boert/JU-TE-Computer/Bilder/Speichermodul_Typ_A.jpg

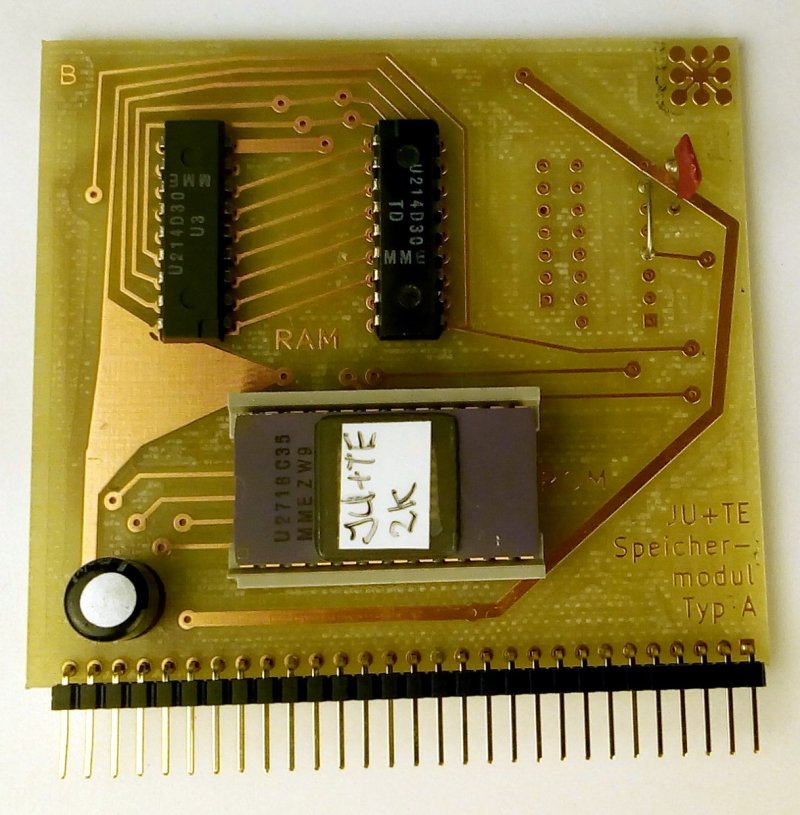
Bilder/Speichermodul_Typ_A.jpg
