boert/JU-TE-Computer/Erweiterungen/Schaltplan__V24-Interface.pdf

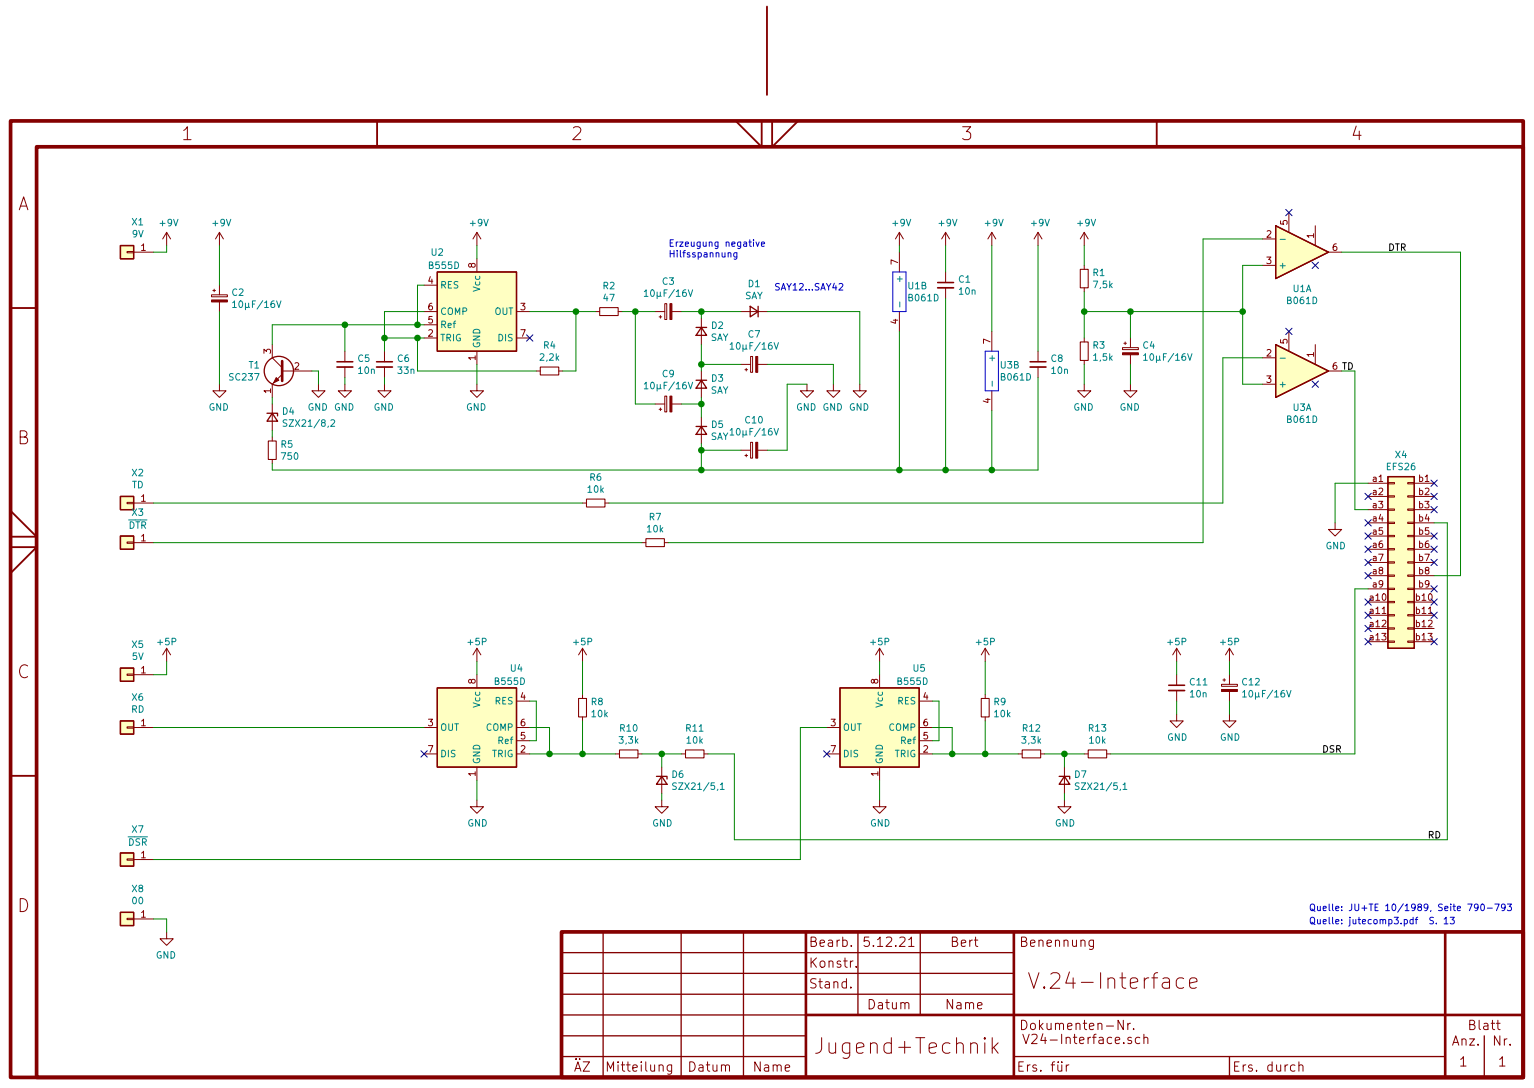
[picture p29: page 1]

1 TRIG 2 OUT 3 RES 4 Ref 5 COMP 6 DIS 7 Vcc 8 U2 B555D

1 TRIG 2 OUT 3 RES 4 Ref 5 COMP 6 DIS 7 Vcc 8 U4 B555D GND GND GND

1 TRIG 2 OUT 3 RES 4 Ref 5 COMP 6 DIS 7 Vcc 8 U5 B555D

Datum | Name

Dokumenten-Nr. | | Blatt
