boert/JU-TE-Computer/Erweiterungen/Schaltplan__Magnetbandanschluss.pdf

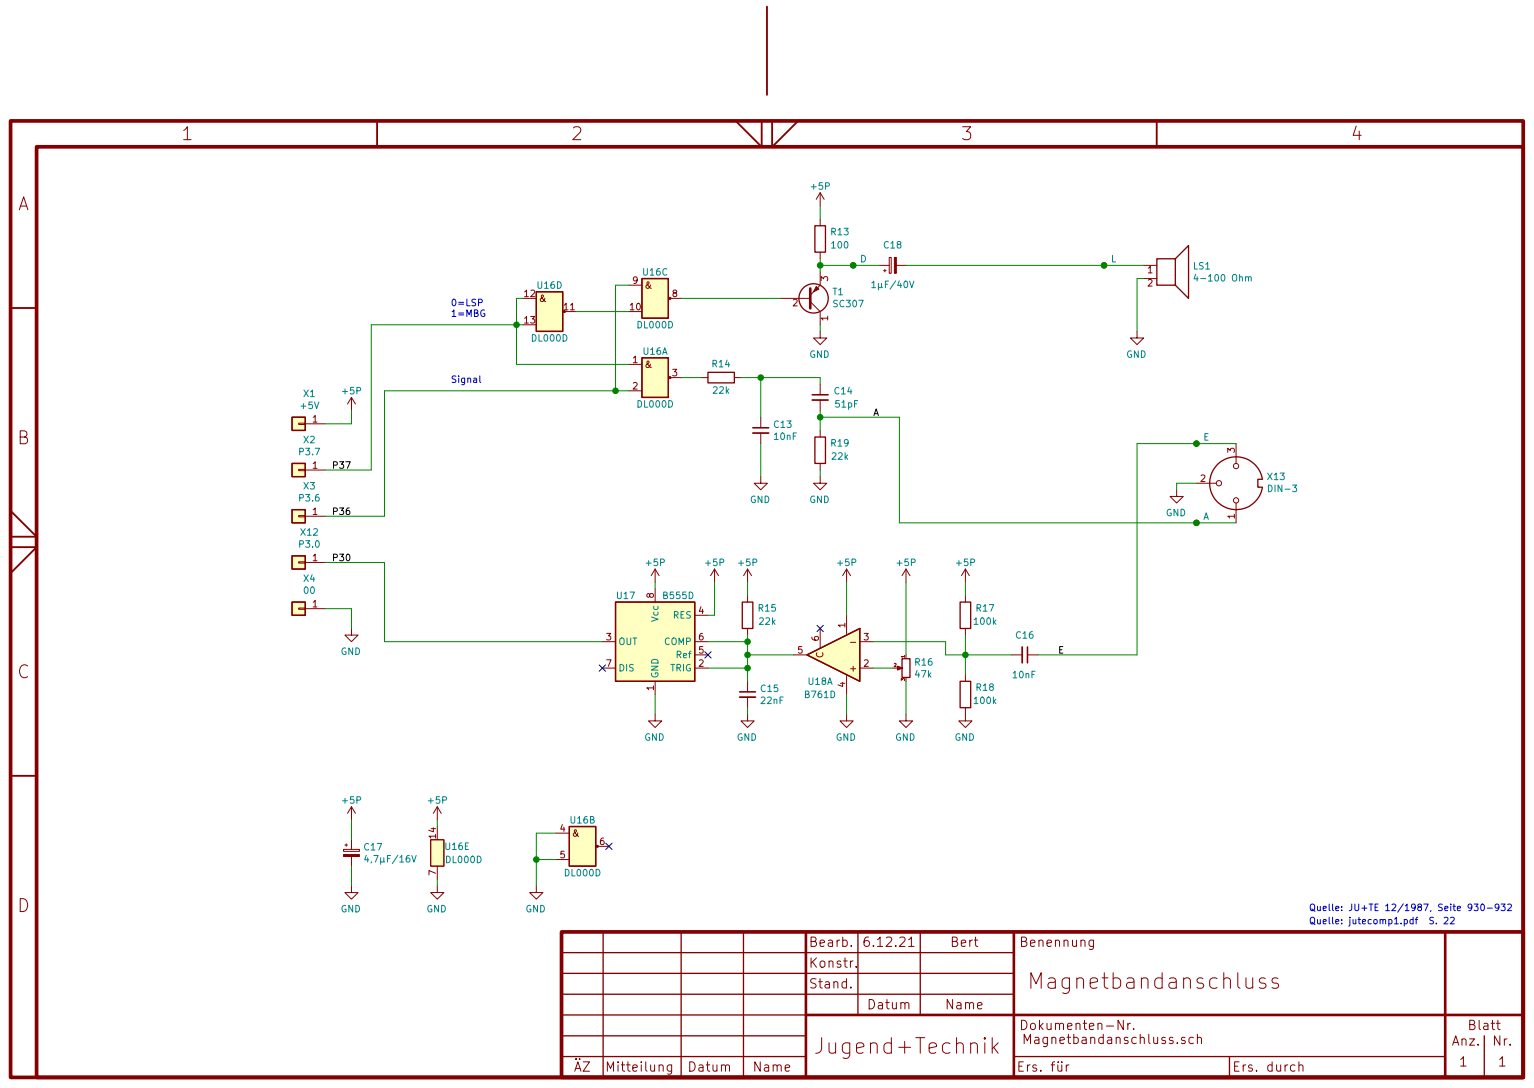
[picture p46: page 1]

1 TRIG 2 OUT 3 RES 4 Ref 5 COMP 6 DIS 7 Vcc U17 8B555D

Quelle: JU+TE 12/1987, Seite 930-932 Quelle: jutecomp1.pdf S. 22

Datum | Name

Dokumenten-Nr. | | Blatt
