boert/JU-TE-Computer/Erweiterungen/Schaltplan__AD-Wandler.pdf

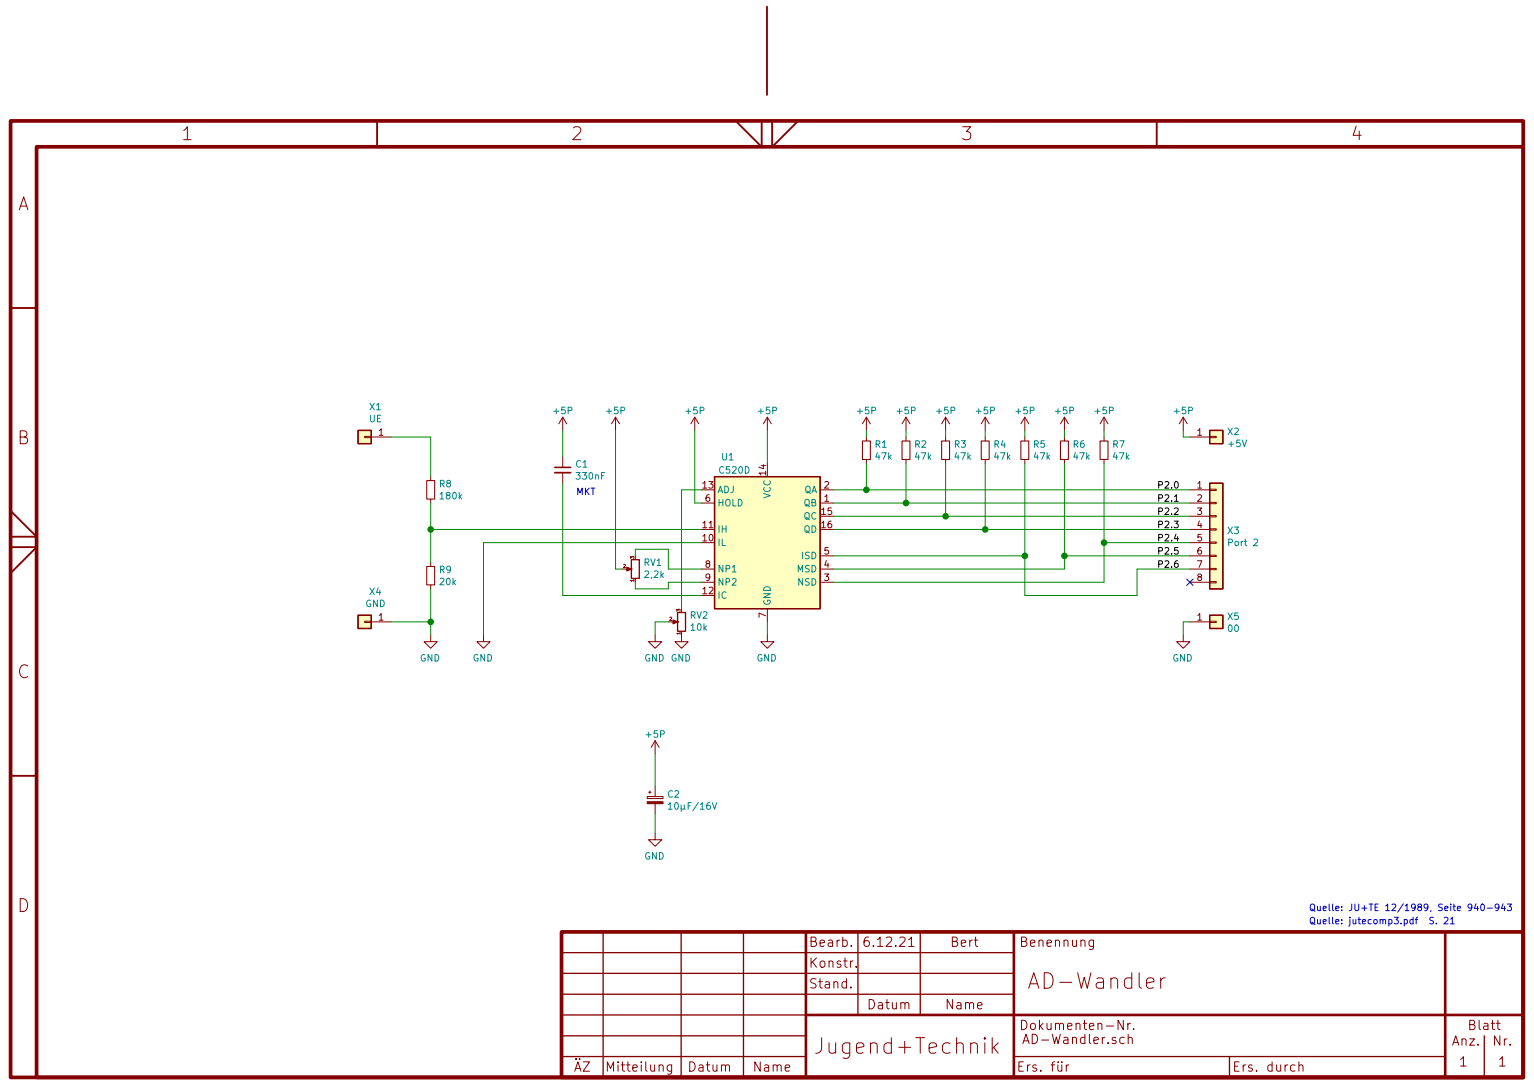
[picture p47: page 1]

Datum | Name

Dokumenten-Nr. | | Blatt
