boert/JU-TE-Computer/Erweiterungen/Schaltplan__IFSS-Interface.pdf

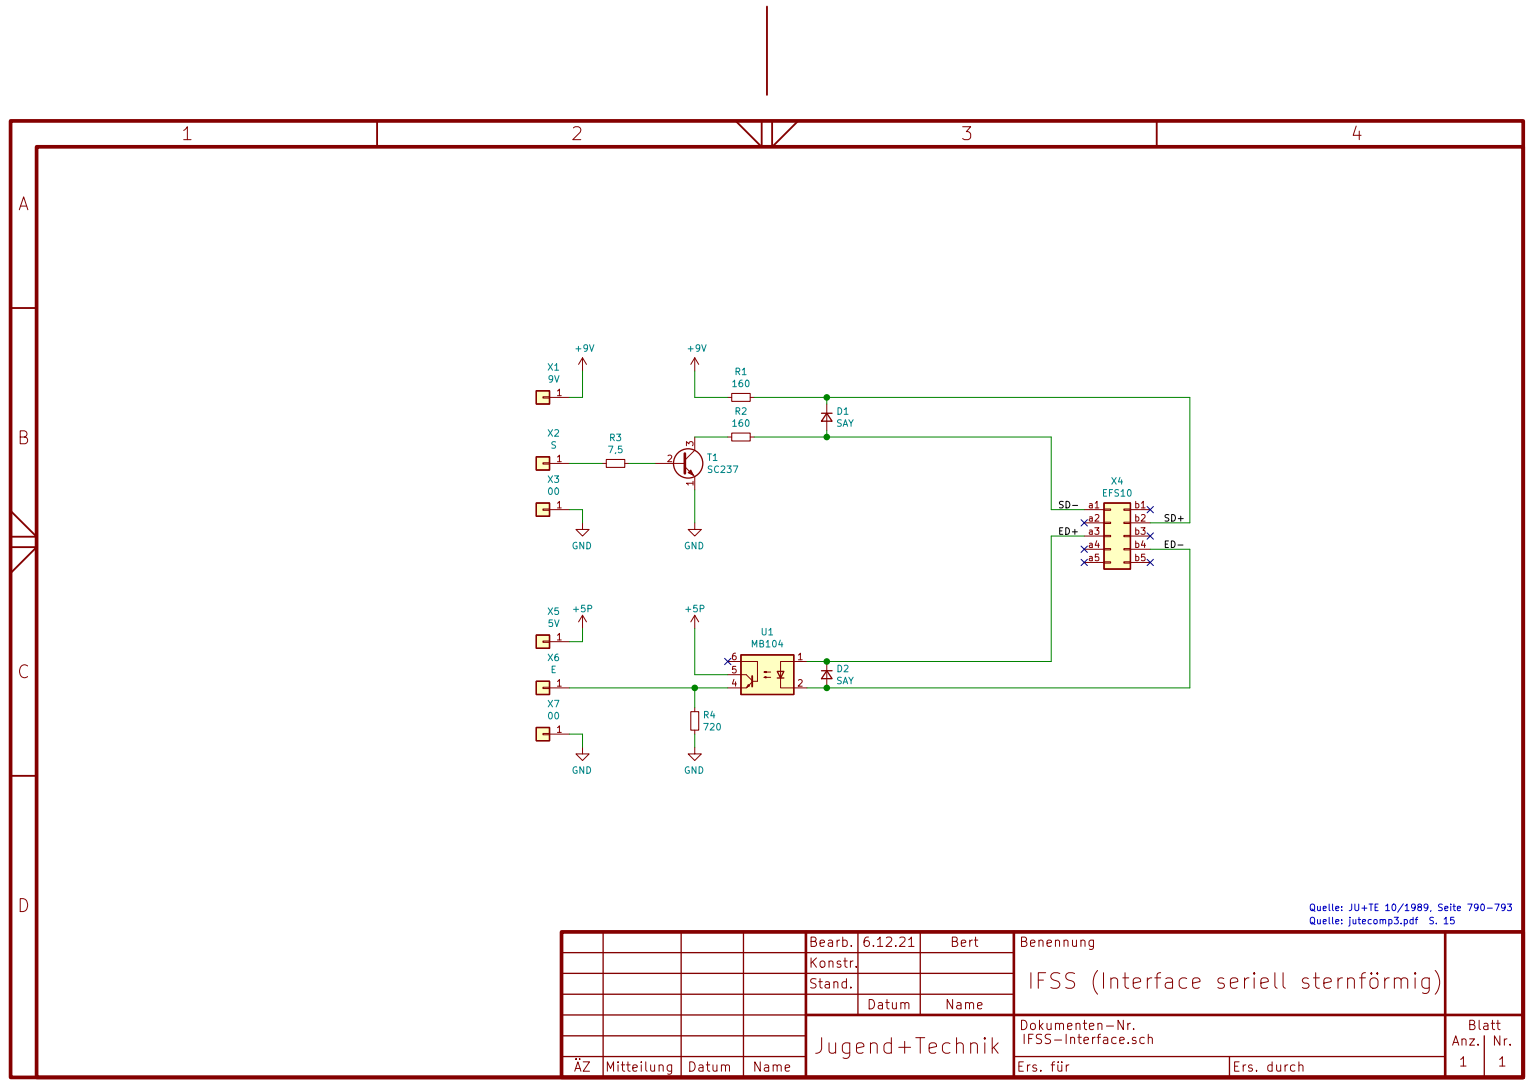
[picture p48: page 1]

Benennung
IFSS (Interface seriell sternförmig)

Datum | Name

Dokumenten-Nr. | | Blatt
