boert/JU-TE-Computer/Erweiterungen/Platine__Speichermodul_Typ_A.pdf

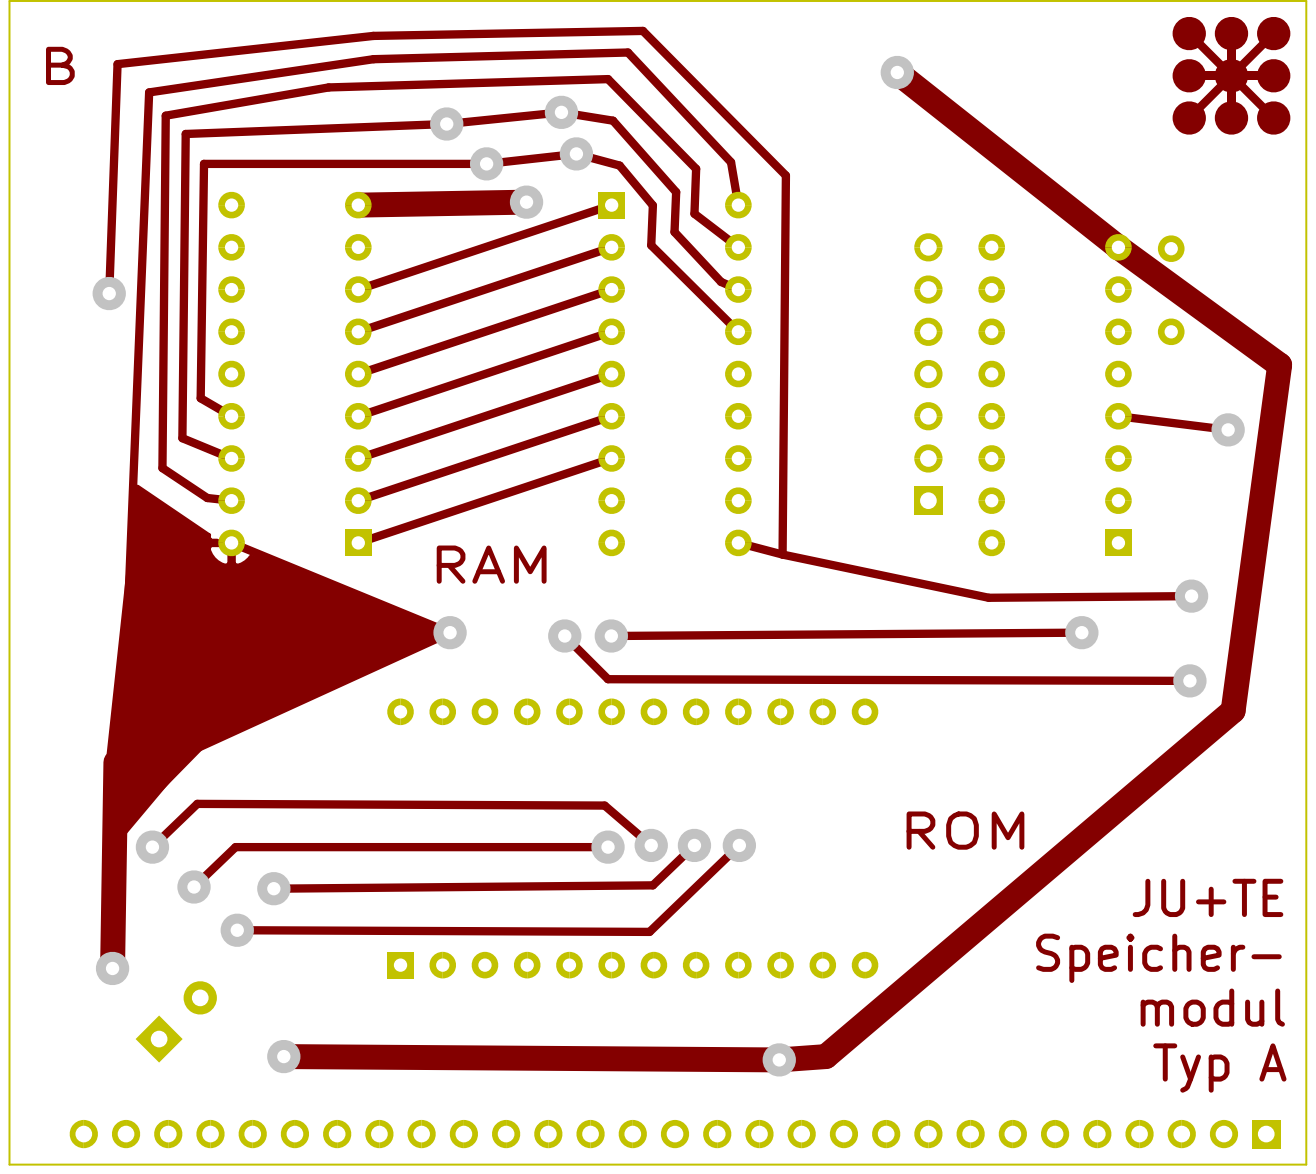
[picture p49: page 1]

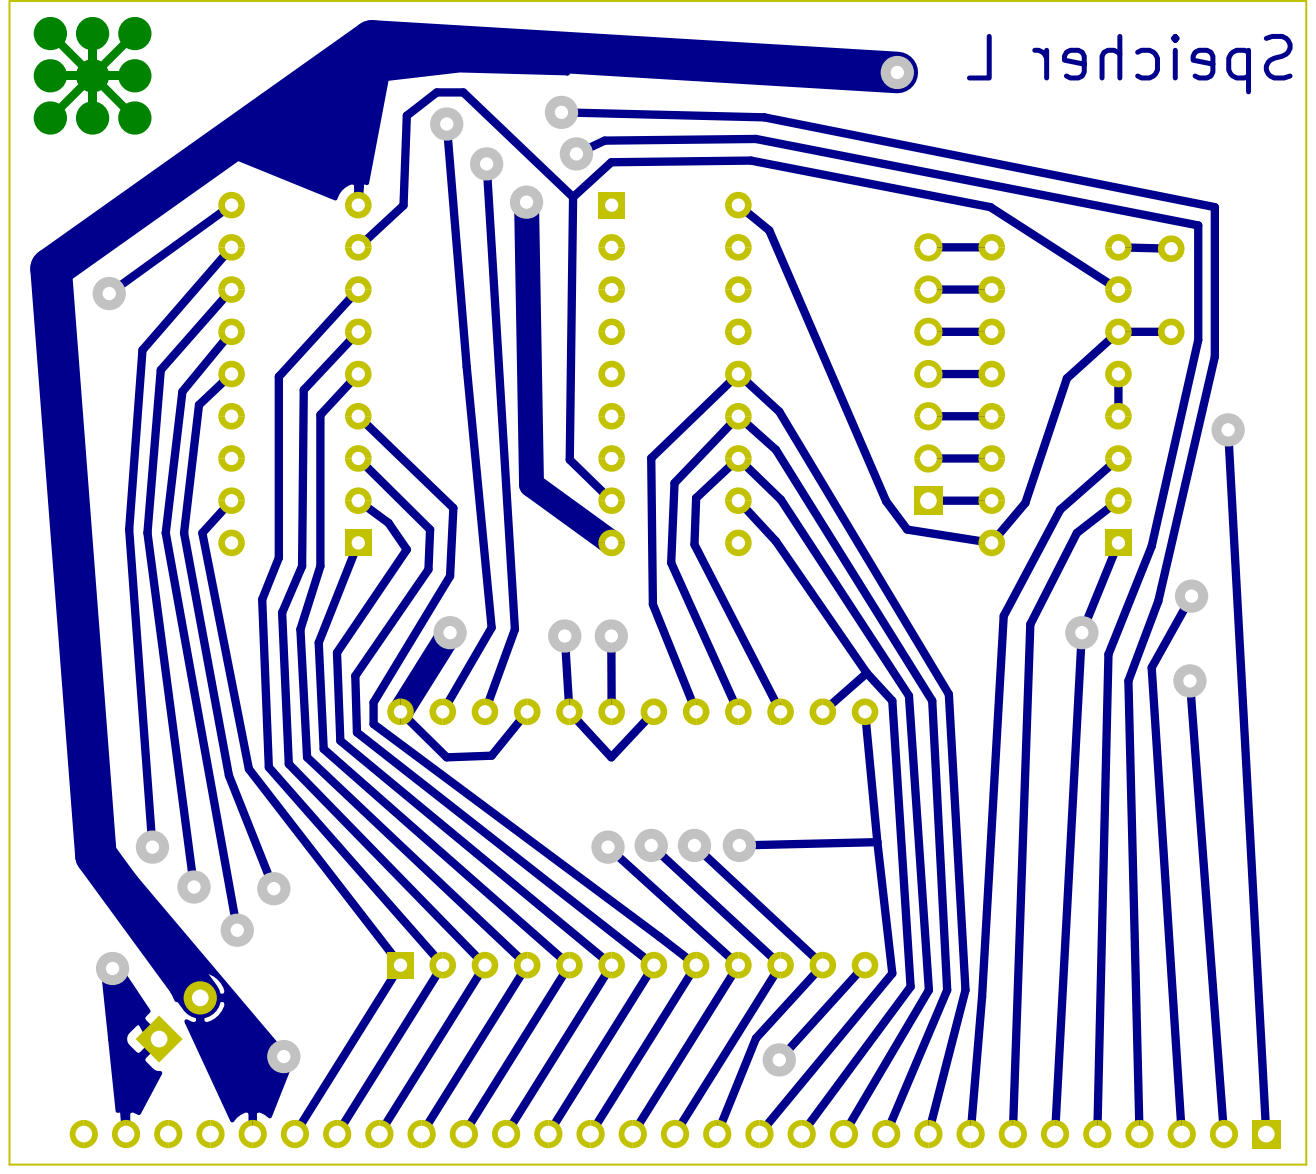
[picture p50: page 2]

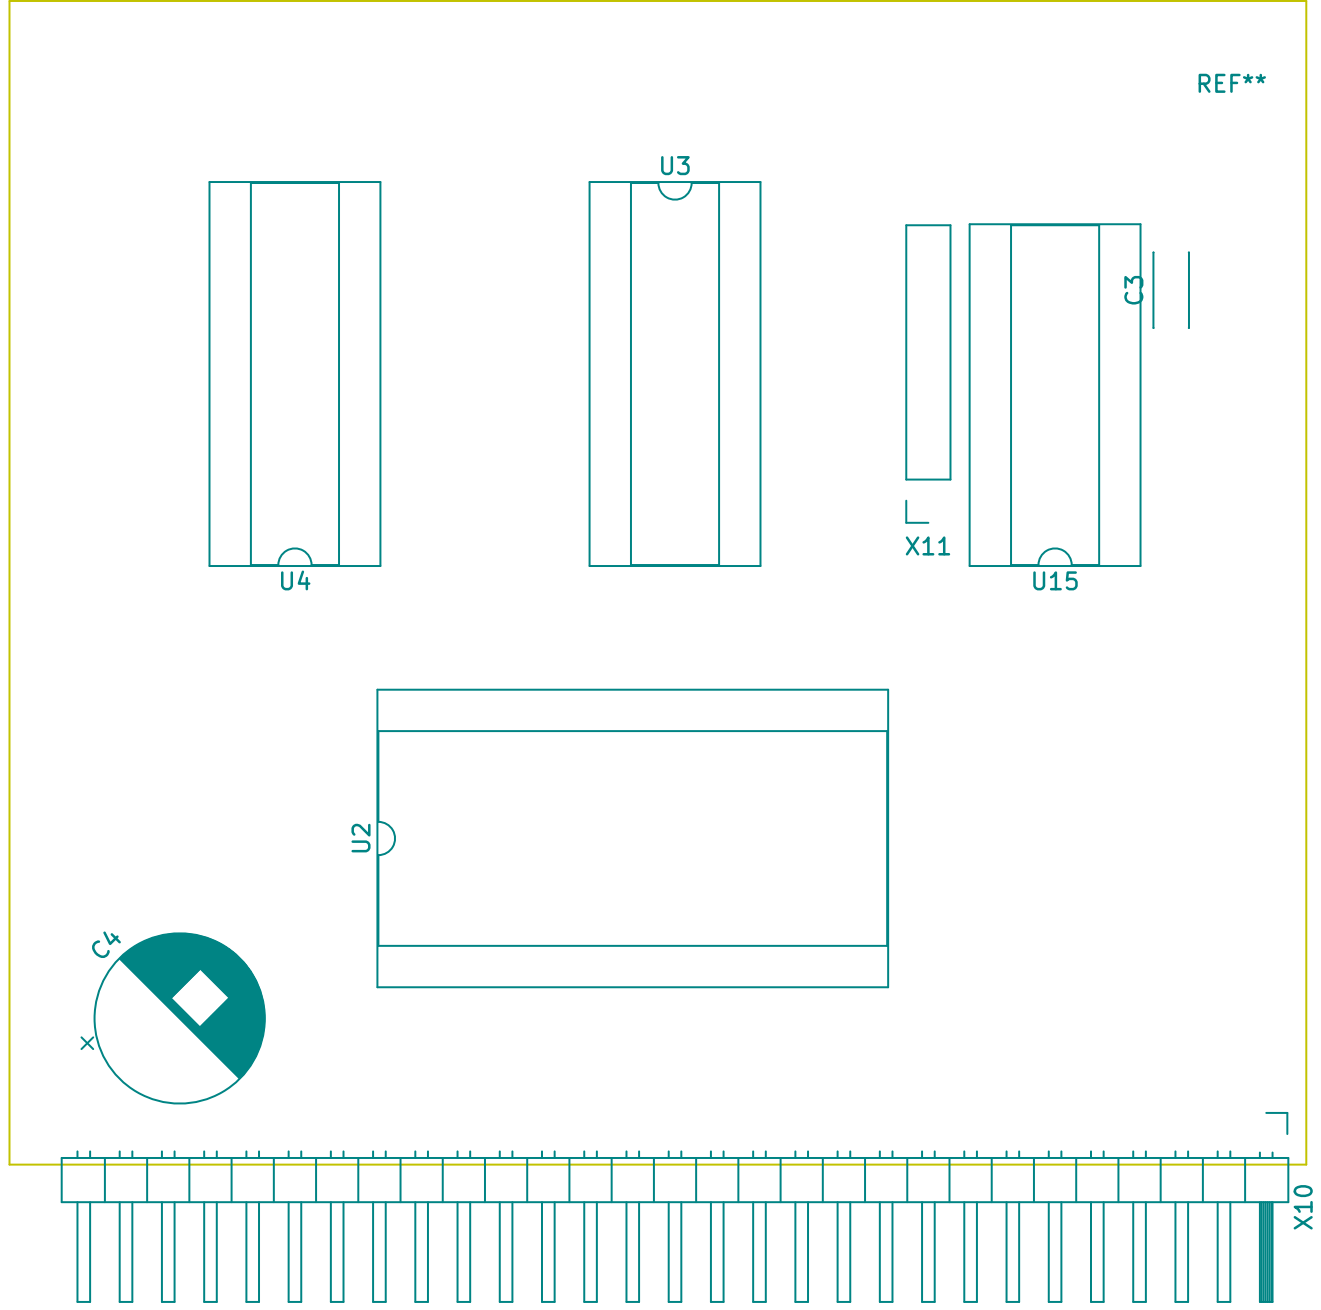
[picture p51: page 3]
