boert/JU-TE-Computer/Erweiterungen/Platine__Speichermodul_Typ_B.pdf

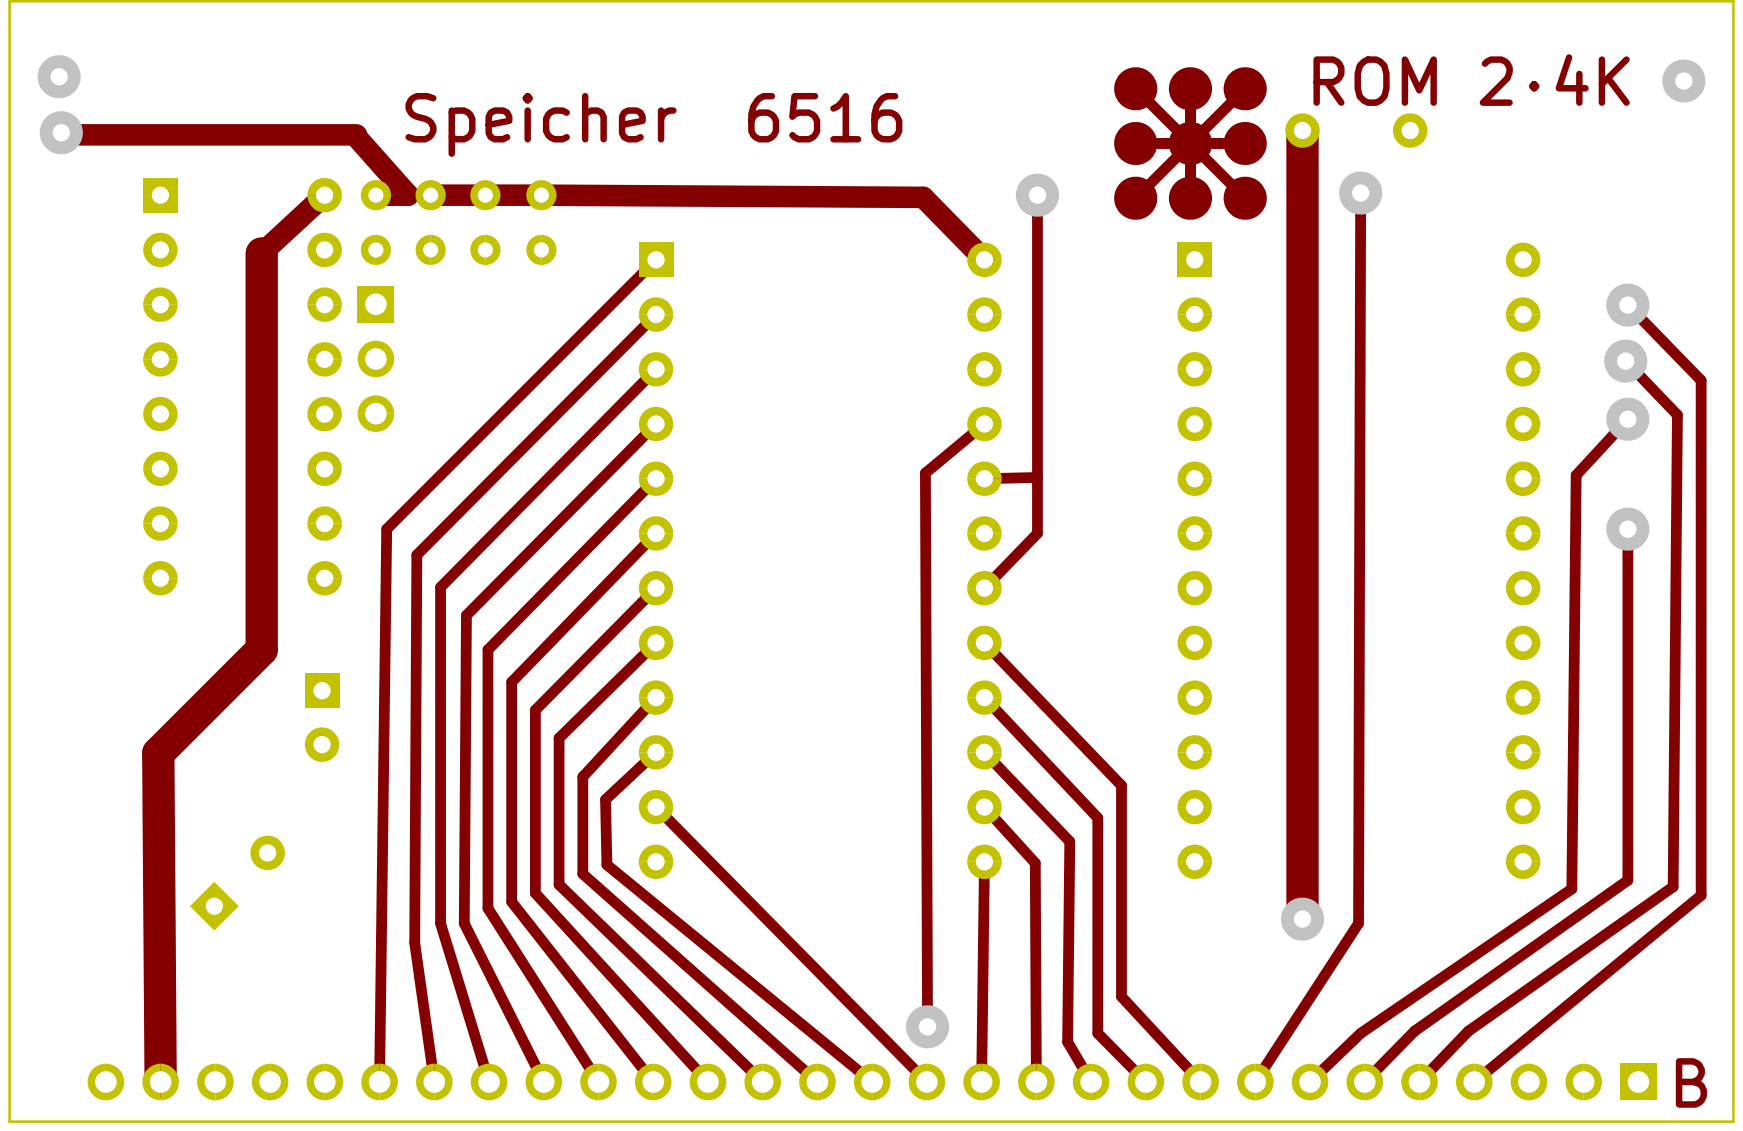
[picture p52: page 1]

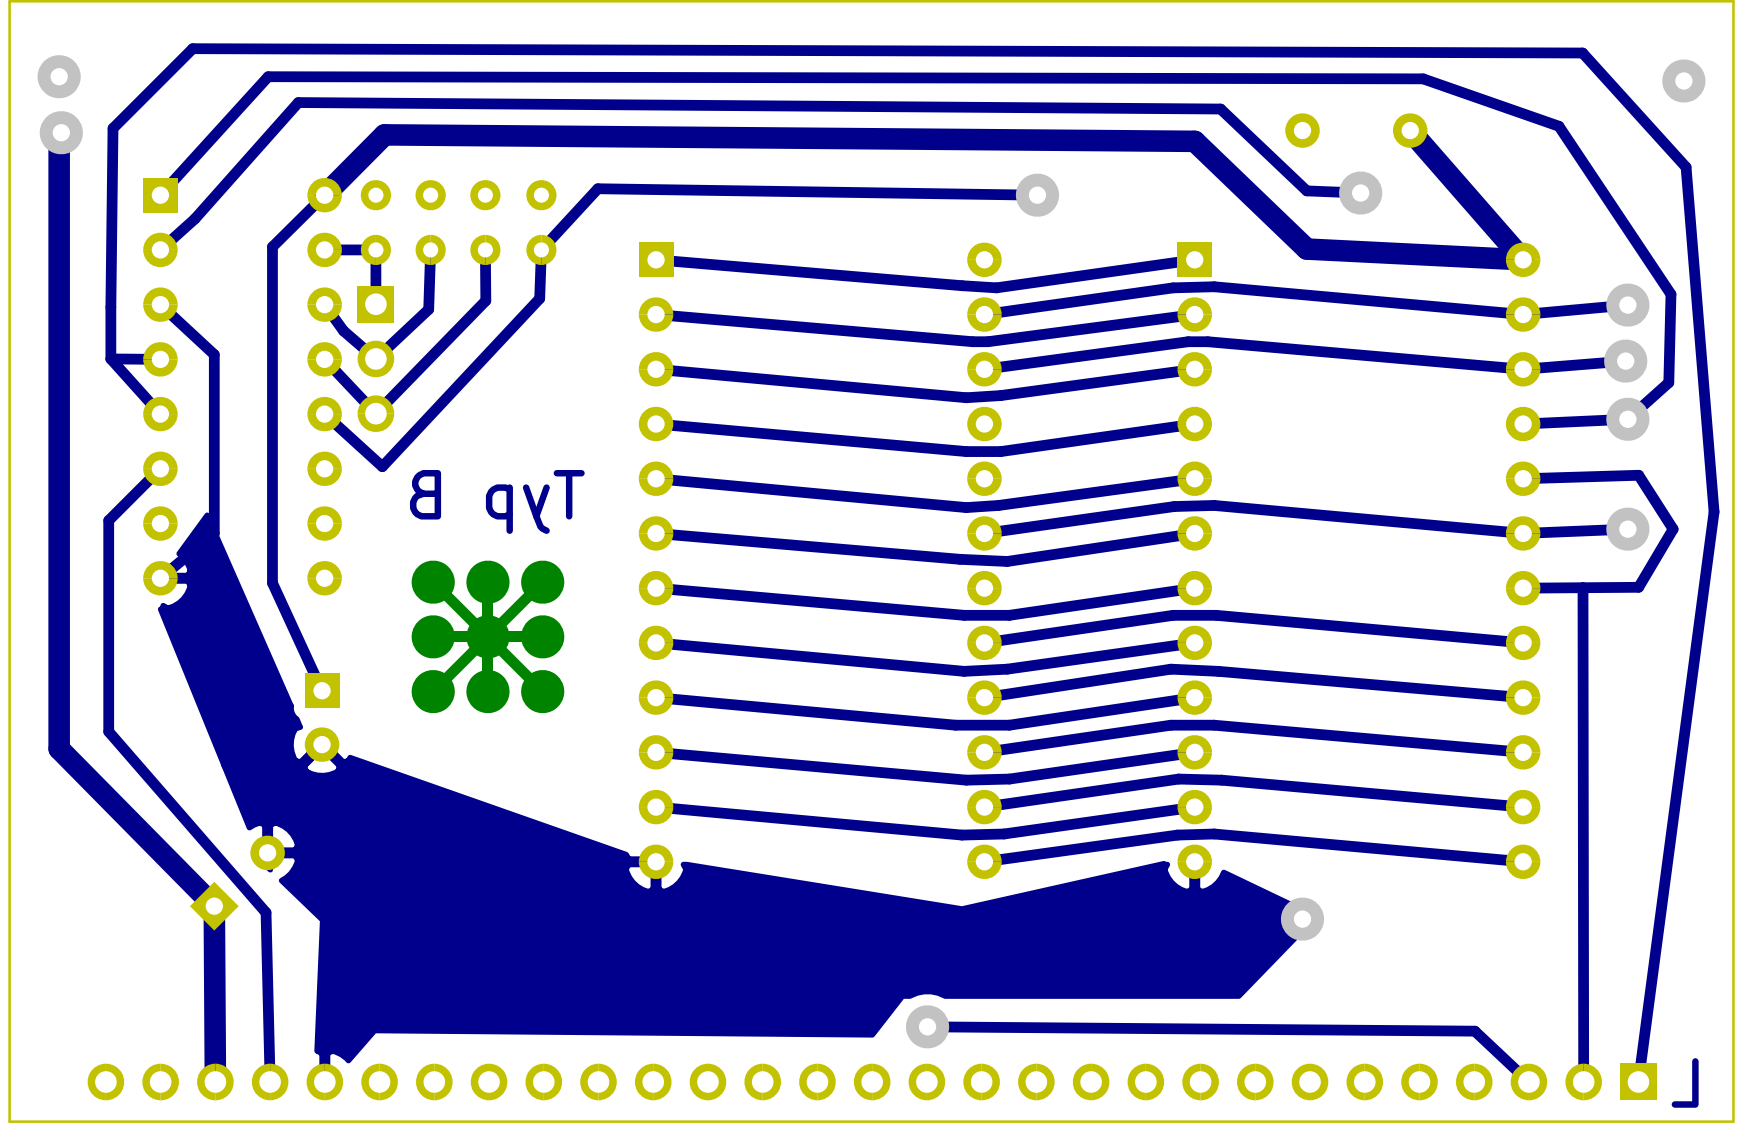
[picture p53: page 2]

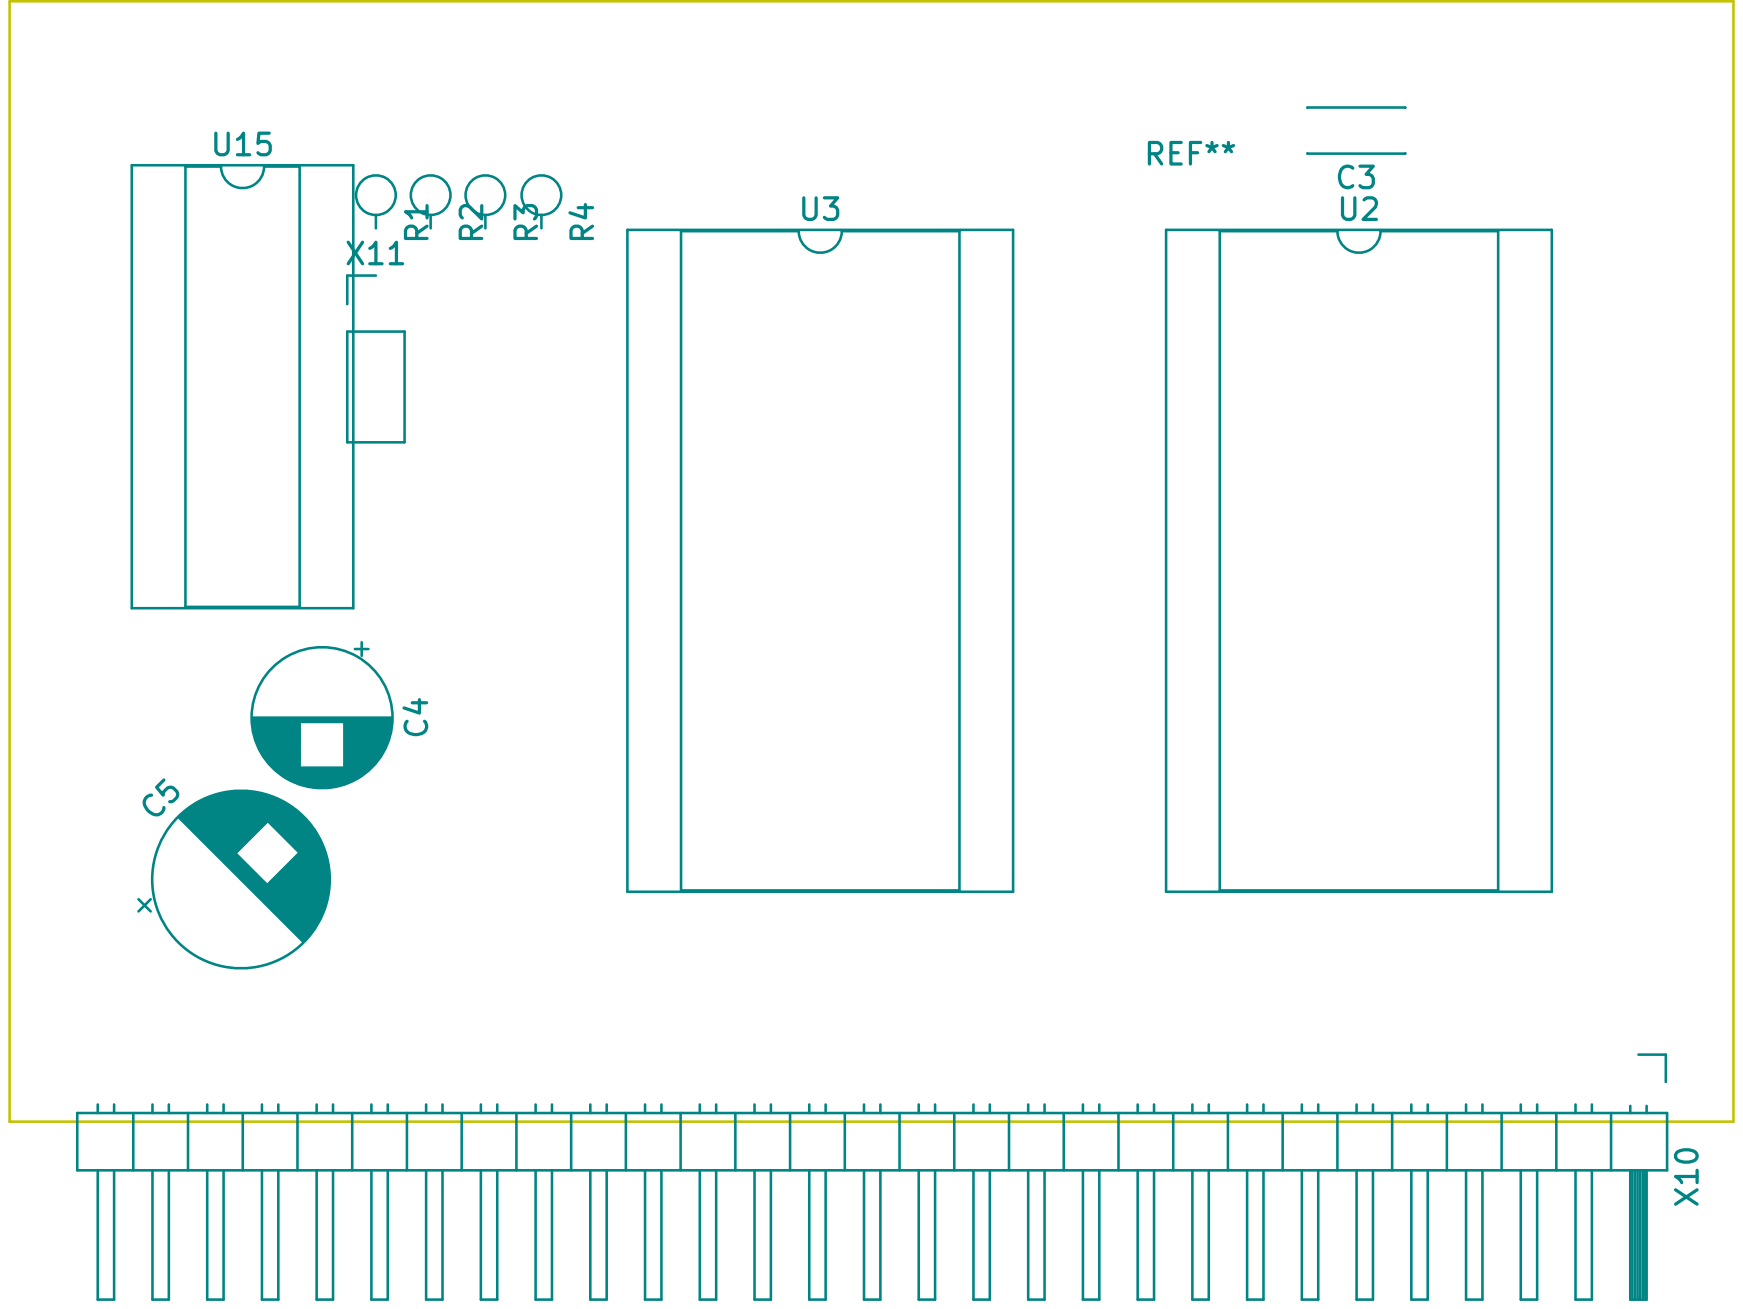
[picture p54: page 3]
