boert/JU-TE-Computer/Erweiterungen/Platine__Speichermodul_Typ_C.pdf

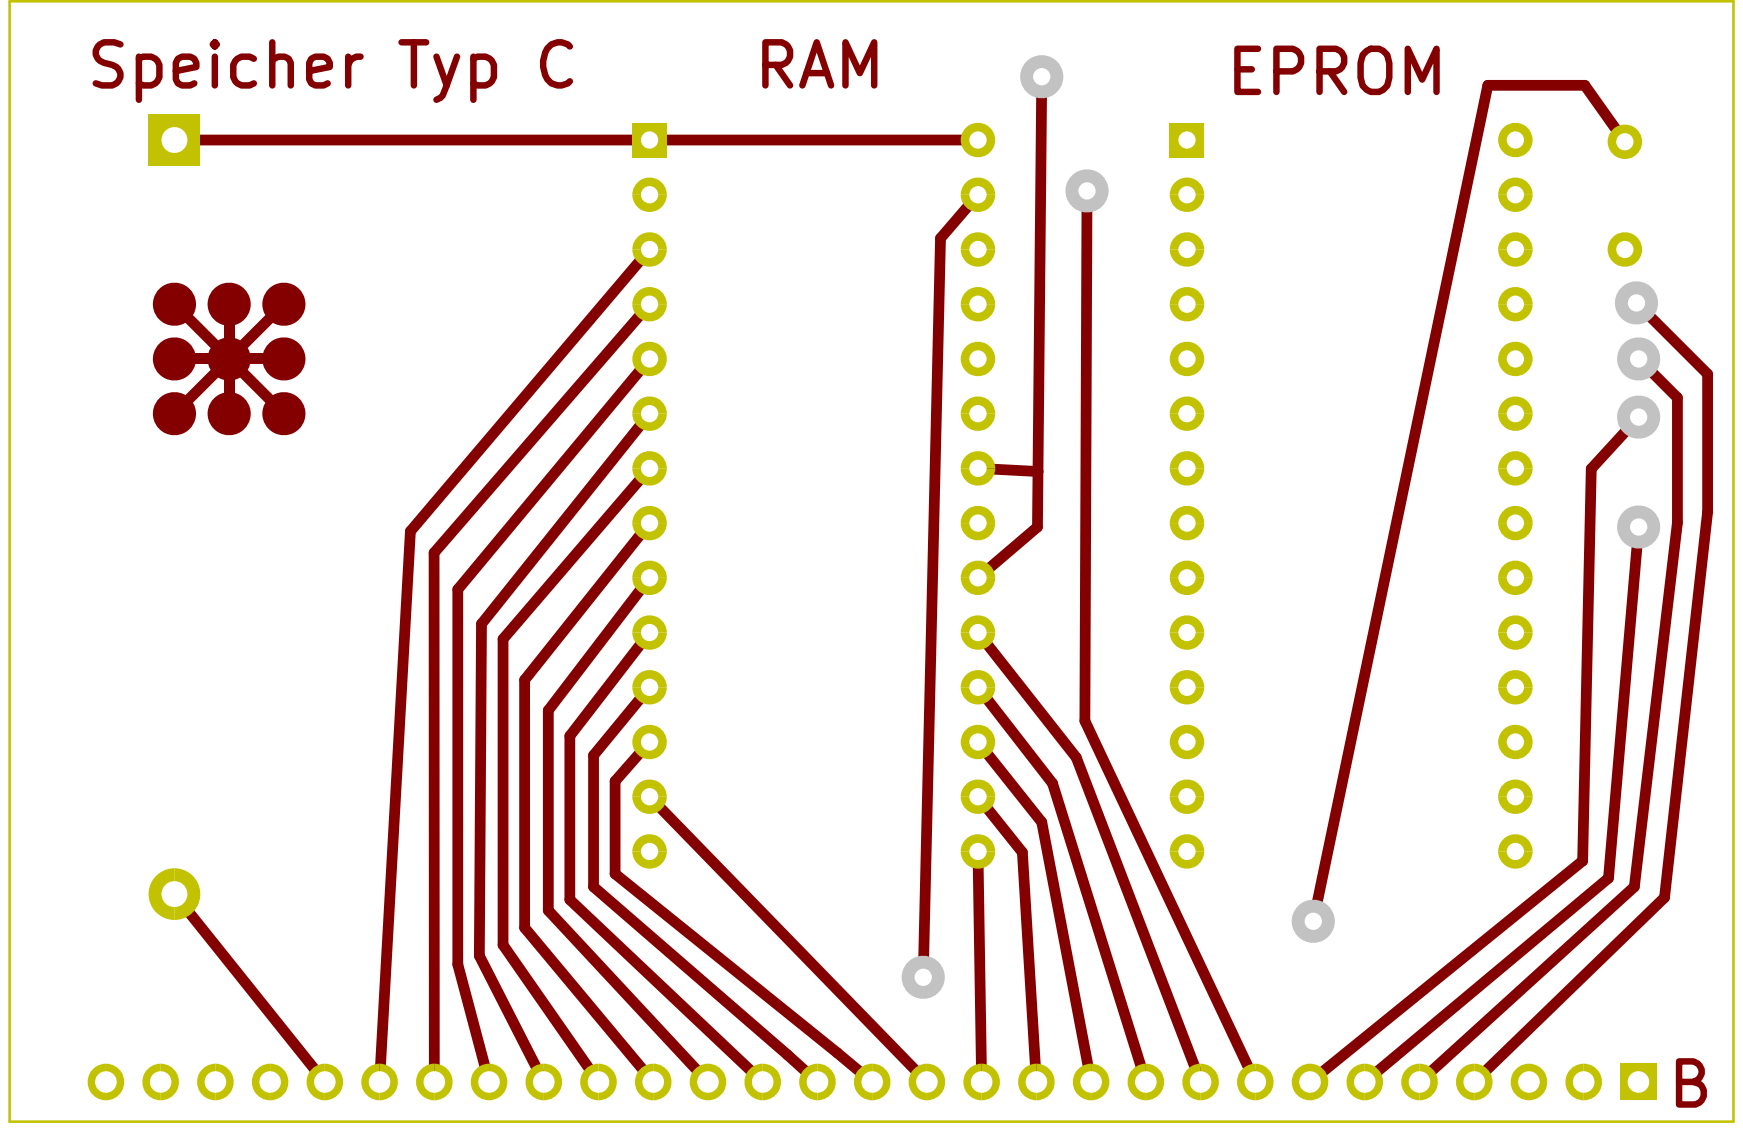
[picture p55: page 1]

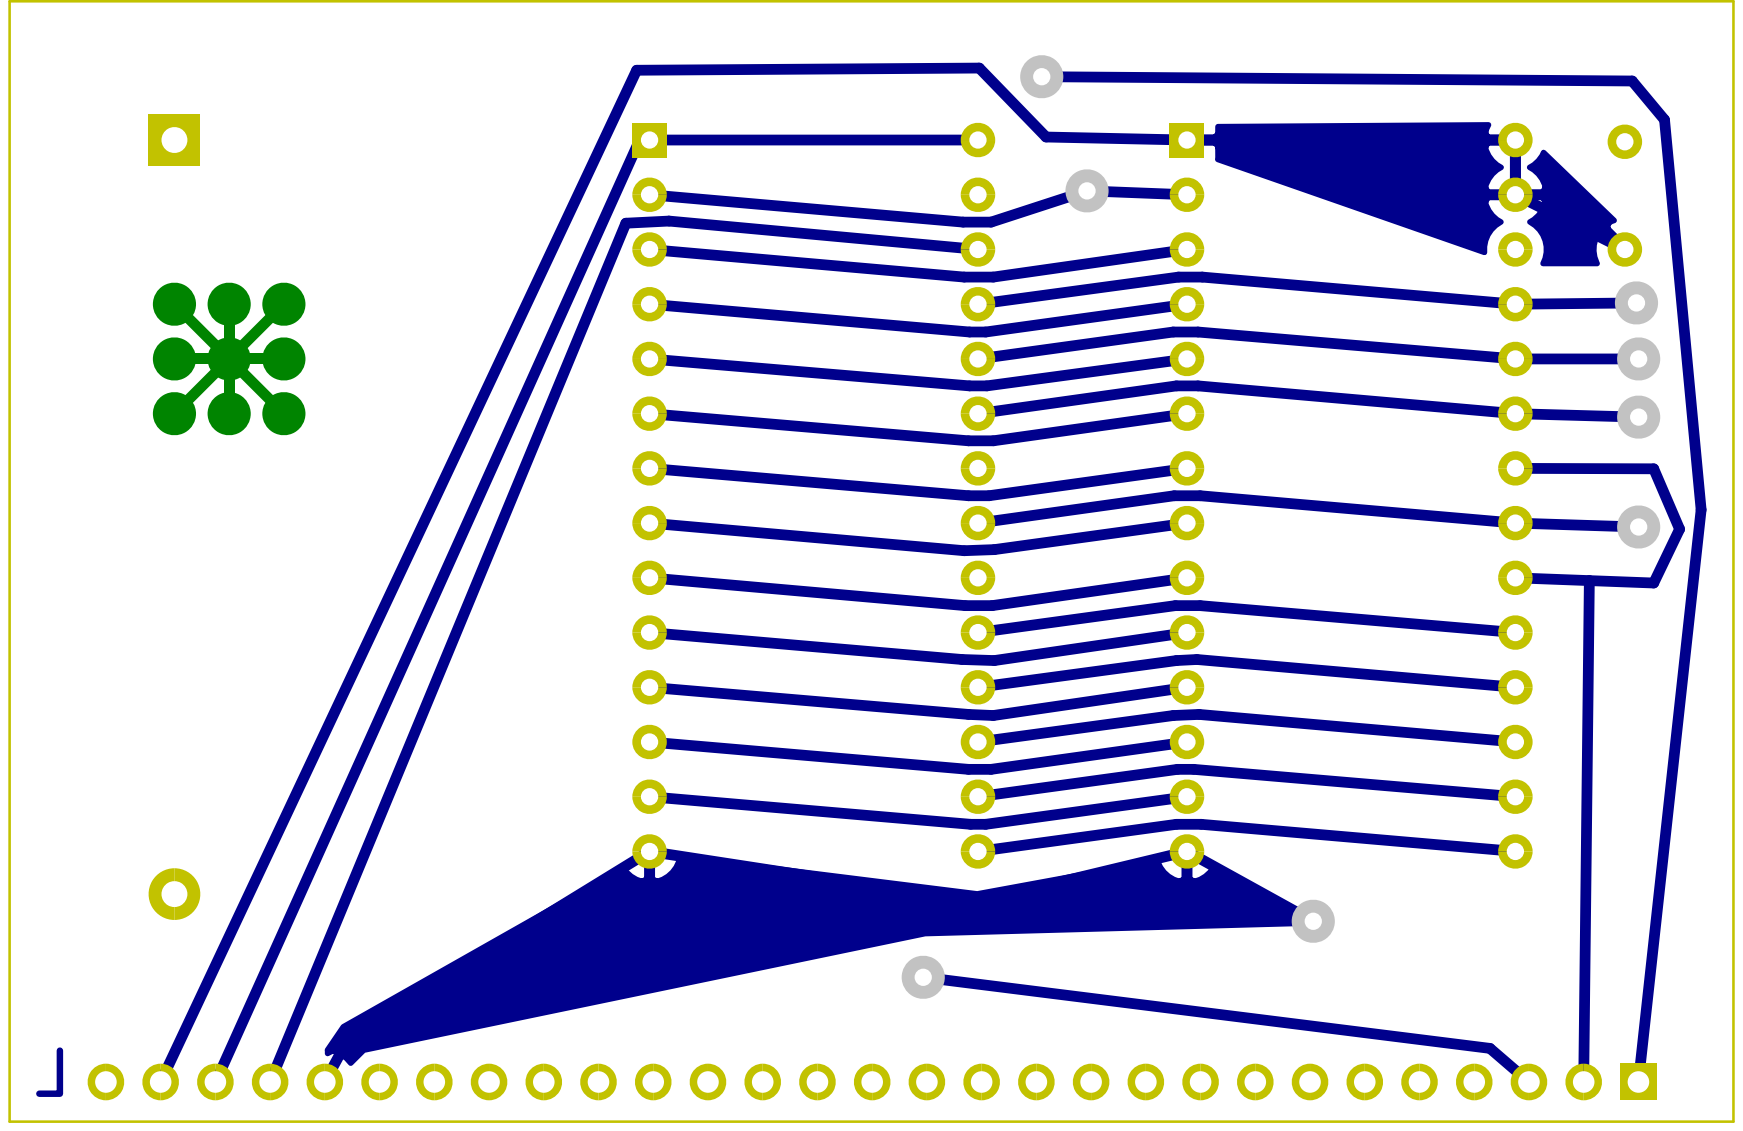
[picture p56: page 2]

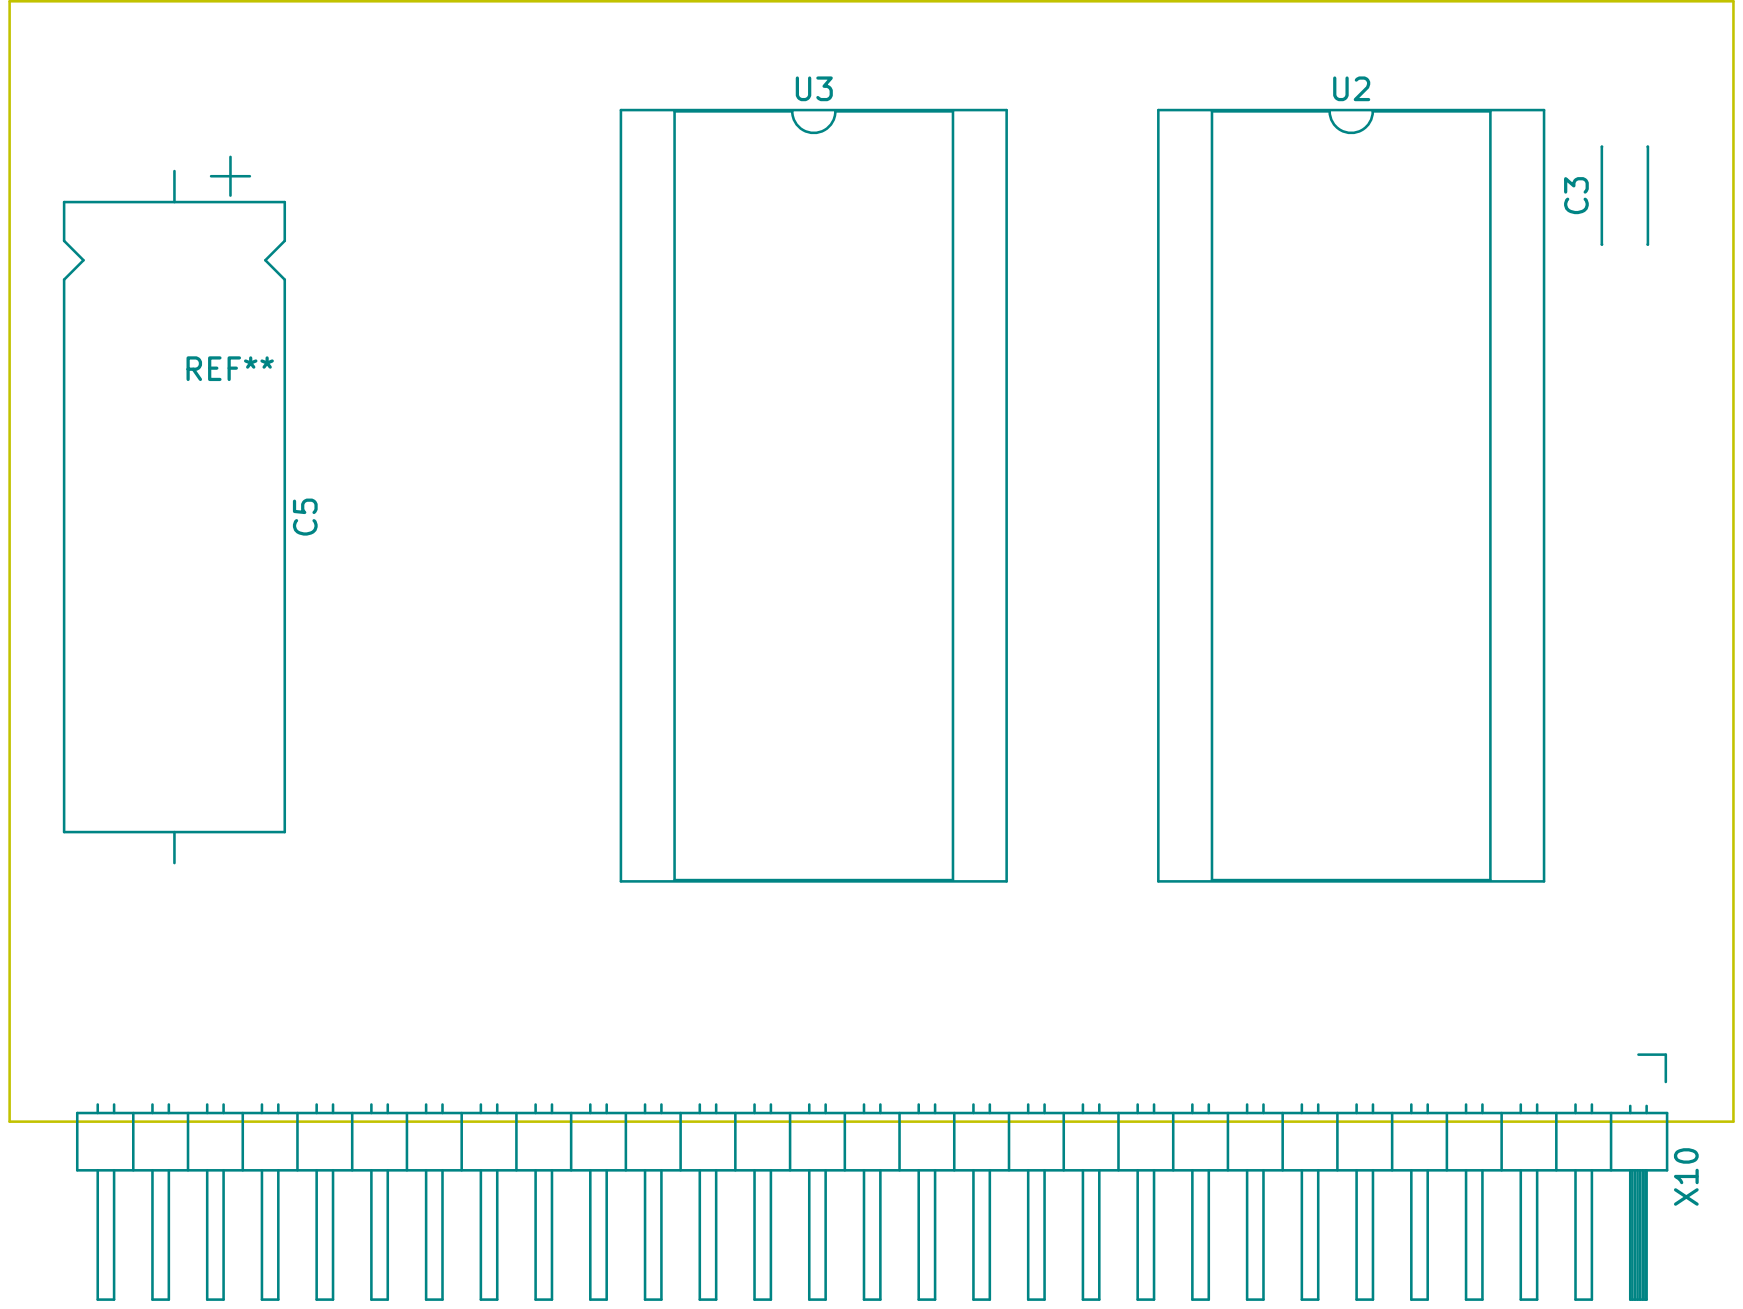
[picture p57: page 3]
