boert/JU-TE-Computer/Erweiterungen/Schaltplan__EPROM-Programmierzusatz.pdf

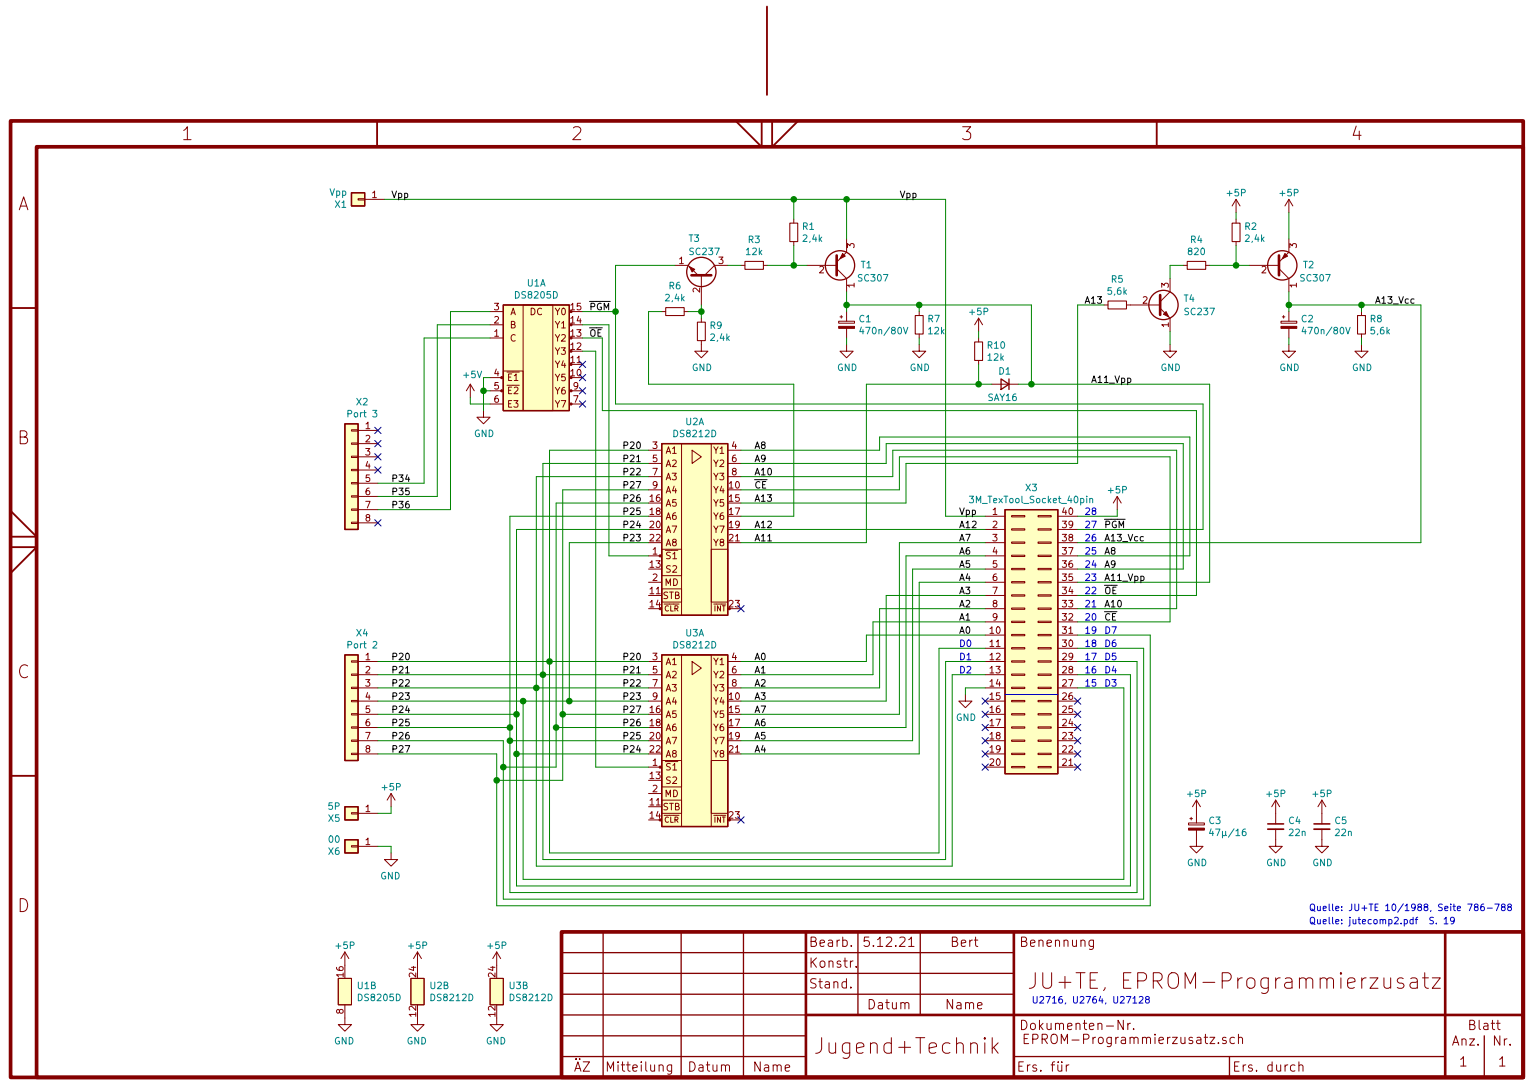
[picture p58: page 1]

PGM
A1A2A3A4A5A6A7A8 MD | Y1Y2Y3Y4Y5Y6Y7Y8 CLR INT S1 1 | 19 2

16 | 15
18 | 17

10
11 | | 30
12 | | 17
13 | | 28 16
14 | | 27

Datum | Name

Dokumenten-Nr. | | Blatt
