boert/JU-TE-Computer/Erweiterungen/Schaltplan__RAM-Stuetze.pdf

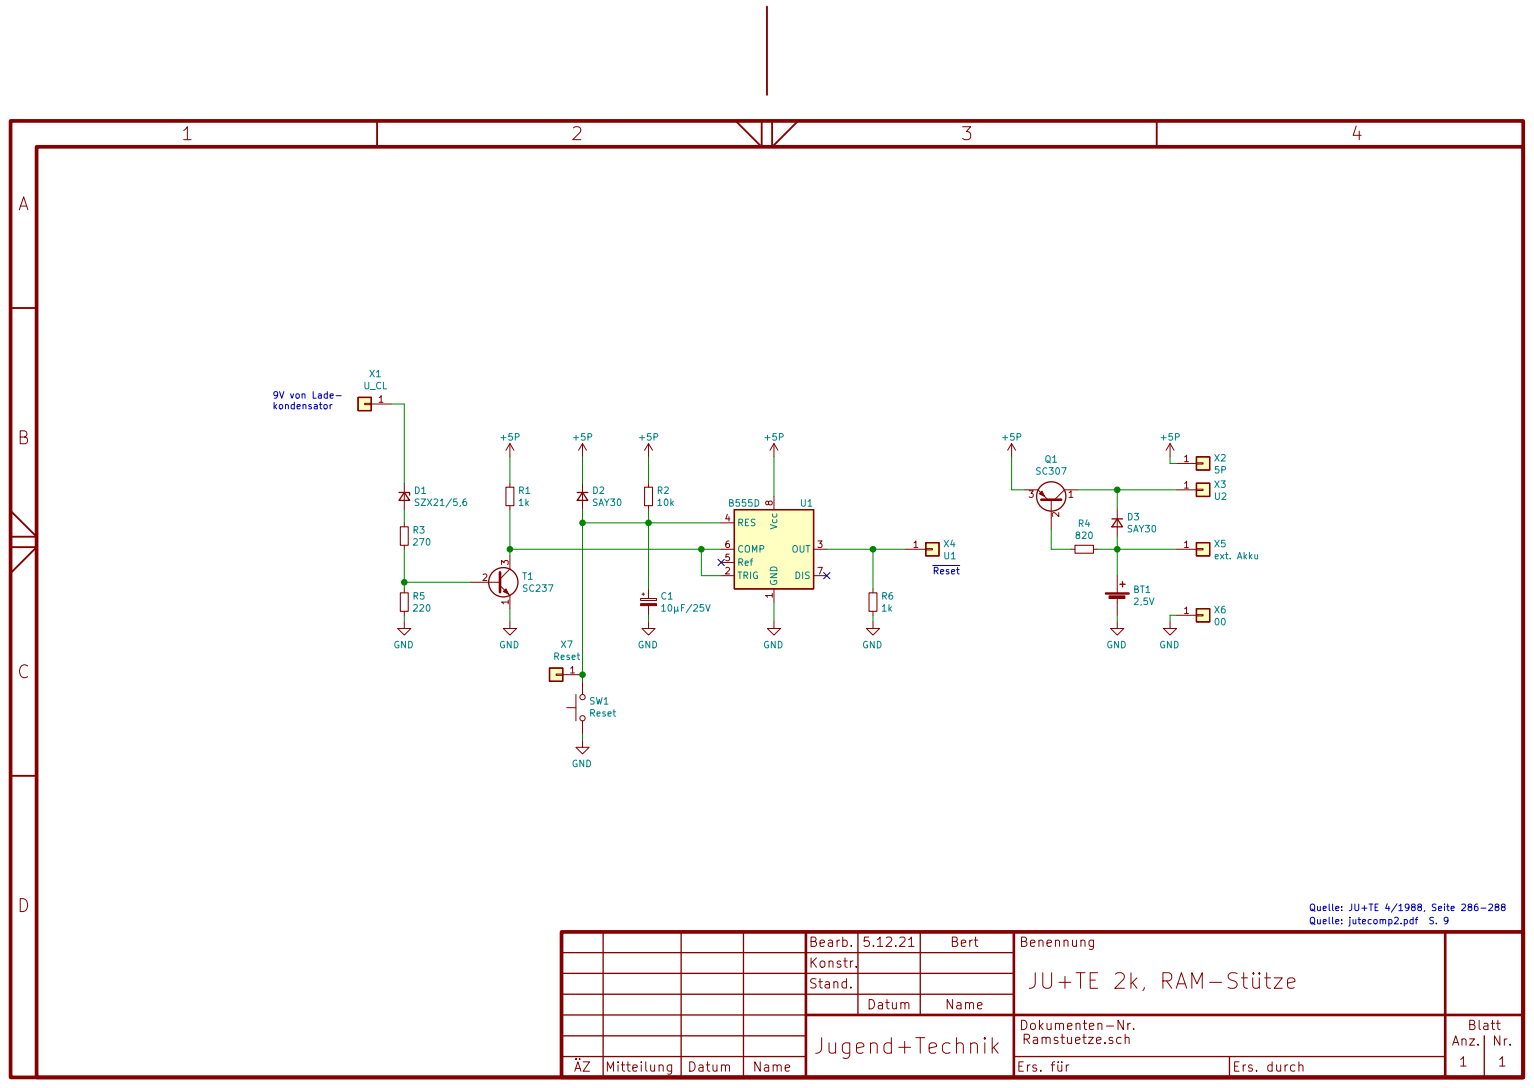
[picture p59: page 1]

1 TRIG 2 OUT 3 RES 4 Ref 5 COMP 6 DIS 7 Vcc B555D 8U1

Benennung
JU+TE 2k, RAM-Stütze

Datum | Name

Dokumenten-Nr. | | Blatt
