boert/JU-TE-Computer/Erweiterungen/Schaltplan__Speichermodul_Typ_A.pdf

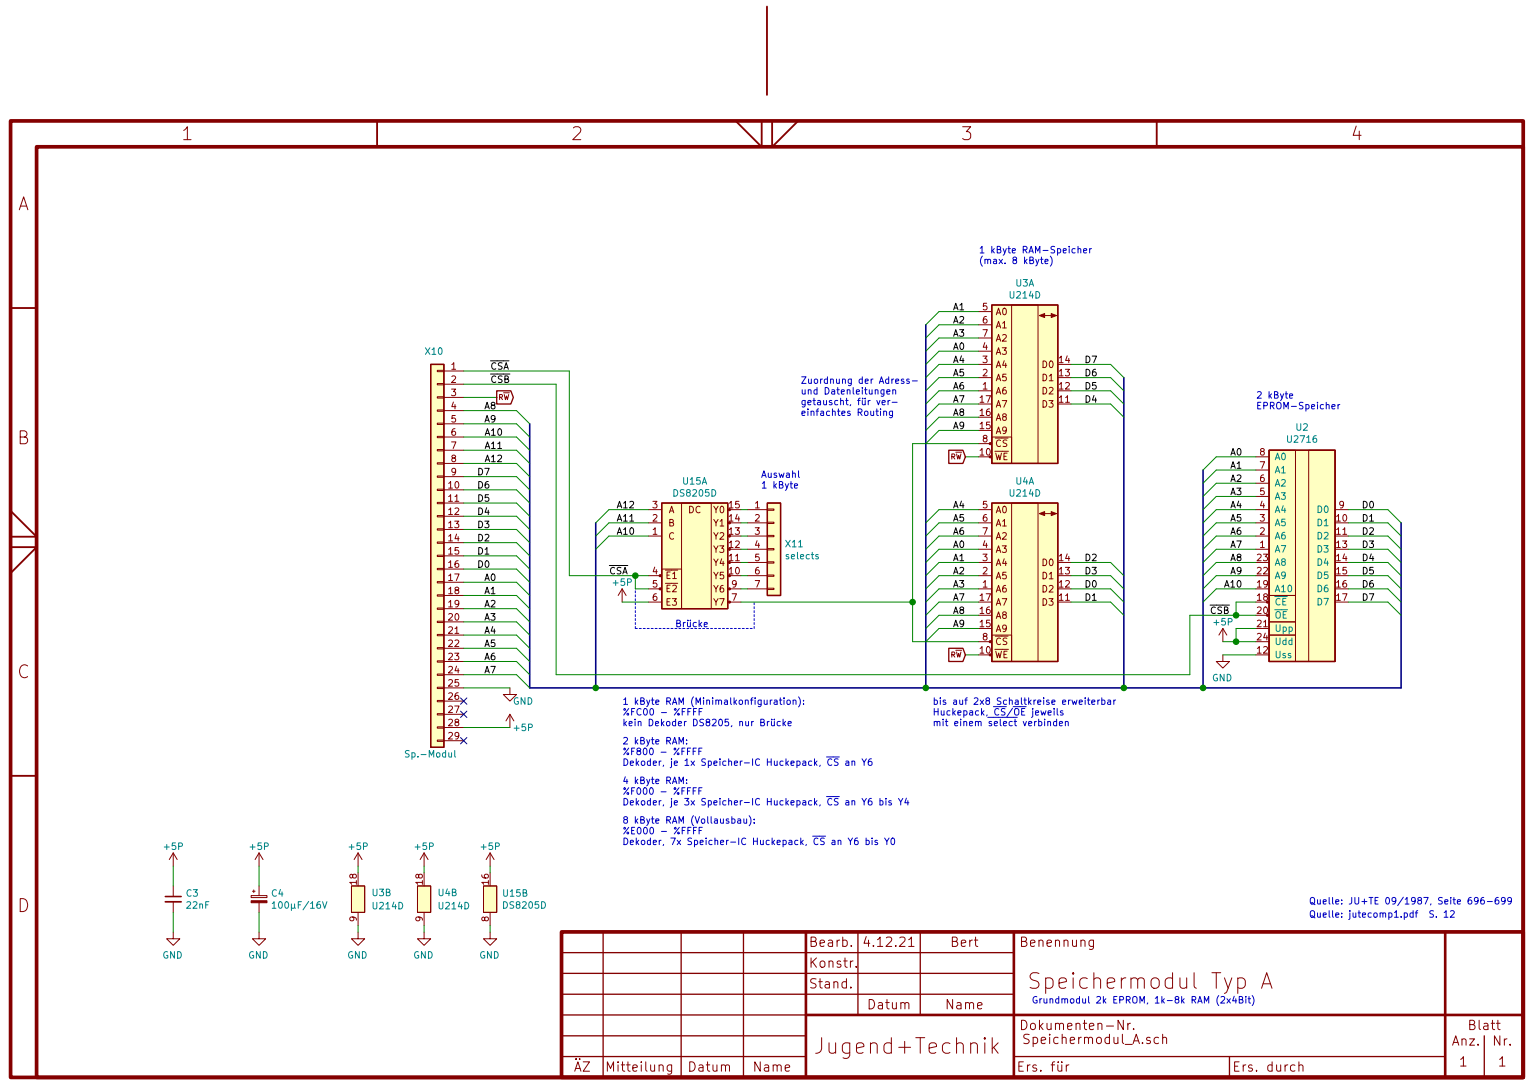
[picture p60: page 1]

kein Dekoder DS8205, nur BrückeAuswahl 1 kByte
A3 CSA

1 kByte RAM (Minimalkonfiguration): %FC00 - %FFFF

bis auf 2x8 Schaltkreise erweiterbar Huckepack, CS/OE jeweils mit einem select verbinden

2 kByte RAM: %F800 - %FFFF Dekoder, je 1x Speicher-IC Huckepack, CS an Y6

4 kByte RAM: %F000 - %FFFF Dekoder, je 3x Speicher-IC Huckepack, CS an Y6 bis Y4

8 kByte RAM (Vollausbau): %E000 - %FFFF Dekoder, 7x Speicher-IC Huckepack, CS an Y6 bis Y0

Datum | Name

Dokumenten-Nr. | | Blatt
