boert/JU-TE-Computer/Erweiterungen/Schaltplan__Speichermodul_Typ_C.pdf

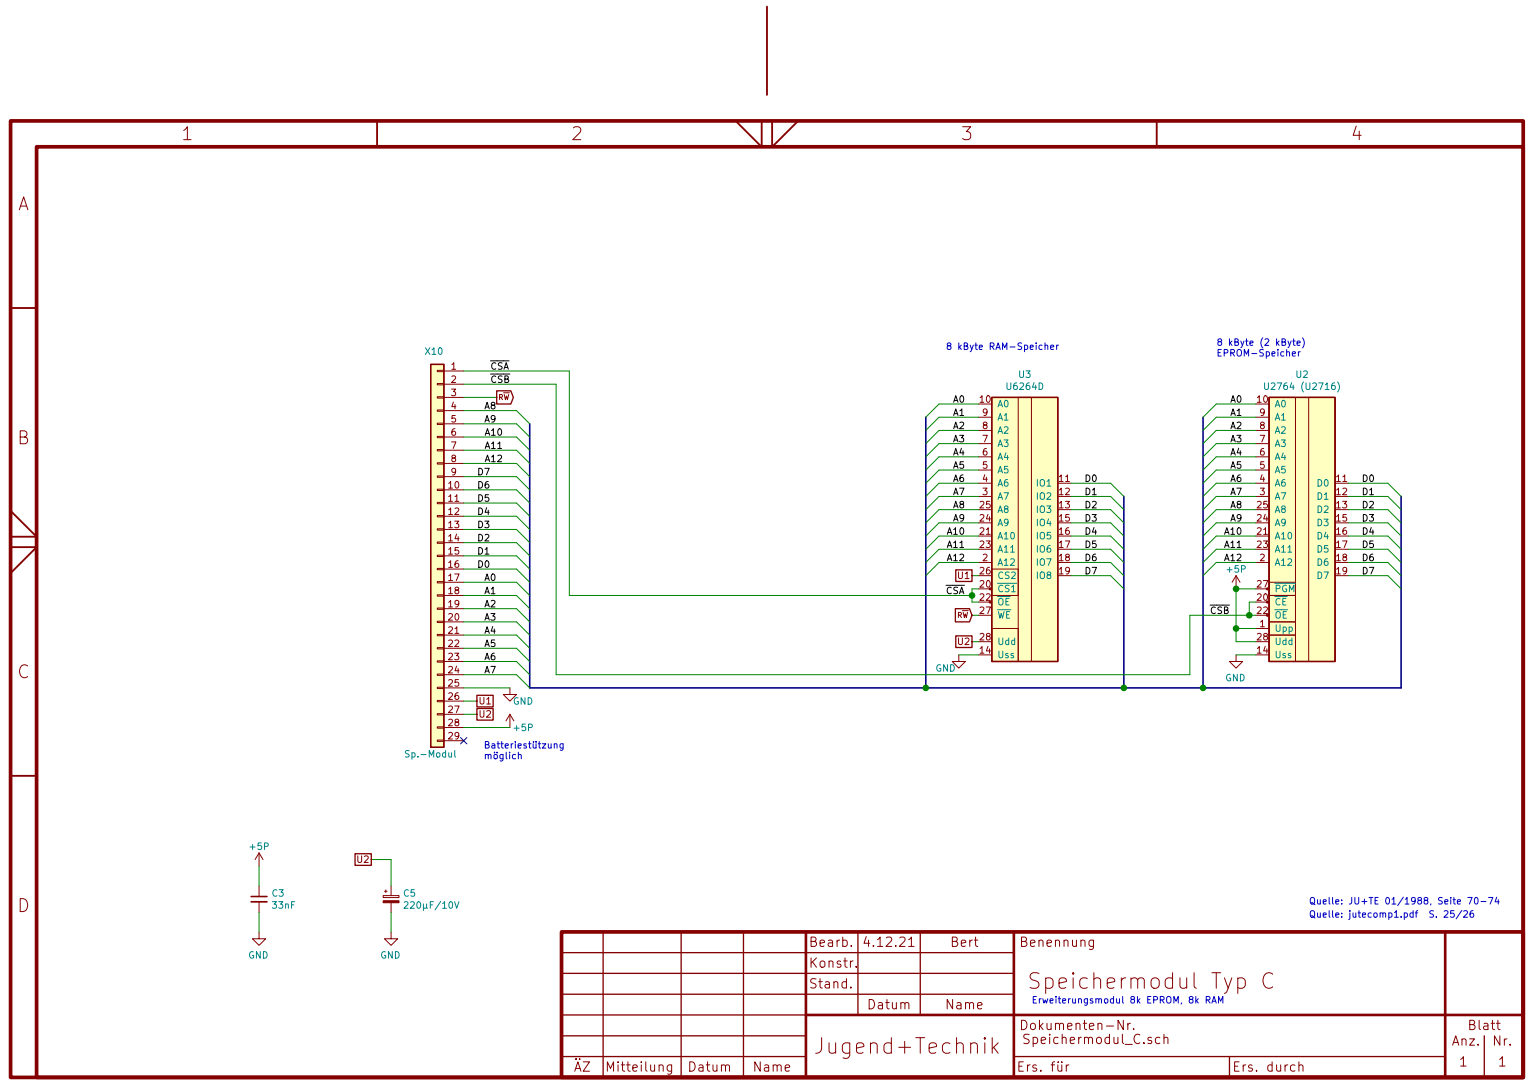
[picture p61: page 1]

EPROM-Speicher 8 kByte RAM-Speicher

Datum | Name

Dokumenten-Nr. | | Blatt
