boert/JU-TE-Computer/Erweiterungen/Schaltplan__Speichermodul_Typ_D.pdf

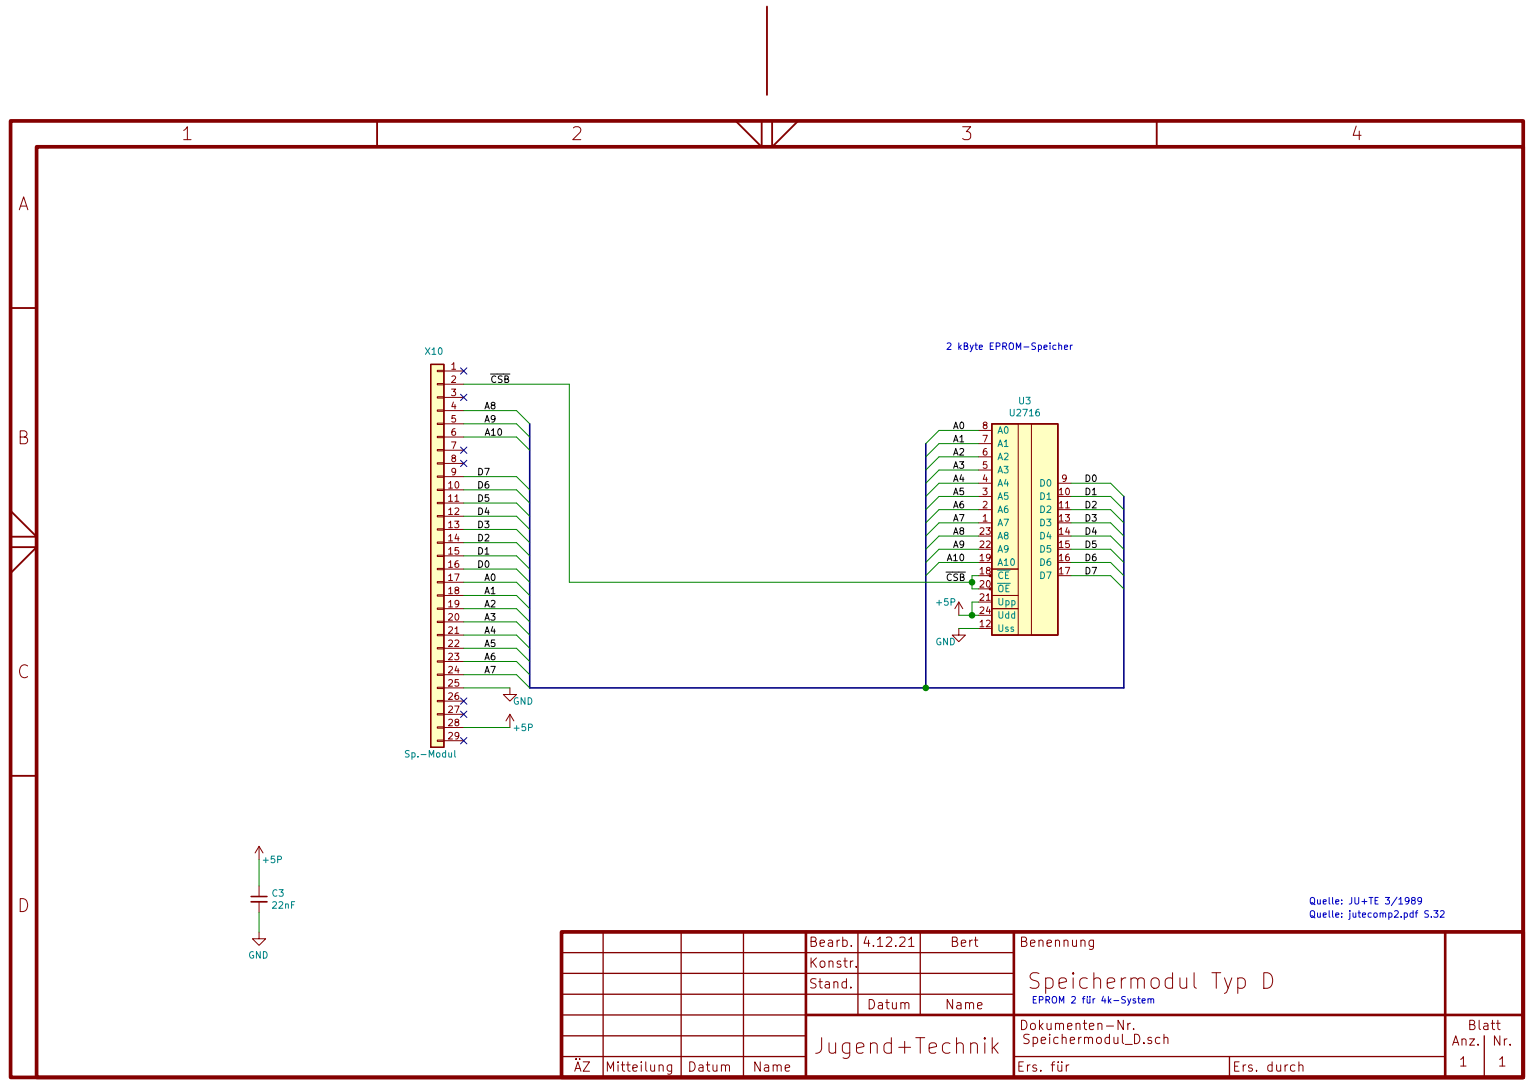
[picture p62: page 1]

Datum | Name

Dokumenten-Nr. | | Blatt
