boert/JU-TE-Computer/Erweiterungen/Schaltplan__Speichermodul_VRAM.pdf

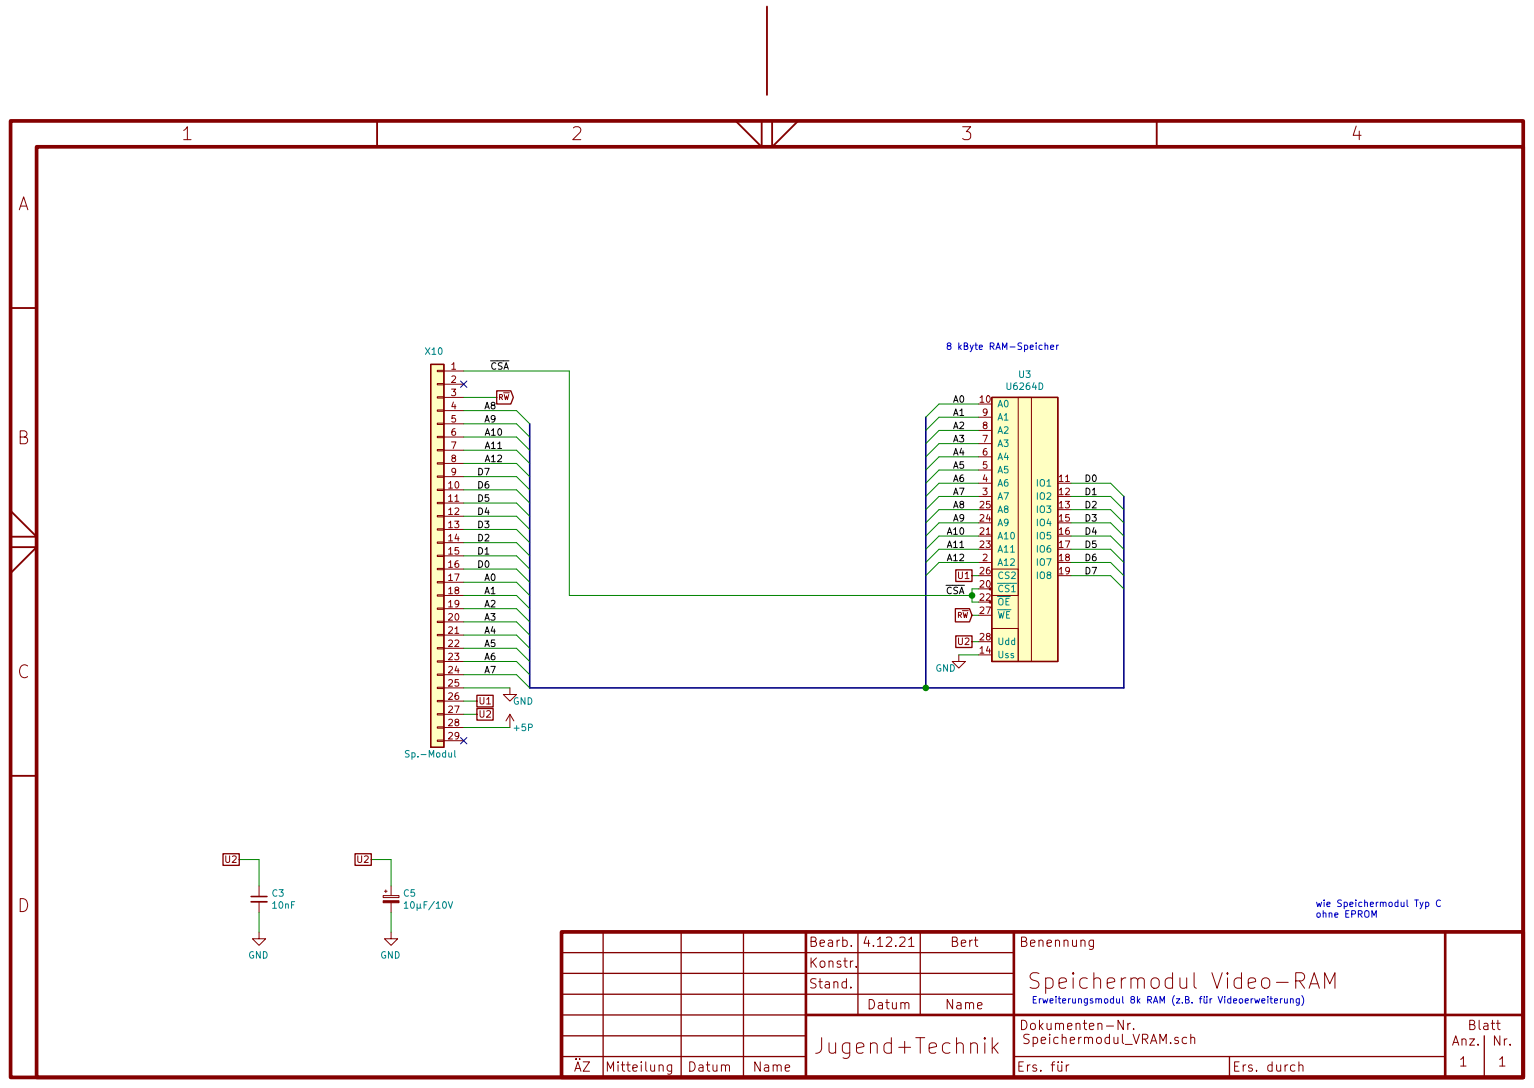
[picture p63: page 1]

Datum | Name

Erweiterungsmodul 8k RAM (z.B. für Videoerweiterung)

Dokumenten-Nr. | | Blatt
