boert/JU-TE-Computer/Erweiterungen/Schaltplan__Videoinverter.pdf

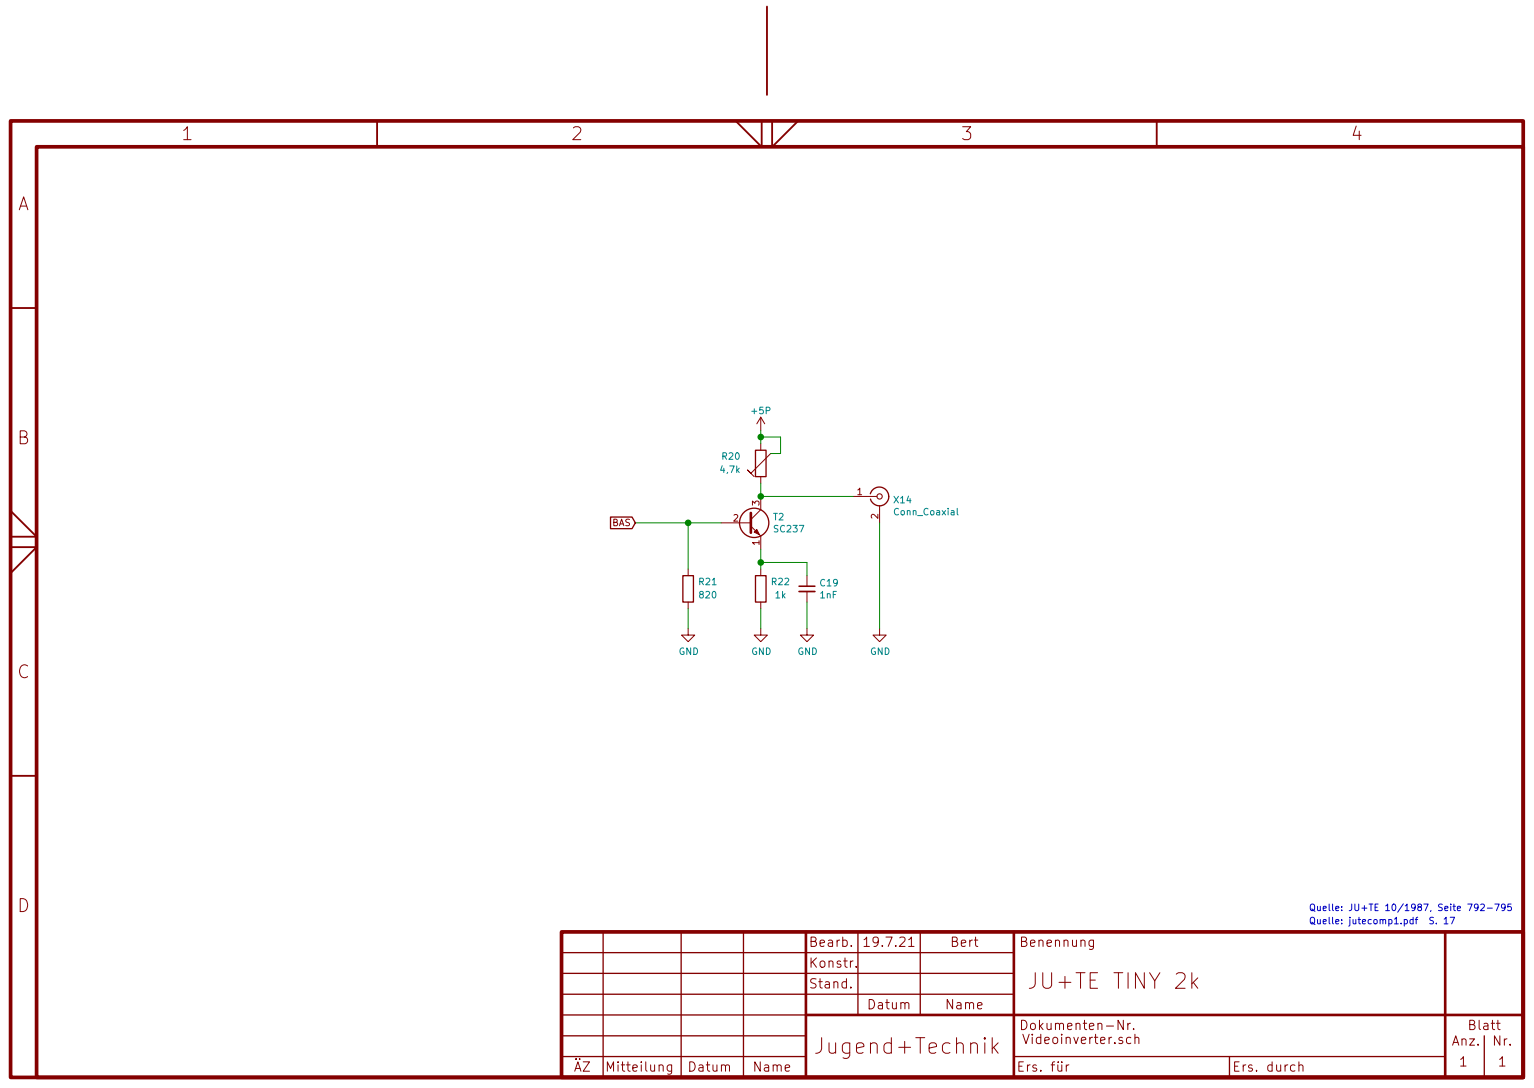
[picture p64: page 1]

Datum | Name

Dokumenten-Nr. | | Blatt
