boert/JU-TE-Computer/Erweiterungen/Videoerweiterung_2021/output_pdf/Platine__Videoerweiterung_2021.pdf

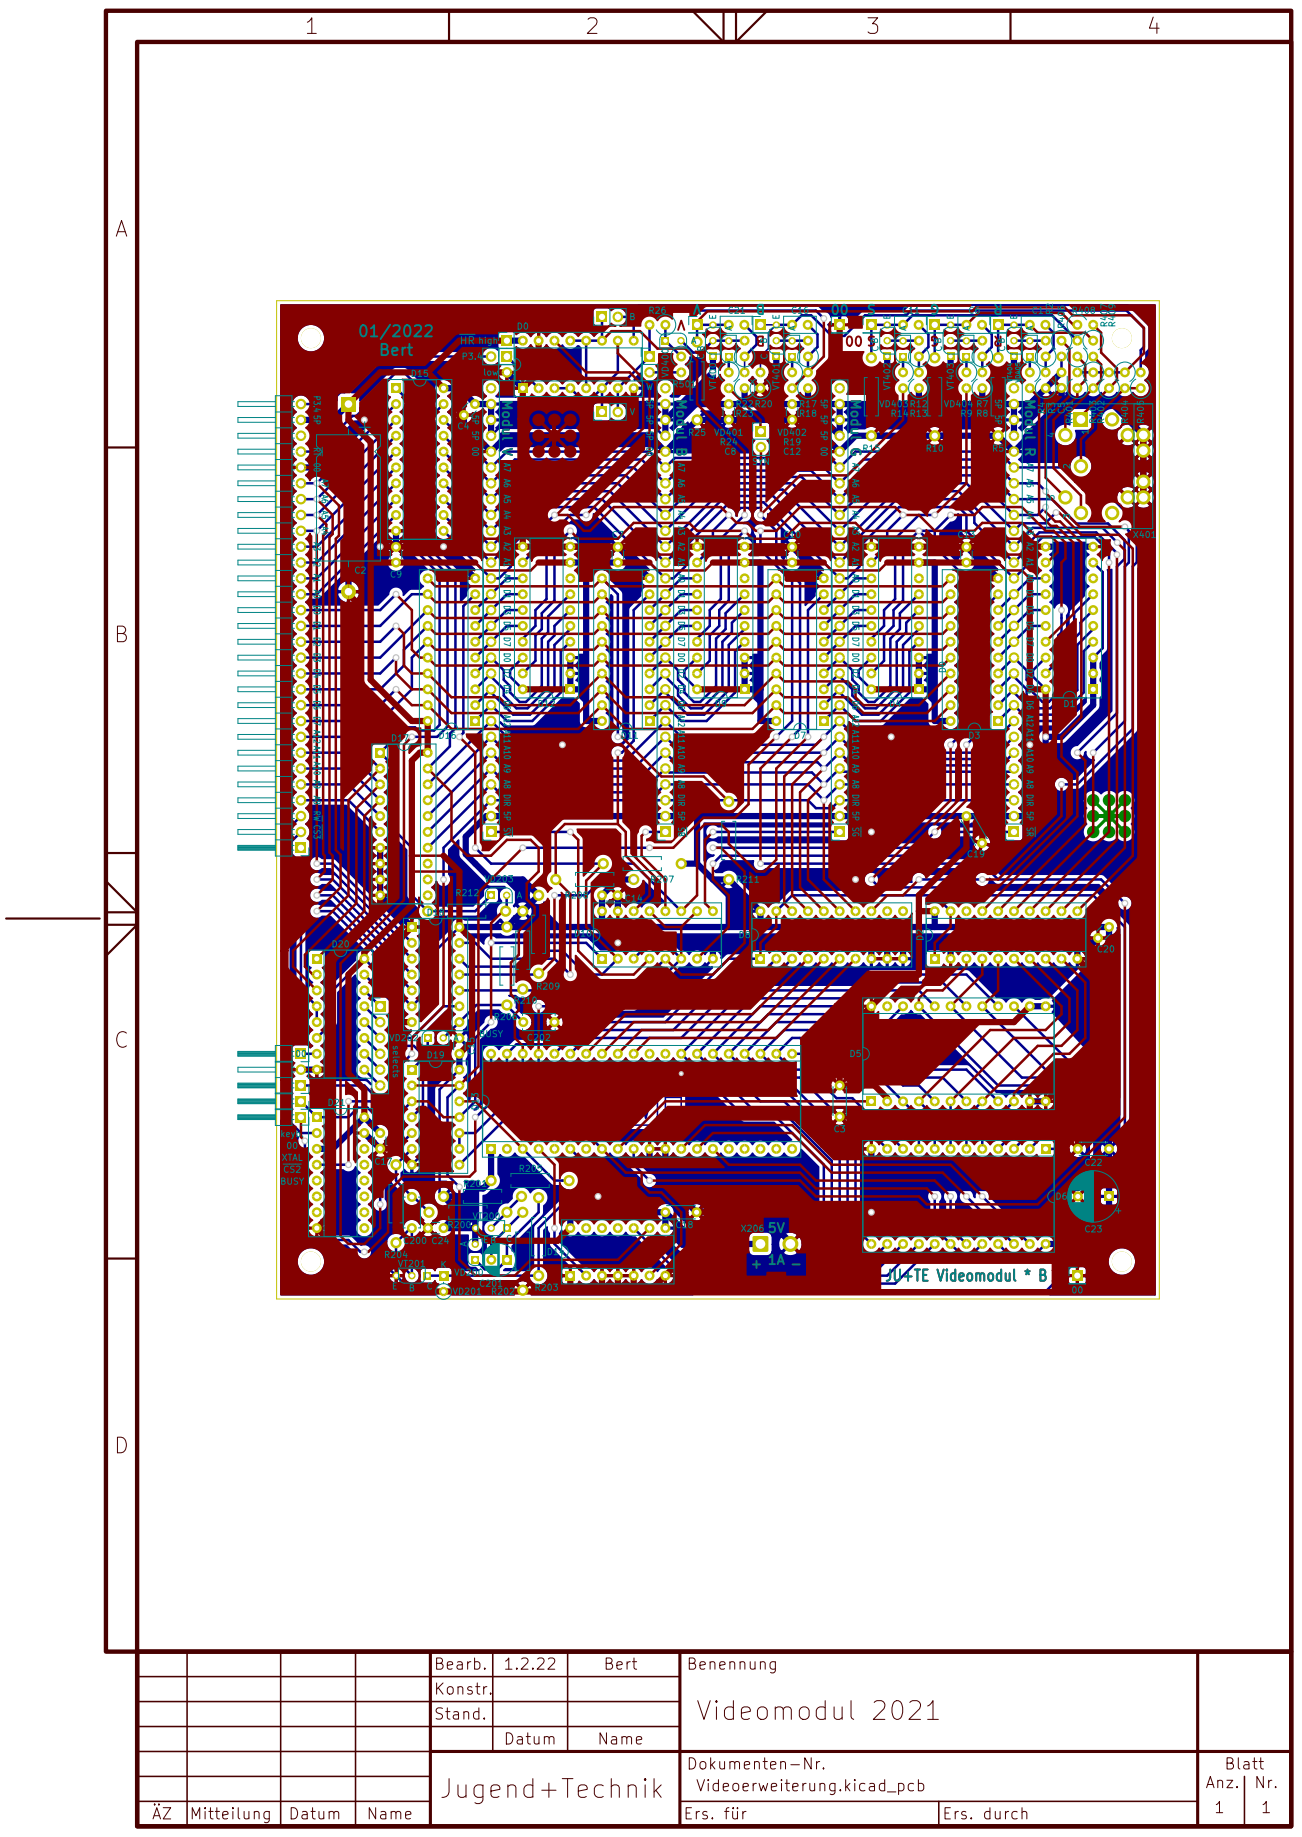
[picture p65: page 1]
