boert/JU-TE-Computer/Erweiterungen/Videoerweiterung_2021/output_pdf/Schaltplan__Videoerweiterung_2021.pdf

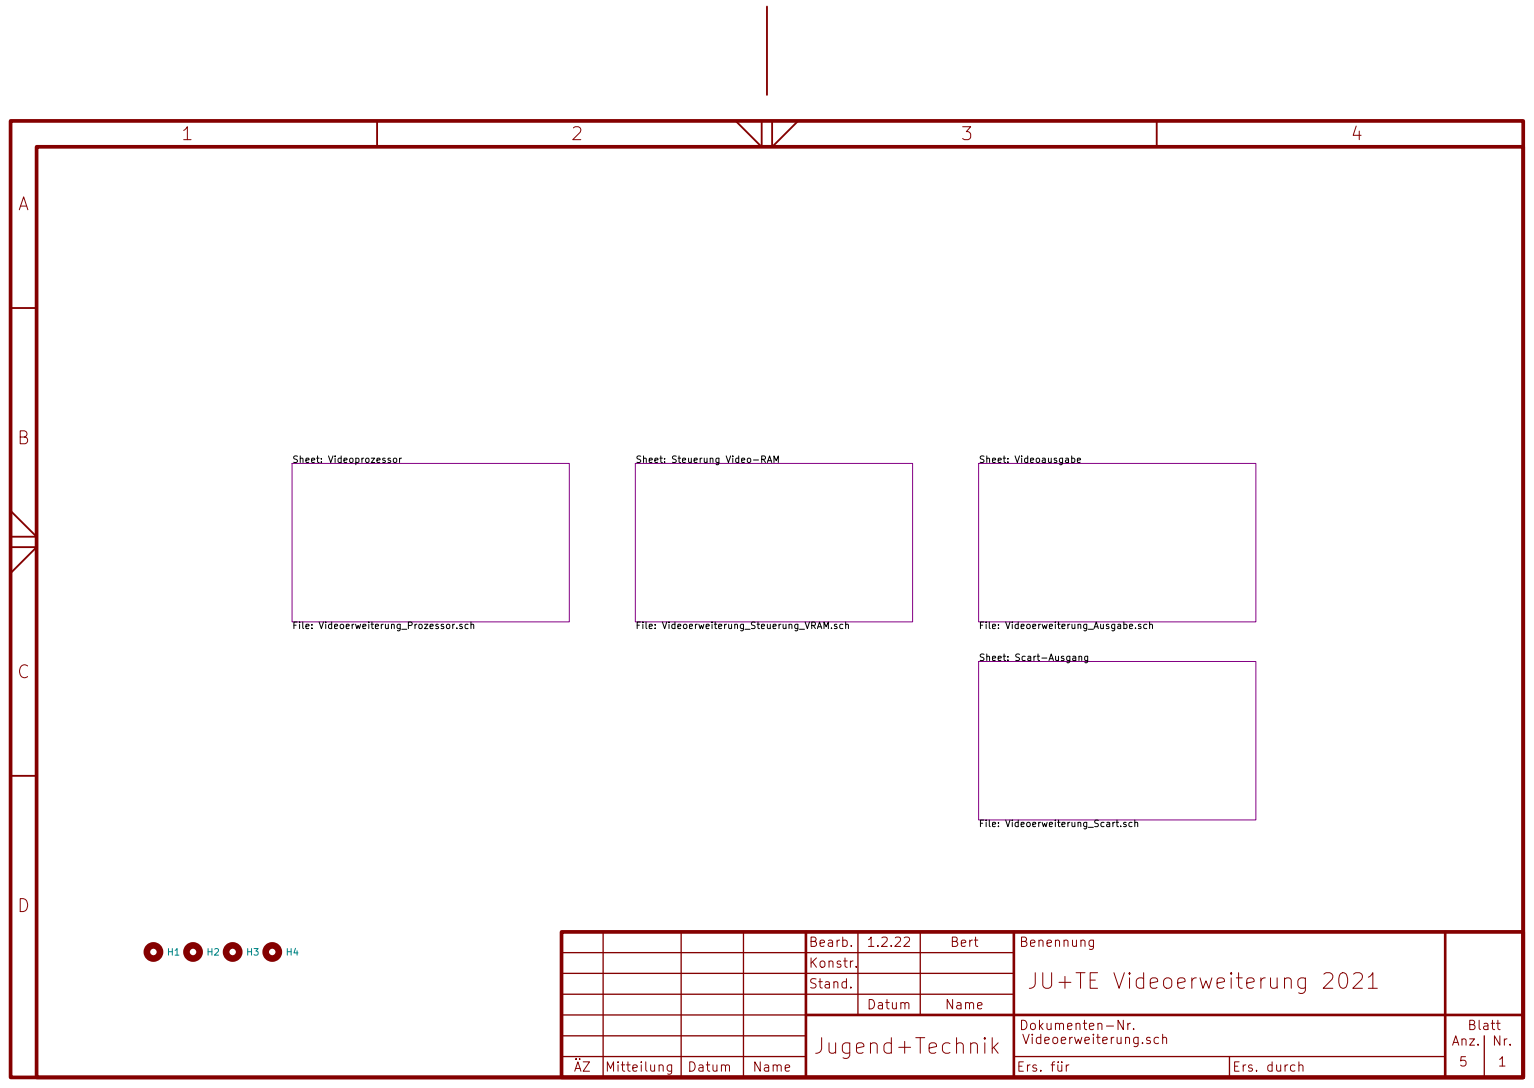
[picture p66: page 1]

Sheet: Steuerung Video-RAM

Datum | Name

Dokumenten-Nr. | | Blatt

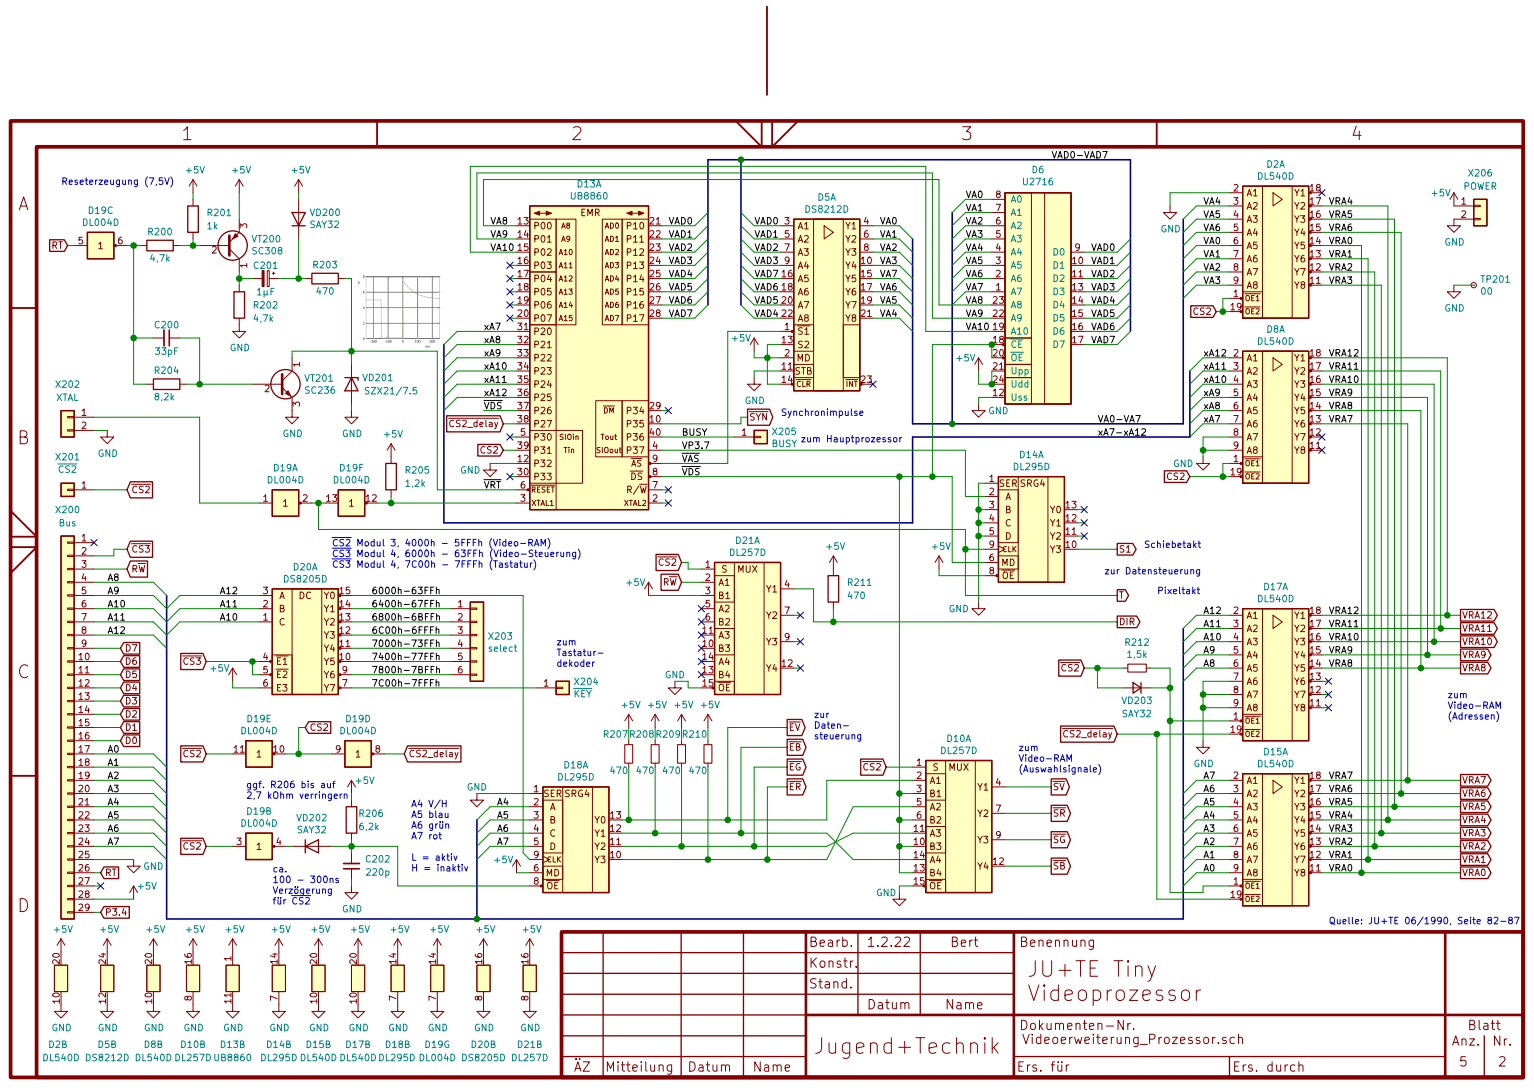
[picture p67: page 2]

A5 blau A6 grün A7 rot L = aktiv H = inaktiv

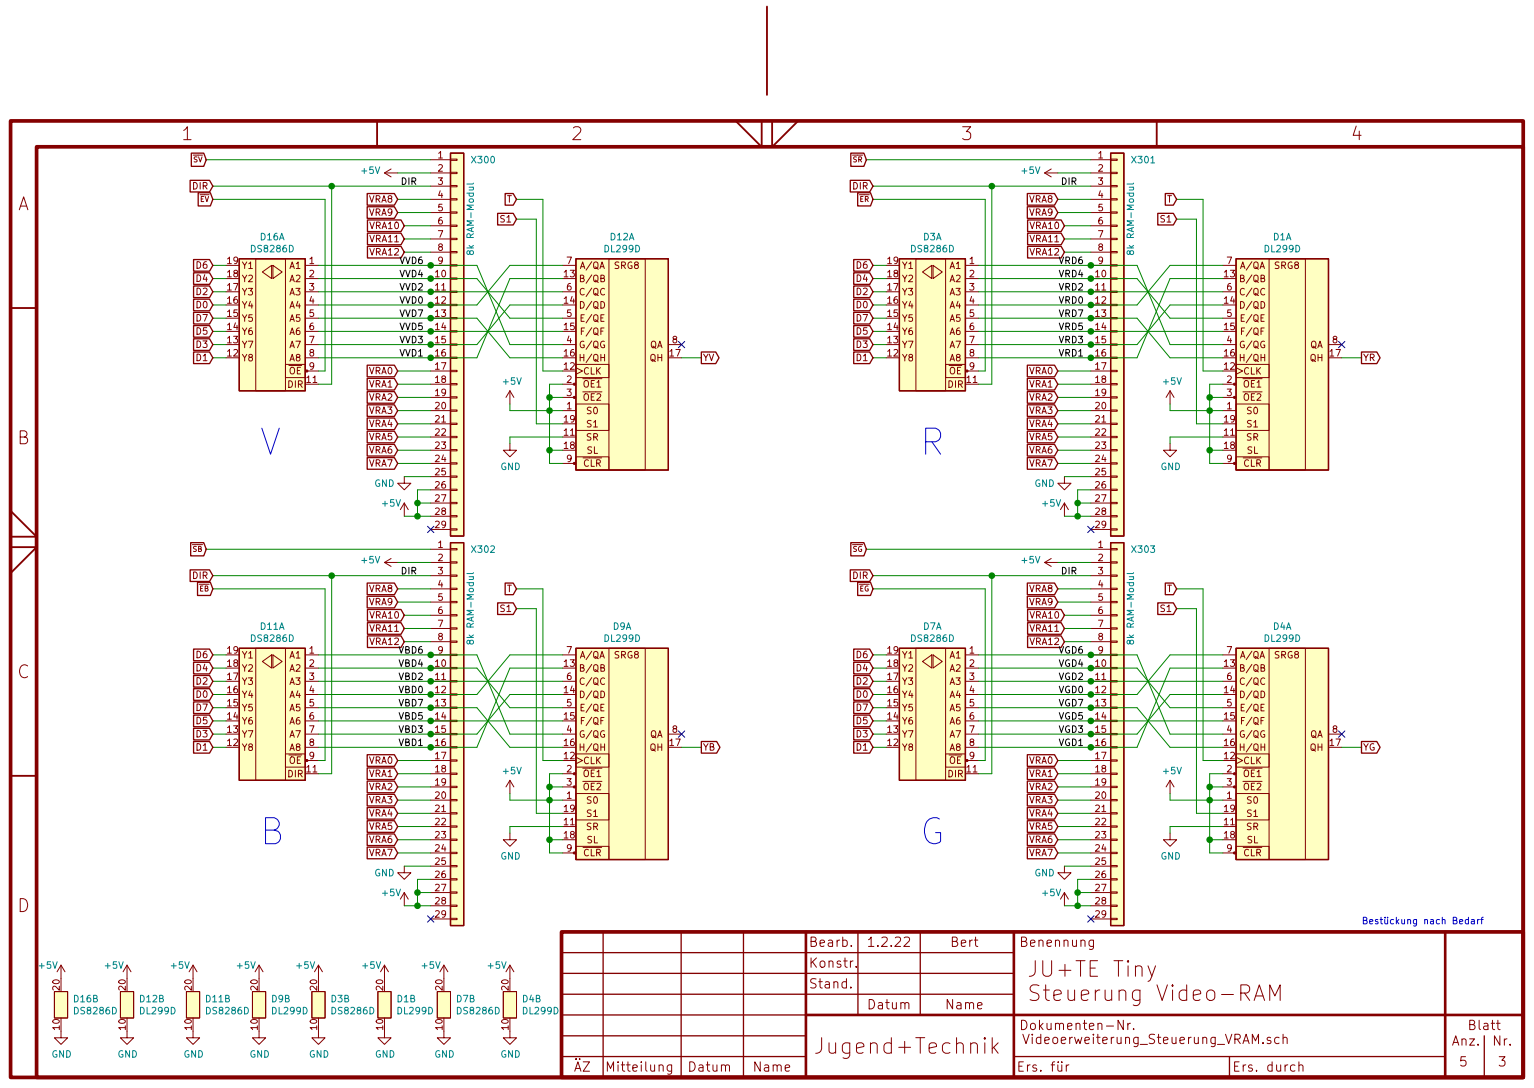
[picture p68: page 3]

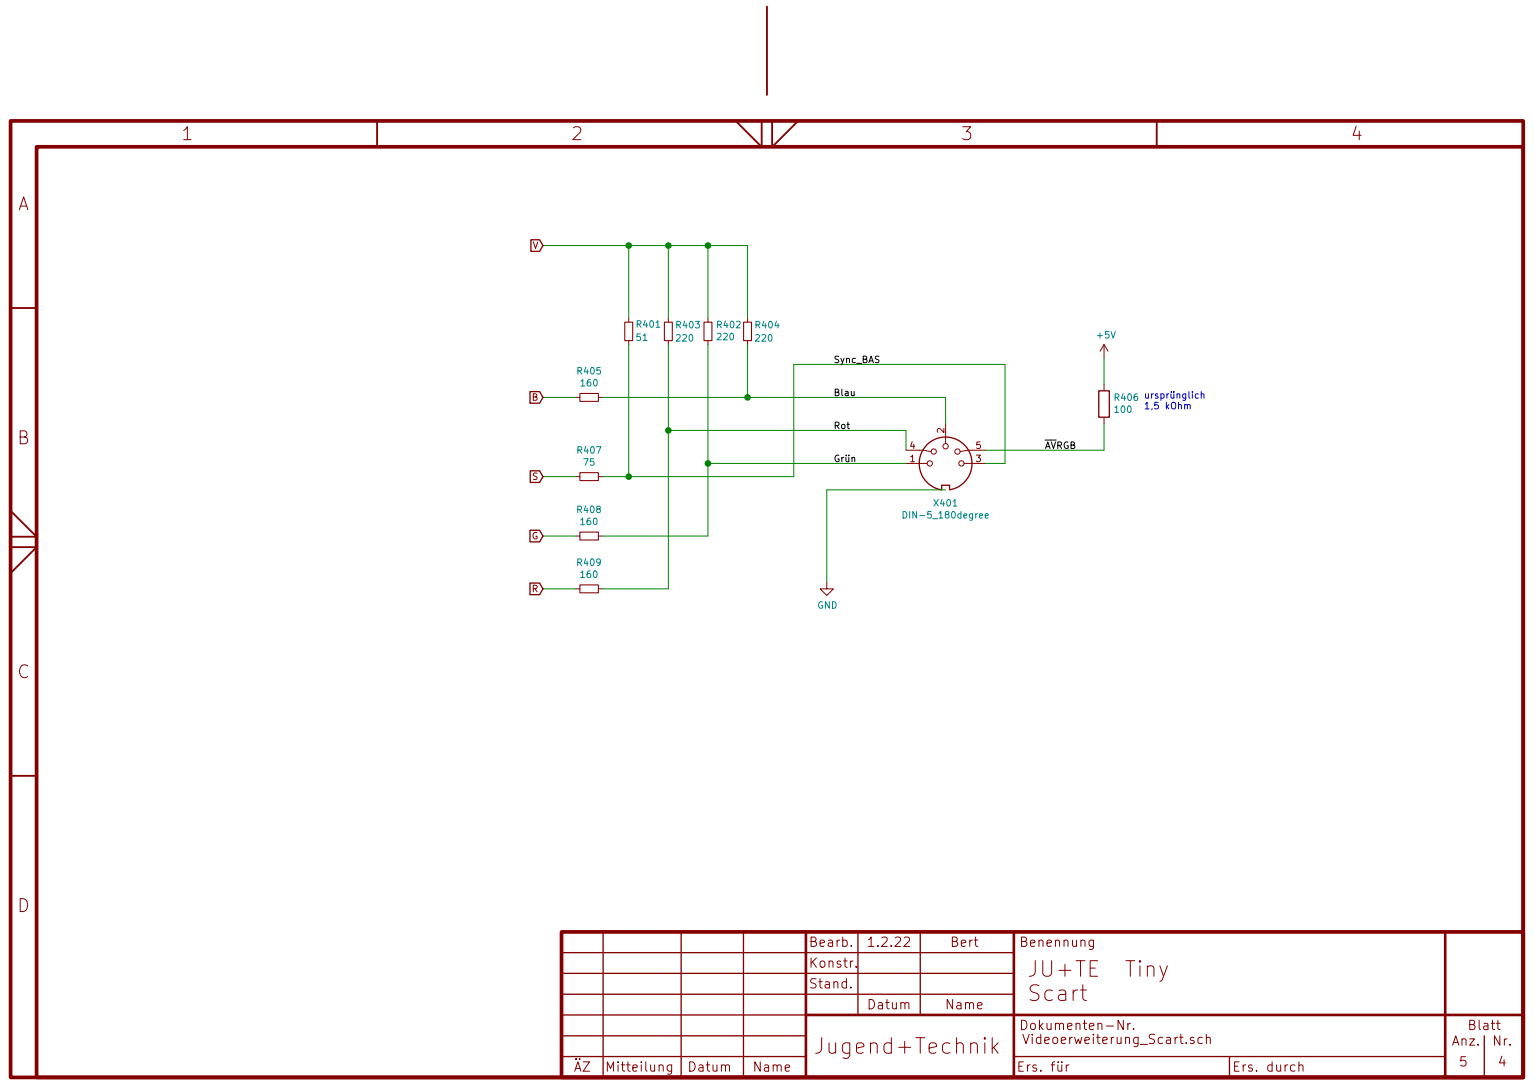
[picture p69: page 4]

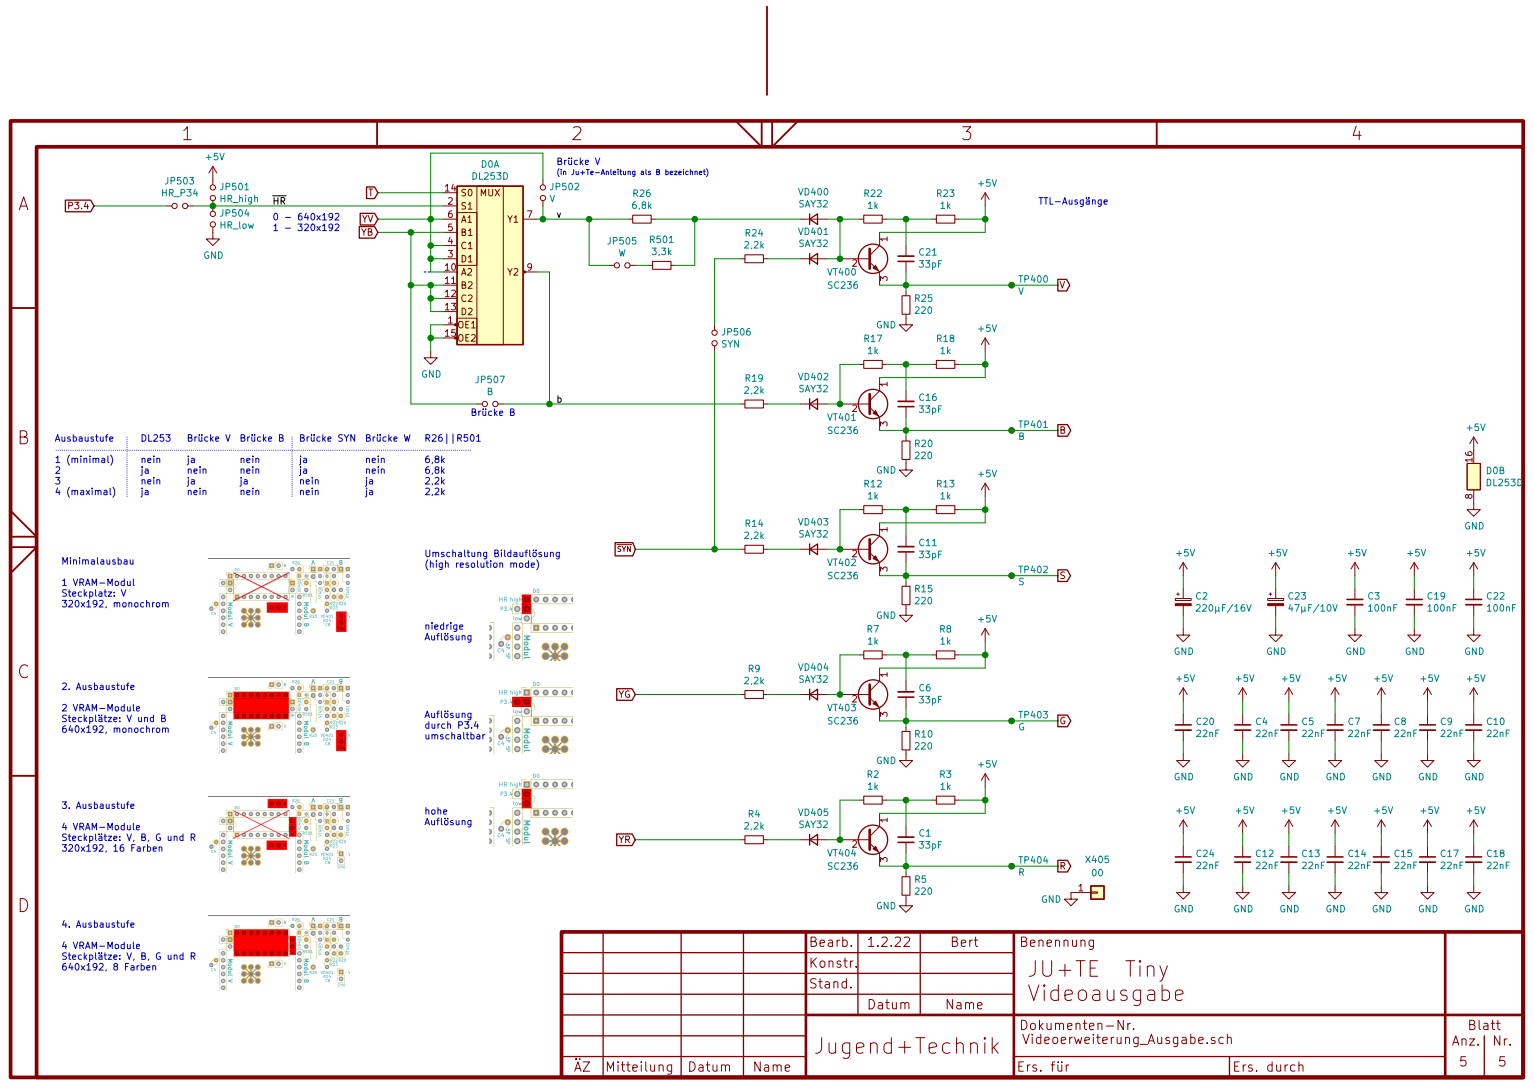
[picture p70: page 5]

(in Ju+Te-Anleitung als B bezeichnet) 0 - 640x192

TTL-Ausgänge Brücke SYN

5 | | R501

(high resolution mode) Ausbaustufe

2 VRAM-Module Steckplätze: V und B

4 VRAM-Module Steckplätze: V, B, G und R
