boert/JU-TE-Computer/Tiny_6k/kicad/Speichermodul_Typ_C.sch

## KiCad design Tiny_6k/kicad/Speichermodul_Typ_C.sch (2021-11-27)

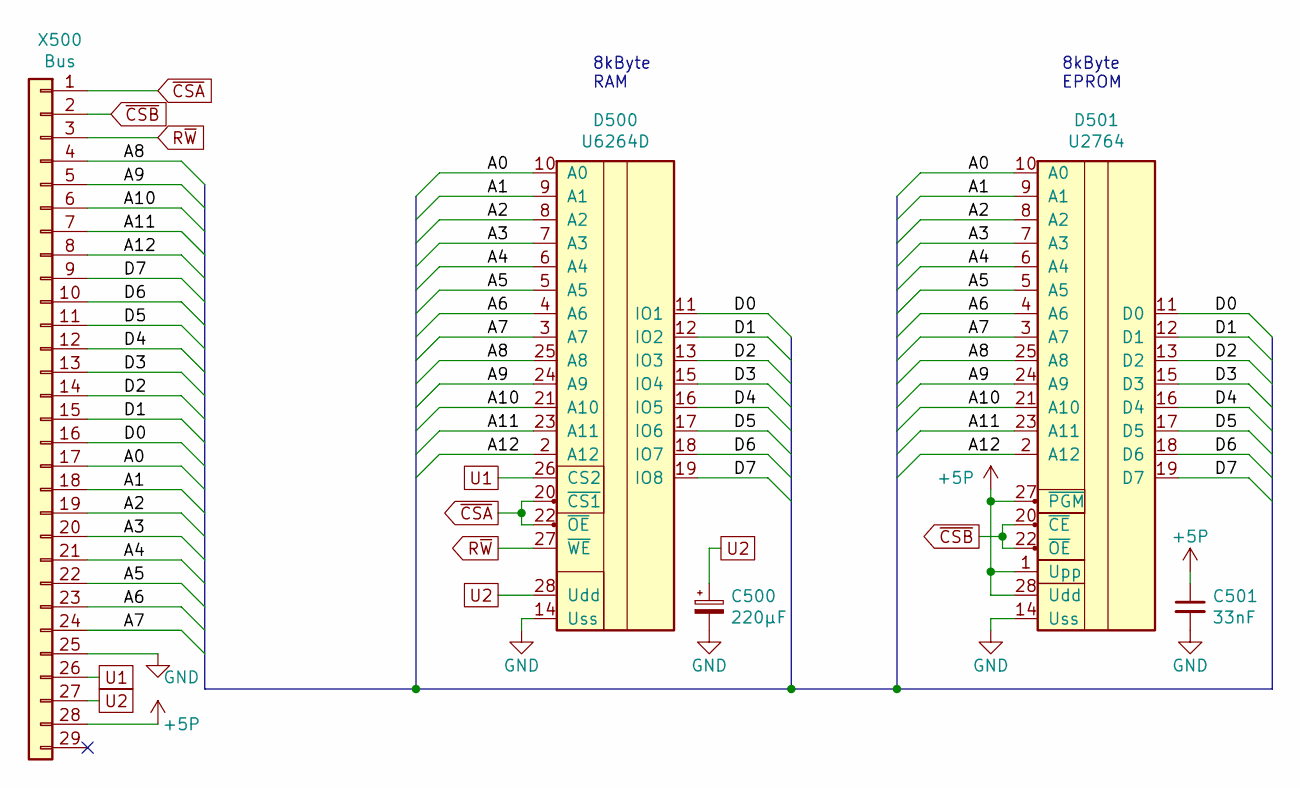
[picture p91: schematic Speichermodul_Typ_C.sch]

Parts:
C500: 220µF; CP_Axial_L18.0mm_D10.0mm_P25.00mm_Horizontal
C501: 33nF; C_Disc_D4.7mm_W2.5mm_P5.00mm
D500: U6264D; DIP-28_W15.24mm_Socket_LongPads
D501: U2764; DIP-28_W15.24mm_Socket_LongPads
X500: Bus; PinHeader_1x29_P2.54mm_Horizontal

Connections:
+5P: C501.1, D501.1 (Upp), D501.27 (~PGM), D501.28 (Udd), X500.28
A0: D500.10 (A0), D501.10 (A0), X500.17
A1: D500.9 (A1), D501.9 (A1), X500.18
A2: D500.8 (A2), D501.8 (A2), X500.19
A3: D500.7 (A3), D501.7 (A3), X500.20
A4: D500.6 (A4), D501.6 (A4), X500.21
A5: D500.5 (A5), D501.5 (A5), X500.22
A6: D500.4 (A6), D501.4 (A6), X500.23
A7: D500.3 (A7), D501.3 (A7), X500.24
A8: D500.25 (A8), D501.25 (A8), X500.4
A9: D500.24 (A9), D501.24 (A9), X500.5
A10: D500.21 (A10), D501.21 (A10), X500.6
A11: D500.23 (A11), D501.23 (A11), X500.7
A12: D500.2 (A12), D501.2 (A12), X500.8
D0: D500.11 (IO1), D501.11 (D0), X500.16
D1: D500.12 (IO2), D501.12 (D1), X500.15
D2: D500.13 (IO3), D501.13 (D2), X500.14
D3: D500.15 (IO4), D501.15 (D3), X500.13
D4: D500.16 (IO5), D501.16 (D4), X500.12
D5: D500.17 (IO6), D501.17 (D5), X500.11
D6: D500.18 (IO7), D501.18 (D6), X500.10
D7: D500.19 (IO8), D501.19 (D7), X500.9
GND: C500.2, C501.2, D500.14 (Uss), D501.14 (Uss), X500.25
R~W: D500.27 (~WE), X500.3
U1: D500.26 (CS2), X500.26
U2: C500.1, D500.28 (Udd), X500.27
~CSA: D500.20 (~CS1), D500.22 (~OE), X500.1
~CSB: D501.20 (~CE), D501.22 (~OE), X500.2

Notes on the sheet:
8kByte RAM
8kByte EPROM
