boert/JU-TE-Computer/Tiny_6k/kicad/Tiny6k_Hauptprozessor.sch

## KiCad design Tiny_6k/kicad/Tiny6k_Hauptprozessor.sch (2024-01-21)

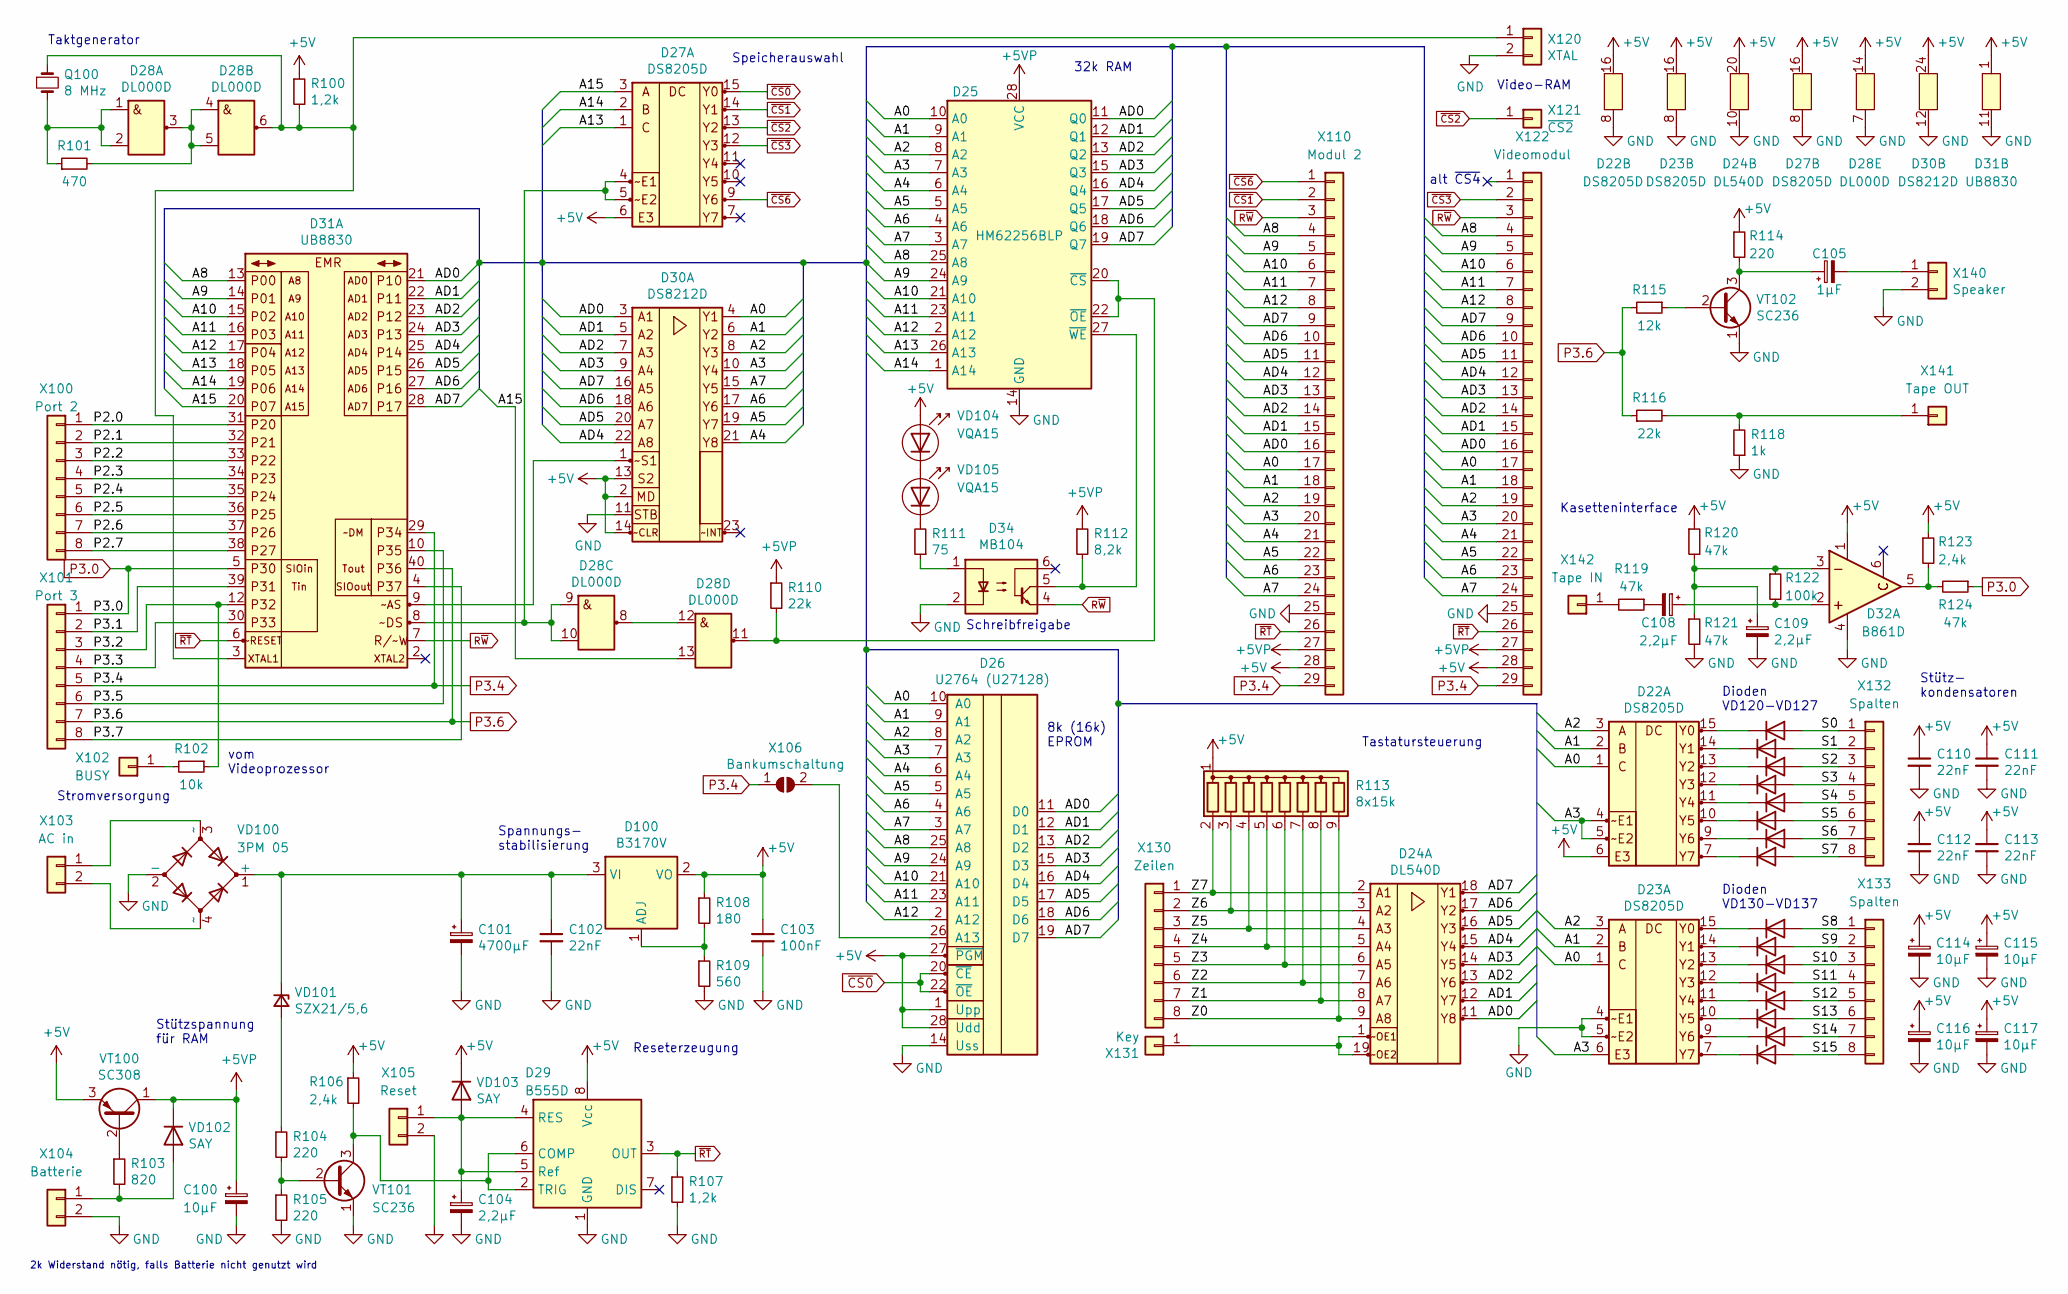
[picture p92: schematic Tiny6k_Hauptprozessor.sch]

Parts:
C100, C114, C115, C116, C117: 10µF; CP_Radial_D10.0mm_P2.50mm_P5.00mm
C101: 4700µF; CP_Axial_L38.0mm_D18.0mm_P44.00mm_Horizontal
C102, C110, C111, C112, C113: 22nF; C_Disc_D4.7mm_W2.5mm_P5.00mm
C103: 100nF; C_Disc_D4.7mm_W2.5mm_P5.00mm
C104, C108, C109: 2,2µF; CP_Radial_D10.0mm_P2.50mm_P5.00mm
C105: 1µF; CP_Radial_D10.0mm_P2.50mm_P5.00mm
D22, D23, D27: DS8205D; DIP-16_W7.62mm_Socket_LongPads
D24: DL540D; DIP-20_W7.62mm_Socket_LongPads
D25: HM62256BLP; DIP-28_W15.24mm_Socket_LongPads
D26: U2764 (U27128); DIP-28_W15.24mm_Socket_LongPads
D28: DL000D; DIP-14_W7.62mm_Socket_LongPads
D29: B555D; DIP-8_W7.62mm_Socket_LongPads
D30: DS8212D; DIP-24_W15.24mm_Socket_LongPads
D31: UB8830; DIP-40_W15.24mm_Socket_LongPads
D32: B861D; DIP-6_W7.62mm_Socket_LongPads
D34: MB104; DIP-6_W7.62mm
D100: B3170V; TO-220-3_Horizontal_TabDown
Q100: 8 MHz; Crystal_HC18-U_Vertical
R100, R107: 1,2k; R_Axial_DIN0207_L6.3mm_D2.5mm_P10.16mm_Horizontal
R101: 470; R_Axial_DIN0207_L6.3mm_D2.5mm_P10.16mm_Horizontal
R102: 10k; R_Axial_DIN0207_L6.3mm_D2.5mm_P10.16mm_Horizontal
R103: 820; R_Axial_DIN0207_L6.3mm_D2.5mm_P10.16mm_Horizontal
R104, R105, R114: 220; R_Axial_DIN0207_L6.3mm_D2.5mm_P10.16mm_Horizontal
R106, R123: 2,4k; R_Axial_DIN0207_L6.3mm_D2.5mm_P10.16mm_Horizontal
R108: 180; R_Axial_DIN0207_L6.3mm_D2.5mm_P10.16mm_Horizontal
R109: 560; R_Axial_DIN0207_L6.3mm_D2.5mm_P10.16mm_Horizontal
R110, R116: 22k; R_Axial_DIN0207_L6.3mm_D2.5mm_P10.16mm_Horizontal
R111: 75; R_Axial_DIN0207_L6.3mm_D2.5mm_P10.16mm_Horizontal
R112: 8,2k; R_Axial_DIN0207_L6.3mm_D2.5mm_P10.16mm_Horizontal
R113: 8x15k; R_Array_SIP9
R115: 12k; R_Axial_DIN0207_L6.3mm_D2.5mm_P10.16mm_Horizontal
R118: 1k; R_Axial_DIN0207_L6.3mm_D2.5mm_P10.16mm_Horizontal
R119, R120, R121, R124: 47k; R_Axial_DIN0207_L6.3mm_D2.5mm_P10.16mm_Horizontal
R122: 100k; R_Axial_DIN0207_L6.3mm_D2.5mm_P10.16mm_Horizontal
VD100: 3PM 05; Diode_Bridge_32.0x5.6x17.0mm_P10.0mm_P7.5mm
VD101: SZX21/5,6; D_DO-34_SOD68_P2.54mm_Vertical_AnodeUp
VD102, VD103, VD120, VD121, VD122, VD123, VD124, VD125, VD126, VD127, VD130, VD131, VD132, VD133, VD134, VD135, VD136, VD137: SAY; D_DO-34_SOD68_P2.54mm_Vertical_AnodeUp
VD104, VD105: VQA15; LED_D3.0mm_Clear
VT100: SC308; TO-92Flat
VT101, VT102: SC236; TO-92Flat
X100: Port 2; TerminalBlock_RND_205-00293_1x08_P5.08mm_Horizontal
X101: Port 3; TerminalBlock_RND_205-00293_1x08_P5.08mm_Horizontal
X102: BUSY; PinHeader_1x01_P2.54mm_Vertical
X103: AC in; TerminalBlock_RND_205-00287_1x02_P5.08mm_Horizontal
X104: Batterie; TerminalBlock_RND_205-00287_1x02_P5.08mm_Horizontal
X105: Reset; TerminalBlock_RND_205-00287_1x02_P5.08mm_Horizontal
X106: Bankumschaltung; SolderJumper-2_P1.3mm_Open_RoundedPad1.0x1.5mm
X110: Modul 2; PinSocket_1x29_P2.54mm_Vertical
X120: XTAL; PinHeader_1x02_P2.54mm_Vertical
X121: ~CS2; PinHeader_1x01_P2.54mm_Vertical
X122: Videomodul; PinSocket_1x29_P2.54mm_Vertical
X130: Zeilen; PinHeader_1x08_P2.54mm_Vertical
X131: Key; PinHeader_1x01_P2.54mm_Vertical
X132, X133: Spalten; PinHeader_1x08_P2.54mm_Vertical
X140: Speaker; TerminalBlock_RND_205-00287_1x02_P5.08mm_Horizontal
X141: Tape OUT; PinHeader_1x01_P2.54mm_Vertical
X142: Tape IN; PinHeader_1x01_P2.54mm_Vertical

Connections:
+5V: C103.1, C110.1, C111.1, C112.1, C113.1, C114.1, C115.1, C116.1, C117.1, D22.6 (E3), D22.16 (Vcc), D23.16 (Vcc), D24.20 (Vcc), D26.1 (Upp), D26.27 (~PGM), D26.28 (Udd), D27.6 (E3), D27.16 (Vcc), D28.14 (Vcc), D29.8 (Vcc), D30.2 (MD), D30.13 (S2), D30.14 (~CLR), D30.24 (Vcc), D31.1 (Vcc), D32.1 (+), D100.2 (VO), R100.1, R106.1, R108.1, R113.1 (common), R114.1, R120.1, R123.1, VD103.1 (K), VD104.2 (A), VT100.3 (E), X110.28, X122.28
+5VP: C100.1, D25.28 (VCC), R110.1, R112.1, VD102.1 (K), VT100.1 (C), X110.27, X122.27
A0: D22.1 (C), D23.1 (C), D25.10 (A0), D26.10 (A0), D30.4 (Y1), X110.17, X122.17
A1: D22.2 (B), D23.2 (B), D25.9 (A1), D26.9 (A1), D30.6 (Y2), X110.18, X122.18
A2: D22.3 (A), D23.3 (A), D25.8 (A2), D26.8 (A2), D30.8 (Y3), X110.19, X122.19
A3: D22.4 (~E1), D22.5 (~E2), D23.6 (E3), D25.7 (A3), D26.7 (A3), D30.10 (A4), X110.20, X122.20
A4: D25.6 (A4), D26.6 (A4), D30.21 (Y8), X110.21, X122.21
A5: D25.5 (A5), D26.5 (A5), D30.19 (Y7), X110.22, X122.22
A6: D25.4 (A6), D26.4 (A6), D30.17 (Y6), X110.23, X122.23
A7: D25.3 (A7), D26.3 (A7), D30.15 (Y5), X110.24, X122.24
A8: D25.25 (A8), D26.25 (A8), D31.13 (P00), X110.4, X122.4
A9: D25.24 (A9), D26.24 (A9), D31.14 (P01), X110.5, X122.5
A10: D25.21 (A10), D26.21 (A10), D31.15 (P02), X110.6, X122.6
A11: D25.23 (A11), D26.23 (A11), D31.16 (P03), X110.7, X122.7
A12: D25.2 (A12), D26.2 (A12), D31.17 (P04), X110.8, X122.8
A13: D25.26 (A13), D27.1 (C), D31.18 (P05)
A14: D25.1 (A14), D27.2 (B), D31.19 (P06)
A15: D27.3 (A), D28.13 (B4), D31.20 (P07)
AD0: D24.11 (Y8), D25.11 (Q0), D26.11 (D0), D30.3 (A1), D31.21 (P10), X110.16, X122.16
AD1: D24.12 (Y7), D25.12 (Q1), D26.12 (D1), D30.5 (A2), D31.22 (P11), X110.15, X122.15
AD2: D24.13 (Y6), D25.13 (Q2), D26.13 (D2), D30.7 (A3), D31.23 (P12), X110.14, X122.14
AD3: D24.14 (Y5), D25.15 (Q3), D26.15 (D3), D30.9 (A4), D31.24 (P13), X110.13, X122.13
AD4: D24.15 (A4), D25.16 (Q4), D26.16 (D4), D30.22 (A8), D31.25 (P14), X110.12, X122.12
AD5: D24.16 (Y3), D25.17 (Q5), D26.17 (D5), D30.20 (A7), D31.26 (P15), X110.11, X122.11
AD6: D24.17 (Y2), D25.18 (Q6), D26.18 (D6), D30.18 (A6), D31.27 (P16), X110.10, X122.10
AD7: D24.18 (Y1), D25.19 (Q7), D26.19 (D7), D30.16 (A5), D31.28 (P17), X110.9, X122.9
GND: C100.2, C101.2, C102.2, C103.2, C104.2, C109.2, C110.2, C111.2, C112.2, C113.2, C114.2, C115.2, C116.2, C117.2, D22.8 (GND), D23.4 (~E1), D23.5 (~E2), D23.8 (GND), D24.10 (GND), D25.14 (GND), D26.14 (Uss), D27.8 (GND), D28.7 (GND), D29.1 (GND), D30.11 (STB), D30.12 (GND), D31.11 (GND), D32.4 (-), D34.2, R105.2, R107.2, R109.2, R118.1, R121.2, VD100.2 (-), VT101.1 (E), VT102.1 (E), X104.2, X105.2, X110.25, X120.2, X122.25, X140.2
unnamed: C101.1, C102.1, D100.3 (VI), VD100.1 (+), VD101.1 (K)
unnamed: C104.1, D29.4 (RES), D29.5 (Ref), VD103.2 (A), X105.1
unnamed: C105.1, R114.2, VT102.3 (C)
unnamed: C105.2, X140.1
unnamed: C108.1, D32.2 (+), R122.2
unnamed: C108.2, R119.1
unnamed: C109.1, D32.3 (-), R120.2, R121.1, R122.1
unnamed: D22.7 (Y7), VD127.1 (K)
unnamed: D22.9 (Y6), VD126.1 (K)
unnamed: D22.10 (Y5), VD125.1 (K)
unnamed: D22.11 (Y4), VD124.1 (K)
unnamed: D22.12 (Y3), VD123.1 (K)
unnamed: D22.13 (Y2), VD122.1 (K)
unnamed: D22.14 (Y1), VD121.1 (K)
unnamed: D22.15 (Y0), VD120.1 (K)
unnamed: D23.7 (Y7), VD137.1 (K)
unnamed: D23.9 (Y6), VD136.1 (K)
unnamed: D23.10 (Y5), VD135.1 (K)
unnamed: D23.11 (Y4), VD134.1 (K)
unnamed: D23.12 (Y3), VD133.1 (K)
unnamed: D23.13 (Y2), VD132.1 (K)
unnamed: D23.14 (Y1), VD131.1 (K)
unnamed: D23.15 (Y0), VD130.1 (K)
unnamed: D24.1 (OE1), D24.19 (~OE2), X131.1
unnamed: D25.20 (~CS), D25.22 (~OE), D28.11 (Y4), R110.2
unnamed: D25.27 (~WE), D34.5, R112.2
unnamed: D26.26 (A13), X106.2 (B)
unnamed: D27.4 (~E1), D27.5 (~E2), D28.9 (A3), D28.10 (B3), D31.8 (~DS)
unnamed: D28.1 (A1), D28.2 (B1), Q100.2, R101.1
unnamed: D28.3 (Y1), D28.4 (A2), D28.5 (B2), R101.2
unnamed: D28.6 (Y2), D31.3 (XTAL1), Q100.1, R100.2, X120.1
unnamed: D28.8 (Y3), D28.12 (A4)
unnamed: D29.2 (TRIG), D29.6 (COMP), R106.2, VT101.3 (C)
unnamed: D30.1 (~S1), D31.9 (~AS)
unnamed: D32.5, R123.2, R124.2
unnamed: D34.1, R111.1
unnamed: D100.1 (ADJ), R108.2, R109.1
unnamed: R102.2, X102.1
unnamed: R103.1, VT100.2 (B)
unnamed: R103.2, VD102.2 (A), X104.1
unnamed: R104.1, VD101.2 (A)
unnamed: R104.2, R105.1, VT101.2 (B)
unnamed: R111.2, VD105.1 (K)
unnamed: R115.1, VT102.2 (B)
unnamed: R116.2, R118.2, X141.1
unnamed: R119.2, X142.1
unnamed: VD100.3 (~~), X103.1
unnamed: VD100.4 (~~), X103.2
unnamed: VD104.1 (K), VD105.2 (A)
P2.0: D31.31 (P20), X100.1
P2.1: D31.32 (P21), X100.2
P2.2: D31.33 (P22), X100.3
P2.3: D31.34 (P23), X100.4
P2.4: D31.35 (P24), X100.5
P2.5: D31.36 (P25), X100.6
P2.6: D31.37 (P26), X100.7
P2.7: D31.38 (P27), X100.8
P3.0: D31.5 (P30), R124.1, X101.1
P3.1: D31.39 (P31), X101.2
P3.2: D31.12 (P32), R102.1, X101.3
P3.3: D31.30 (P33), X101.4
P3.4: D31.29 (P34), X101.5, X106.1 (A), X110.29, X122.29
P3.5: D31.10 (P35), X101.6
P3.6: D31.40 (P36), R115.2, R116.1, X101.7
P3.7: D31.4 (P37), X101.8
R~W: D31.7 (R/~W), D34.4, X110.3, X122.3
S0: VD120.2 (A), X132.1
S1: VD121.2 (A), X132.2
S2: VD122.2 (A), X132.3
S3: VD123.2 (A), X132.4
S4: VD124.2 (A), X132.5
S5: VD125.2 (A), X132.6
S6: VD126.2 (A), X132.7
S7: VD127.2 (A), X132.8
S8: VD130.2 (A), X133.1
S9: VD131.2 (A), X133.2
S10: VD132.2 (A), X133.3
S11: VD133.2 (A), X133.4
S12: VD134.2 (A), X133.5
S13: VD135.2 (A), X133.6
S14: VD136.2 (A), X133.7
S15: VD137.2 (A), X133.8
Z0: D24.9 (A8), R113.9 (R8), X130.8
Z1: D24.8 (A7), R113.8 (R7), X130.7
Z2: D24.7 (A6), R113.7 (R6), X130.6
Z3: D24.6 (A5), R113.6 (R5), X130.5
Z4: D24.5 (A4), R113.5 (R4), X130.4
Z5: D24.4 (A3), R113.4 (R3), X130.3
Z6: D24.3 (A2), R113.3 (R2), X130.2
Z7: D24.2 (A1), R113.2 (R1), X130.1
~CS0: D26.20 (~CE), D26.22 (~OE), D27.15 (Y0)
~CS1: D27.14 (Y1), X110.2
~CS2: D27.13 (Y2), X121.1
~CS3: D27.12 (Y3), X122.2
~CS6: D27.9 (Y6), X110.1
~RT: D29.3 (OUT), D31.6 (~RESET), R107.1, X110.26, X122.26

Notes on the sheet:
Taktgenerator
Reseterzeugung
8k (16k) EPROM
32k RAM
Stützspannung für RAM
Spannungs- stabilisierung
Tastatursteuerung
vom Videoprozessor
Kasetteninterface
Speicherauswahl
Stromversorgung
2k Widerstand nötig, falls Batterie nicht genutzt wird
Stütz- kondensatoren
alt ~CS4~
Video-RAM
Schreibfreigabe
Dioden VD120-VD127
Dioden VD130-VD137
