boert/JU-TE-Computer/Tiny_6k/kicad/Tiny6k_Steuerung_Video-RAM.sch

## KiCad design Tiny_6k/kicad/Tiny6k_Steuerung_Video-RAM.sch (2021-12-13)

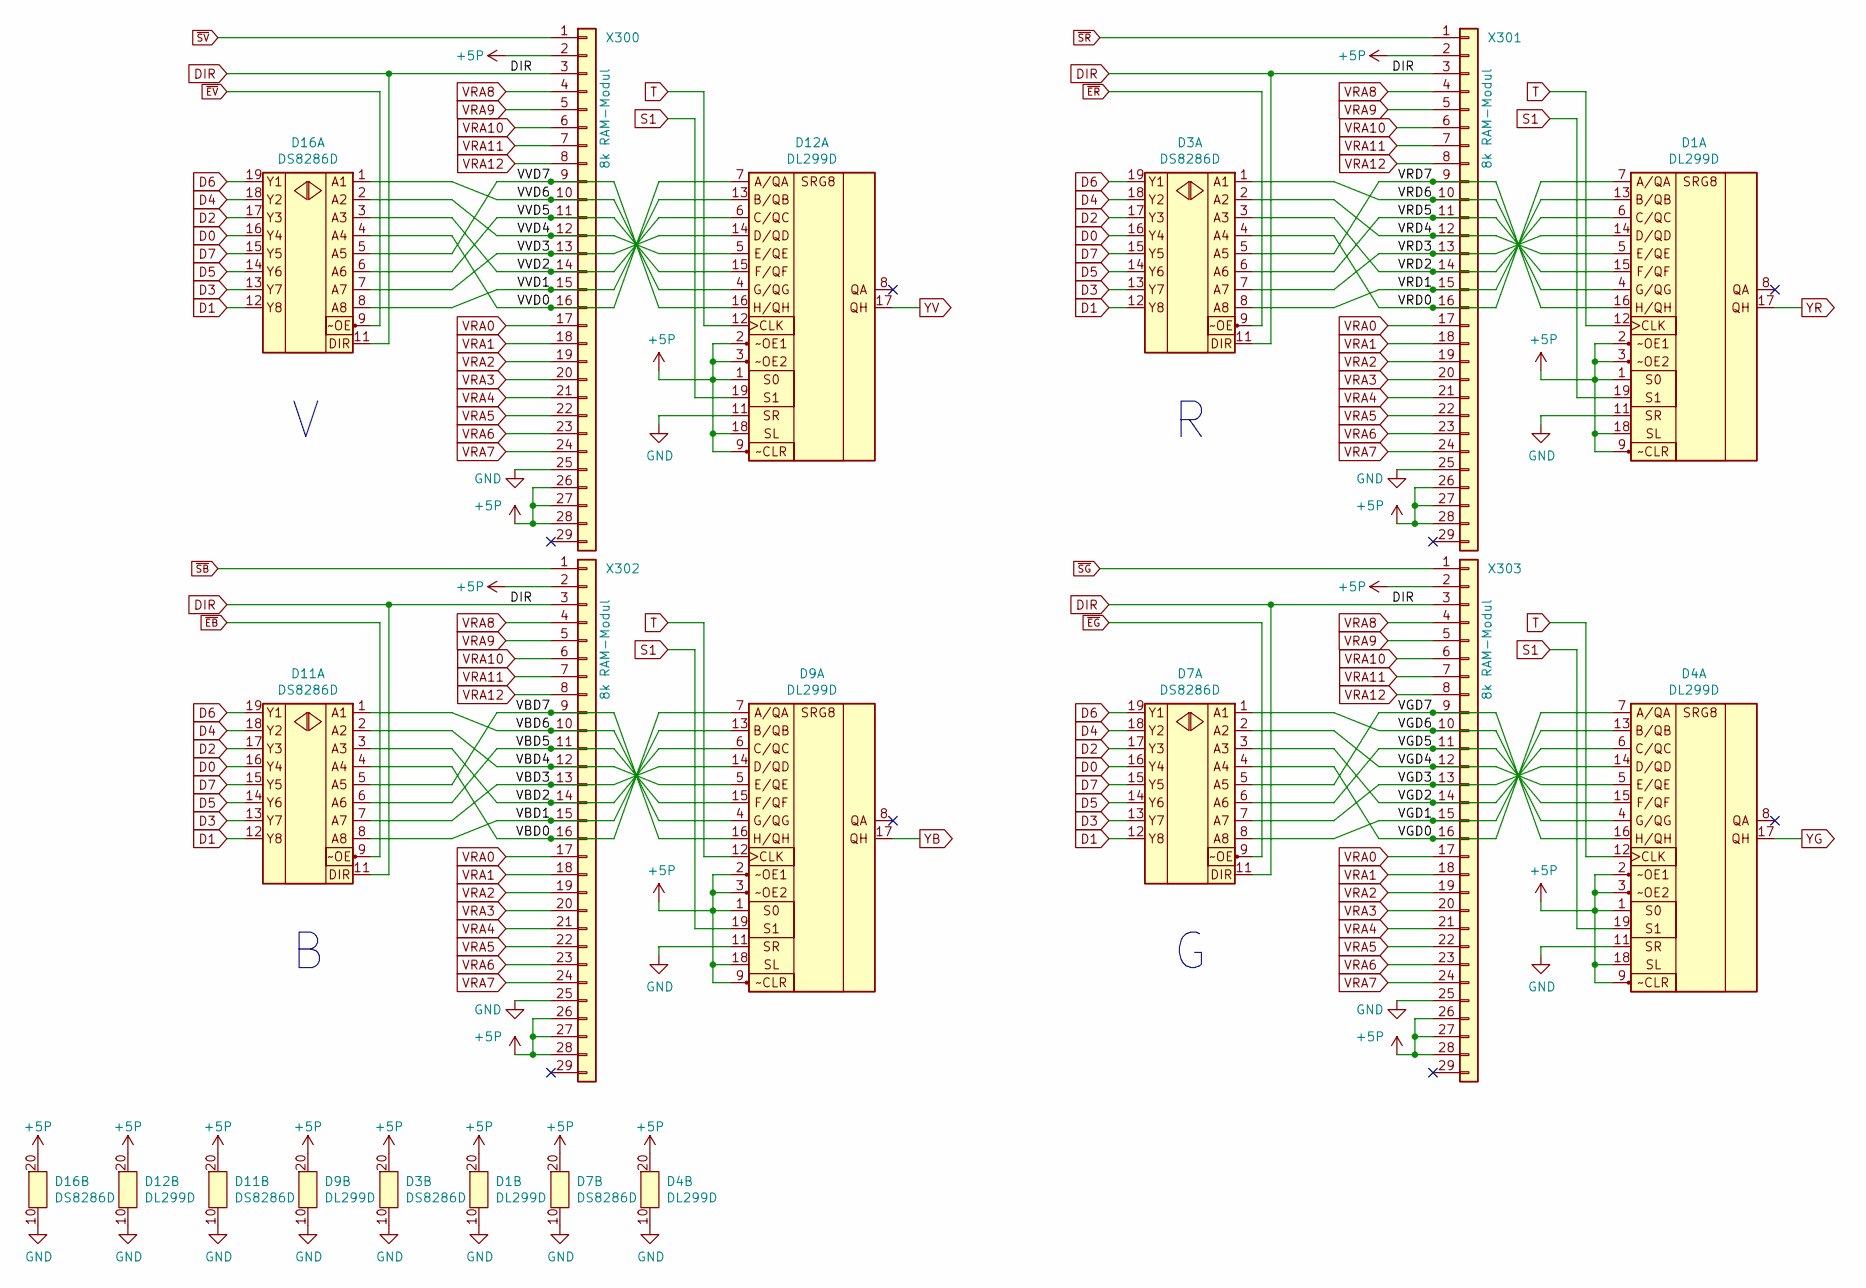
[picture p93: schematic Tiny6k_Steuerung_Video-RAM.sch]

Parts:
D1, D4, D9, D12: DL299D; DIP-20_W7.62mm_Socket_LongPads
D3, D7, D11, D16: DS8286D; DIP-20_W7.62mm_Socket_LongPads
X300, X301, X302, X303: 8k RAM-Modul; PinSocket_1x29_P2.54mm_Vertical

Connections:
+5P: D1.1 (S0), D1.2 (~OE1), D1.3 (~OE2), D1.9 (~CLR), D1.18 (SL), D1.20 (Vcc), D3.20 (Vcc), D4.1 (S0), D4.2 (~OE1), D4.3 (~OE2), D4.9 (~CLR), D4.18 (SL), D4.20 (Vcc), D7.20 (Vcc), D9.1 (S0), D9.2 (~OE1), D9.3 (~OE2), D9.9 (~CLR), D9.18 (SL), D9.20 (Vcc), D11.20 (Vcc), D12.1 (S0), D12.2 (~OE1), D12.3 (~OE2), D12.9 (~CLR), D12.18 (SL), D12.20 (Vcc), D16.20 (Vcc), X300.2, X300.26, X300.27, X300.28, X301.2, X301.26, X301.27, X301.28, X302.2, X302.26, X302.27, X302.28, X303.2, X303.26, X303.27, X303.28
D0: D3.16 (A4), D7.16 (A4), D11.16 (A4), D16.16 (A4)
D1: D3.12 (Y8), D7.12 (Y8), D11.12 (Y8), D16.12 (Y8)
D2: D3.17 (Y3), D7.17 (Y3), D11.17 (Y3), D16.17 (Y3)
D3: D3.13 (Y7), D7.13 (Y7), D11.13 (Y7), D16.13 (Y7)
D4: D3.18 (Y2), D7.18 (Y2), D11.18 (Y2), D16.18 (Y2)
D5: D3.14 (Y6), D7.14 (Y6), D11.14 (Y6), D16.14 (Y6)
D6: D3.19 (Y1), D7.19 (Y1), D11.19 (Y1), D16.19 (Y1)
D7: D3.15 (Y5), D7.15 (Y5), D11.15 (Y5), D16.15 (Y5)
DIR: D3.11 (STB), D7.11 (STB), D11.11 (STB), D16.11 (STB), X300.3, X301.3, X302.3, X303.3
GND: D1.10 (GND), D1.11 (SR), D3.10 (GND), D4.10 (GND), D4.11 (SR), D7.10 (GND), D9.10 (GND), D9.11 (SR), D11.10 (GND), D12.10 (GND), D12.11 (SR), D16.10 (GND), X300.25, X301.25, X302.25, X303.25
S1: D1.19 (S1), D4.19 (S1), D9.19 (S1), D12.19 (S1)
T: D1.12 (CLK), D4.12 (CLK), D9.12 (CLK), D12.12 (CLK)
VBD0: D9.7 (A/QA), D11.4 (A4), X302.16
VBD1: D9.13 (B/QB), D11.8 (A8), X302.15
VBD2: D9.6 (C/QC), D11.3 (A3), X302.14
VBD3: D9.14 (D/QD), D11.7 (A7), X302.13
VBD4: D9.5 (E/QE), D11.2 (A2), X302.12
VBD5: D9.15 (F/QF), D11.6 (A6), X302.11
VBD6: D9.4 (G/QG), D11.1 (A1), X302.10
VBD7: D9.16 (H/QH), D11.5 (A5), X302.9
VGD0: D4.7 (A/QA), D7.4 (A4), X303.16
VGD1: D4.13 (B/QB), D7.8 (A8), X303.15
VGD2: D4.6 (C/QC), D7.3 (A3), X303.14
VGD3: D4.14 (D/QD), D7.7 (A7), X303.13
VGD4: D4.5 (E/QE), D7.2 (A2), X303.12
VGD5: D4.15 (F/QF), D7.6 (A6), X303.11
VGD6: D4.4 (G/QG), D7.1 (A1), X303.10
VGD7: D4.16 (H/QH), D7.5 (A5), X303.9
VRA0: X300.17, X301.17, X302.17, X303.17
VRA1: X300.18, X301.18, X302.18, X303.18
VRA2: X300.19, X301.19, X302.19, X303.19
VRA3: X300.20, X301.20, X302.20, X303.20
VRA4: X300.21, X301.21, X302.21, X303.21
VRA5: X300.22, X301.22, X302.22, X303.22
VRA6: X300.23, X301.23, X302.23, X303.23
VRA7: X300.24, X301.24, X302.24, X303.24
VRA8: X300.4, X301.4, X302.4, X303.4
VRA9: X300.5, X301.5, X302.5, X303.5
VRA10: X300.6, X301.6, X302.6, X303.6
VRA11: X300.7, X301.7, X302.7, X303.7
VRA12: X300.8, X301.8, X302.8, X303.8
VRD0: D1.7 (A/QA), D3.4 (A4), X301.16
VRD1: D1.13 (B/QB), D3.8 (A8), X301.15
VRD2: D1.6 (C/QC), D3.3 (A3), X301.14
VRD3: D1.14 (D/QD), D3.7 (A7), X301.13
VRD4: D1.5 (E/QE), D3.2 (A2), X301.12
VRD5: D1.15 (F/QF), D3.6 (A6), X301.11
VRD6: D1.4 (G/QG), D3.1 (A1), X301.10
VRD7: D1.16 (H/QH), D3.5 (A5), X301.9
VVD0: D12.7 (A/QA), D16.4 (A4), X300.16
VVD1: D12.13 (B/QB), D16.8 (A8), X300.15
VVD2: D12.6 (C/QC), D16.3 (A3), X300.14
VVD3: D12.14 (D/QD), D16.7 (A7), X300.13
VVD4: D12.5 (E/QE), D16.2 (A2), X300.12
VVD5: D12.15 (F/QF), D16.6 (A6), X300.11
VVD6: D12.4 (G/QG), D16.1 (A1), X300.10
VVD7: D12.16 (H/QH), D16.5 (A5), X300.9
YB: D9.17 (QH)
YG: D4.17 (QH)
YR: D1.17 (QH)
YV: D12.17 (QH)
~EB: D11.9 (~OE)
~EG: D7.9 (~OE)
~ER: D3.9 (~OE)
~EV: D16.9 (~OE)
~SB: X302.1
~SG: X303.1
~SR: X301.1
~SV: X300.1
