boert/JU-TE-Computer/Tiny_6k/kicad/Tiny6k_Videoausgabe.sch

## KiCad design Tiny_6k/kicad/Tiny6k_Videoausgabe.sch (2021-11-27)

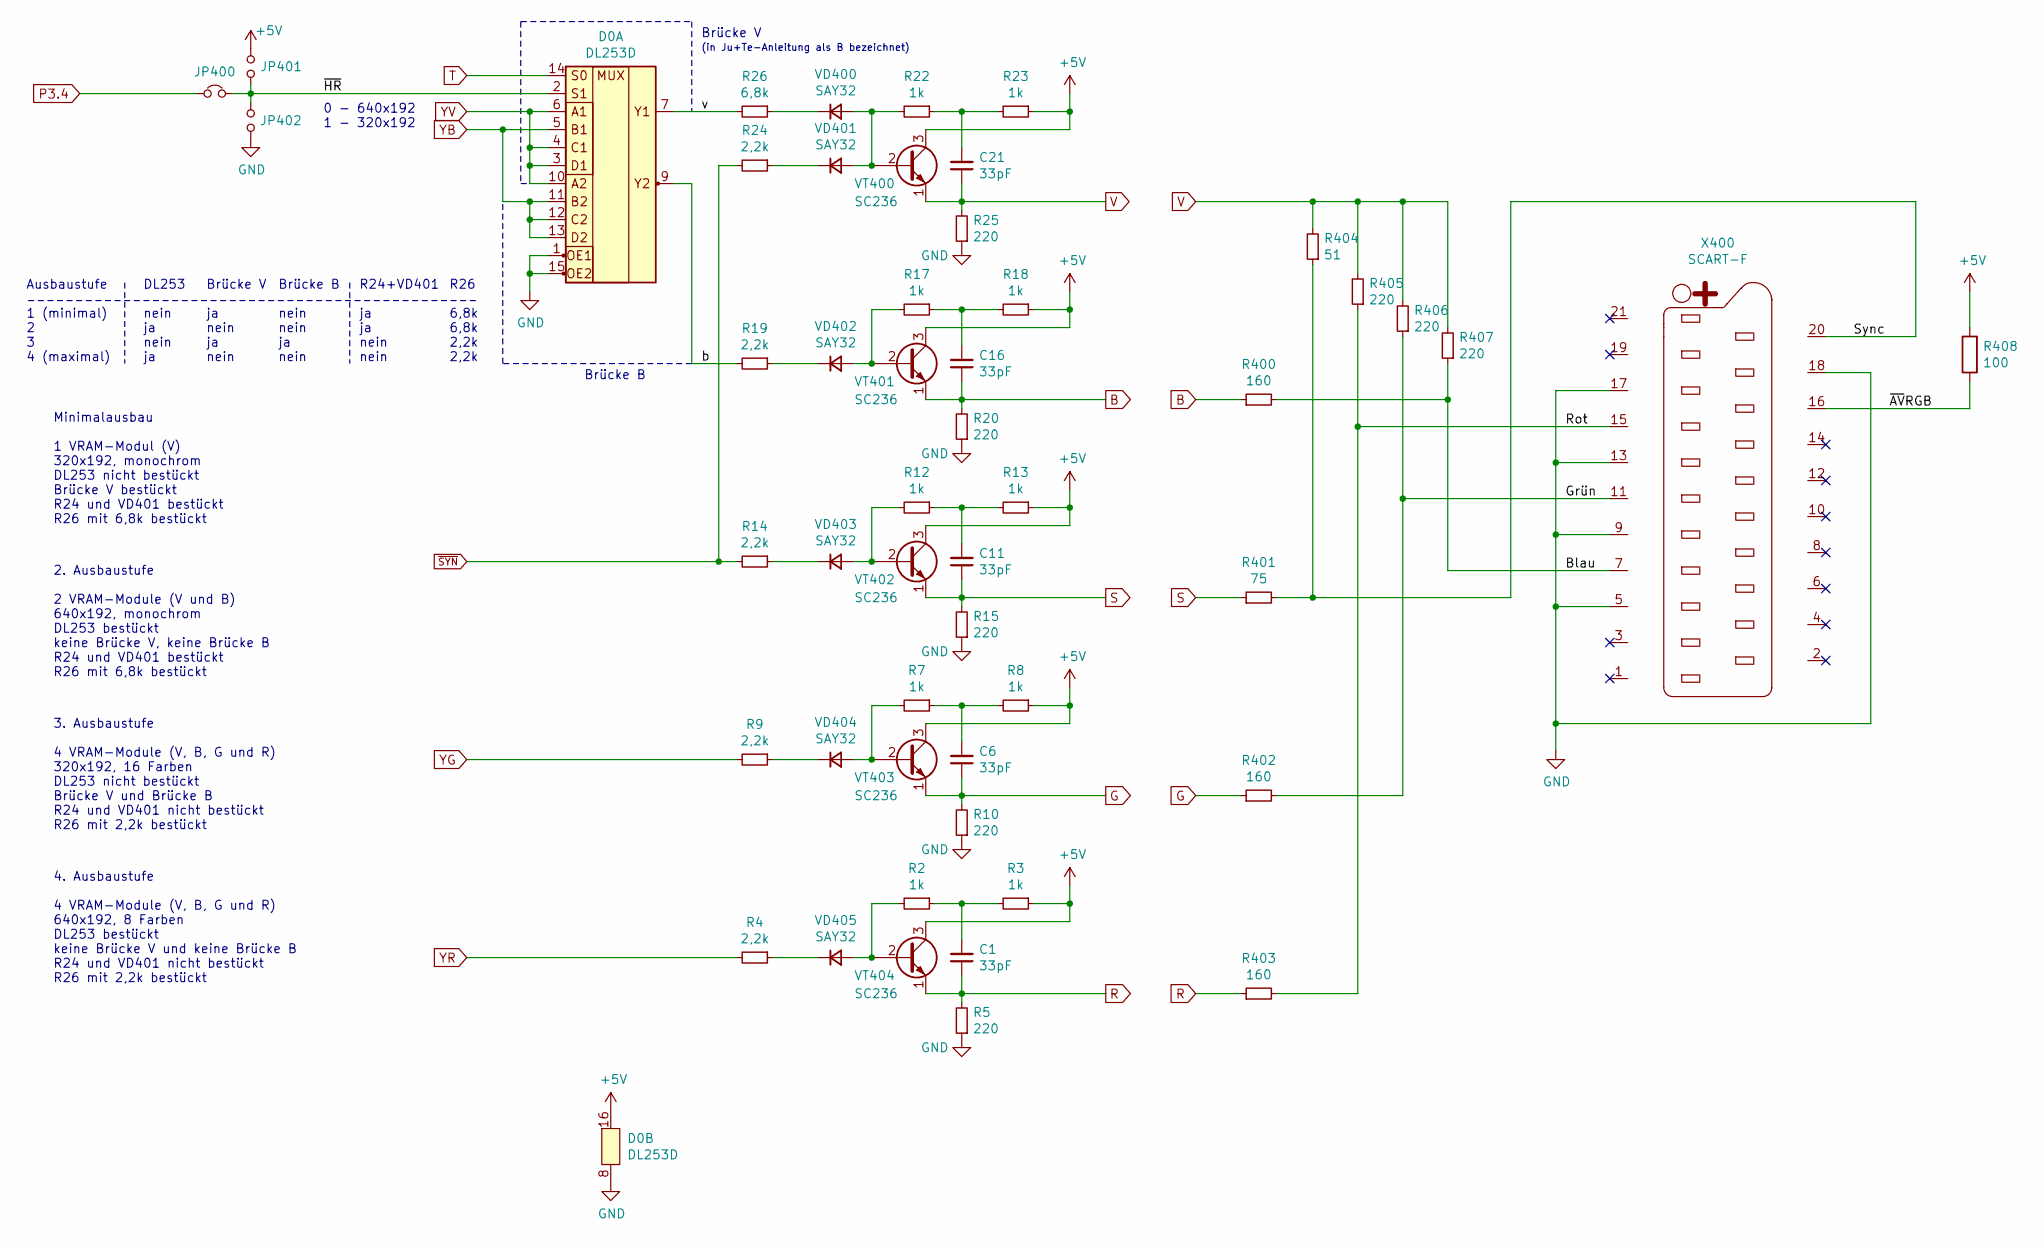
[picture p94: schematic Tiny6k_Videoausgabe.sch]

Parts:
C1, C6, C11, C16, C21: 33pF; C_Disc_D5.0mm_W2.5mm_P2.50mm
D0: DL253D; DIP-16_W7.62mm_Socket_LongPads
JP400: HR direkt; PinHeader_1x02_P2.54mm_Vertical
JP401: HR_VCC; PinHeader_1x02_P2.54mm_Vertical
JP402: HR_GND; PinHeader_1x02_P2.54mm_Vertical
R2, R3, R7, R8, R12, R13, R17, R18, R22, R23: 1k; R_Axial_DIN0309_L9.0mm_D3.2mm_P2.54mm_Vertical
R4, R9, R14, R19, R24: 2,2k; R_Axial_DIN0309_L9.0mm_D3.2mm_P2.54mm_Vertical
R5, R10, R15, R20, R25, R405, R406, R407: 220; R_Axial_DIN0207_L6.3mm_D2.5mm_P10.16mm_Horizontal
R26: 6,8k; R_Axial_DIN0309_L9.0mm_D3.2mm_P2.54mm_Vertical
R400, R402, R403: 160; R_Axial_DIN0207_L6.3mm_D2.5mm_P10.16mm_Horizontal
R401: 75; R_Axial_DIN0207_L6.3mm_D2.5mm_P10.16mm_Horizontal
R404: 51; R_Axial_DIN0207_L6.3mm_D2.5mm_P10.16mm_Horizontal
R408: 100; R_Axial_DIN0207_L6.3mm_D2.5mm_P10.16mm_Horizontal
VD400, VD401, VD402, VD403, VD404, VD405: SAY32; D_DO-34_SOD68_P2.54mm_Vertical_AnodeUp
VT400, VT401, VT402, VT403, VT404: SC236; TO-92Flat
X400: SCART-F; PinHeader_1x21_P2.54mm_Vertical

Connections:
+5V: D0.16 (Vcc), JP401.1, R3.1, R8.1, R13.1, R18.1, R23.1, R408.2, VT400.3 (C), VT401.3 (C), VT402.3 (C), VT403.3 (C), VT404.3 (C)
Blau: R400.2, R407.1, X400.7
G: C6.1, R10.2, R402.1, VT403.1 (E)
GND: D0.1 (~OE1), D0.8 (GND), D0.15 (~OE2), JP402.2, R5.1, R10.1, R15.1, R20.1, R25.1, X400.5, X400.9, X400.13, X400.17, X400.18
Grün: R402.2, R406.1, X400.11
unnamed: C1.2, R2.1, R3.2
unnamed: C6.2, R7.1, R8.2
unnamed: C11.2, R12.1, R13.2
unnamed: C16.2, R17.1, R18.2
unnamed: C21.2, R22.1, R23.2
unnamed: R2.2, VD405.2 (A), VT404.2 (B)
unnamed: R4.1, VD405.1 (K)
unnamed: R7.2, VD404.2 (A), VT403.2 (B)
unnamed: R9.1, VD404.1 (K)
unnamed: R12.2, VD403.2 (A), VT402.2 (B)
unnamed: R14.1, VD403.1 (K)
unnamed: R17.2, VD402.2 (A), VT401.2 (B)
unnamed: R19.1, VD402.1 (K)
unnamed: R22.2, VD400.2 (A), VD401.2 (A), VT400.2 (B)
unnamed: R24.1, VD401.1 (K)
unnamed: R26.1, VD400.1 (K)
P3.4: JP400.1
R: C1.1, R5.2, R403.1, VT404.1 (E)
Rot: R403.2, R405.1, X400.15
S: C11.1, R15.2, R401.1, VT402.1 (E)
Sync: R401.2, R404.1, X400.20
T: D0.14 (S0)
YB: D0.5 (B1), D0.11 (B2), D0.12 (C2), D0.13 (D2)
YG: R9.2
YR: R4.2
YV: D0.3 (D1), D0.4 (C1), D0.6 (A1), D0.10 (A2)
b: C16.1, D0.9 (2Y), R19.2, R20.2, R400.1, VT401.1 (E)
v: C21.1, D0.7 (1Y), R25.2, R26.2, R404.2, R405.2, R406.2, R407.2, VT400.1 (E)
~AV~RGB: R408.1, X400.16
~HR: D0.2 (S1), JP400.2, JP401.2, JP402.1
~SYN: R14.2, R24.2

Notes on the sheet:
Brücke B
Brücke V
DL253 nein ja nein ja
Ausbaustufe 1 (minimal) 2 3 4 (maximal)
Brücke V ja nein ja nein
Brücke B nein nein ja nein
R26 6,8k 6,8k 2,2k 2,2k
0 - 640x192 1 - 320x192
(in Ju+Te-Anleitung als B bezeichnet)
2. Ausbaustufe 2 VRAM-Module (V und B) 640x192, monochrom DL253 bestückt keine Brücke V, keine Brücke B R24 und VD401 bestückt R26 mit 6,8k bestückt
3. Ausbaustufe 4 VRAM-Module (V, B, G und R) 320x192, 16 Farben DL253 nicht bestückt Brücke V und Brücke B R24 und VD401 nicht bestückt R26 mit 2,2k bestückt
4. Ausbaustufe 4 VRAM-Module (V, B, G und R) 640x192, 8 Farben DL253 bestückt keine Brücke V und keine Brücke B R24 und VD401 nicht bestückt R26 mit 2,2k bestückt
Minimalausbau 1 VRAM-Modul (V) 320x192, monochrom DL253 nicht bestückt Brücke V bestückt R24 und VD401 bestückt R26 mit 6,8k bestückt
R24+VD401 ja ja nein nein
