boert/JU-TE-Computer/Tiny_6k/kicad/Tiny6k_Videoprozessor.sch

## KiCad design Tiny_6k/kicad/Tiny6k_Videoprozessor.sch (2021-11-27)

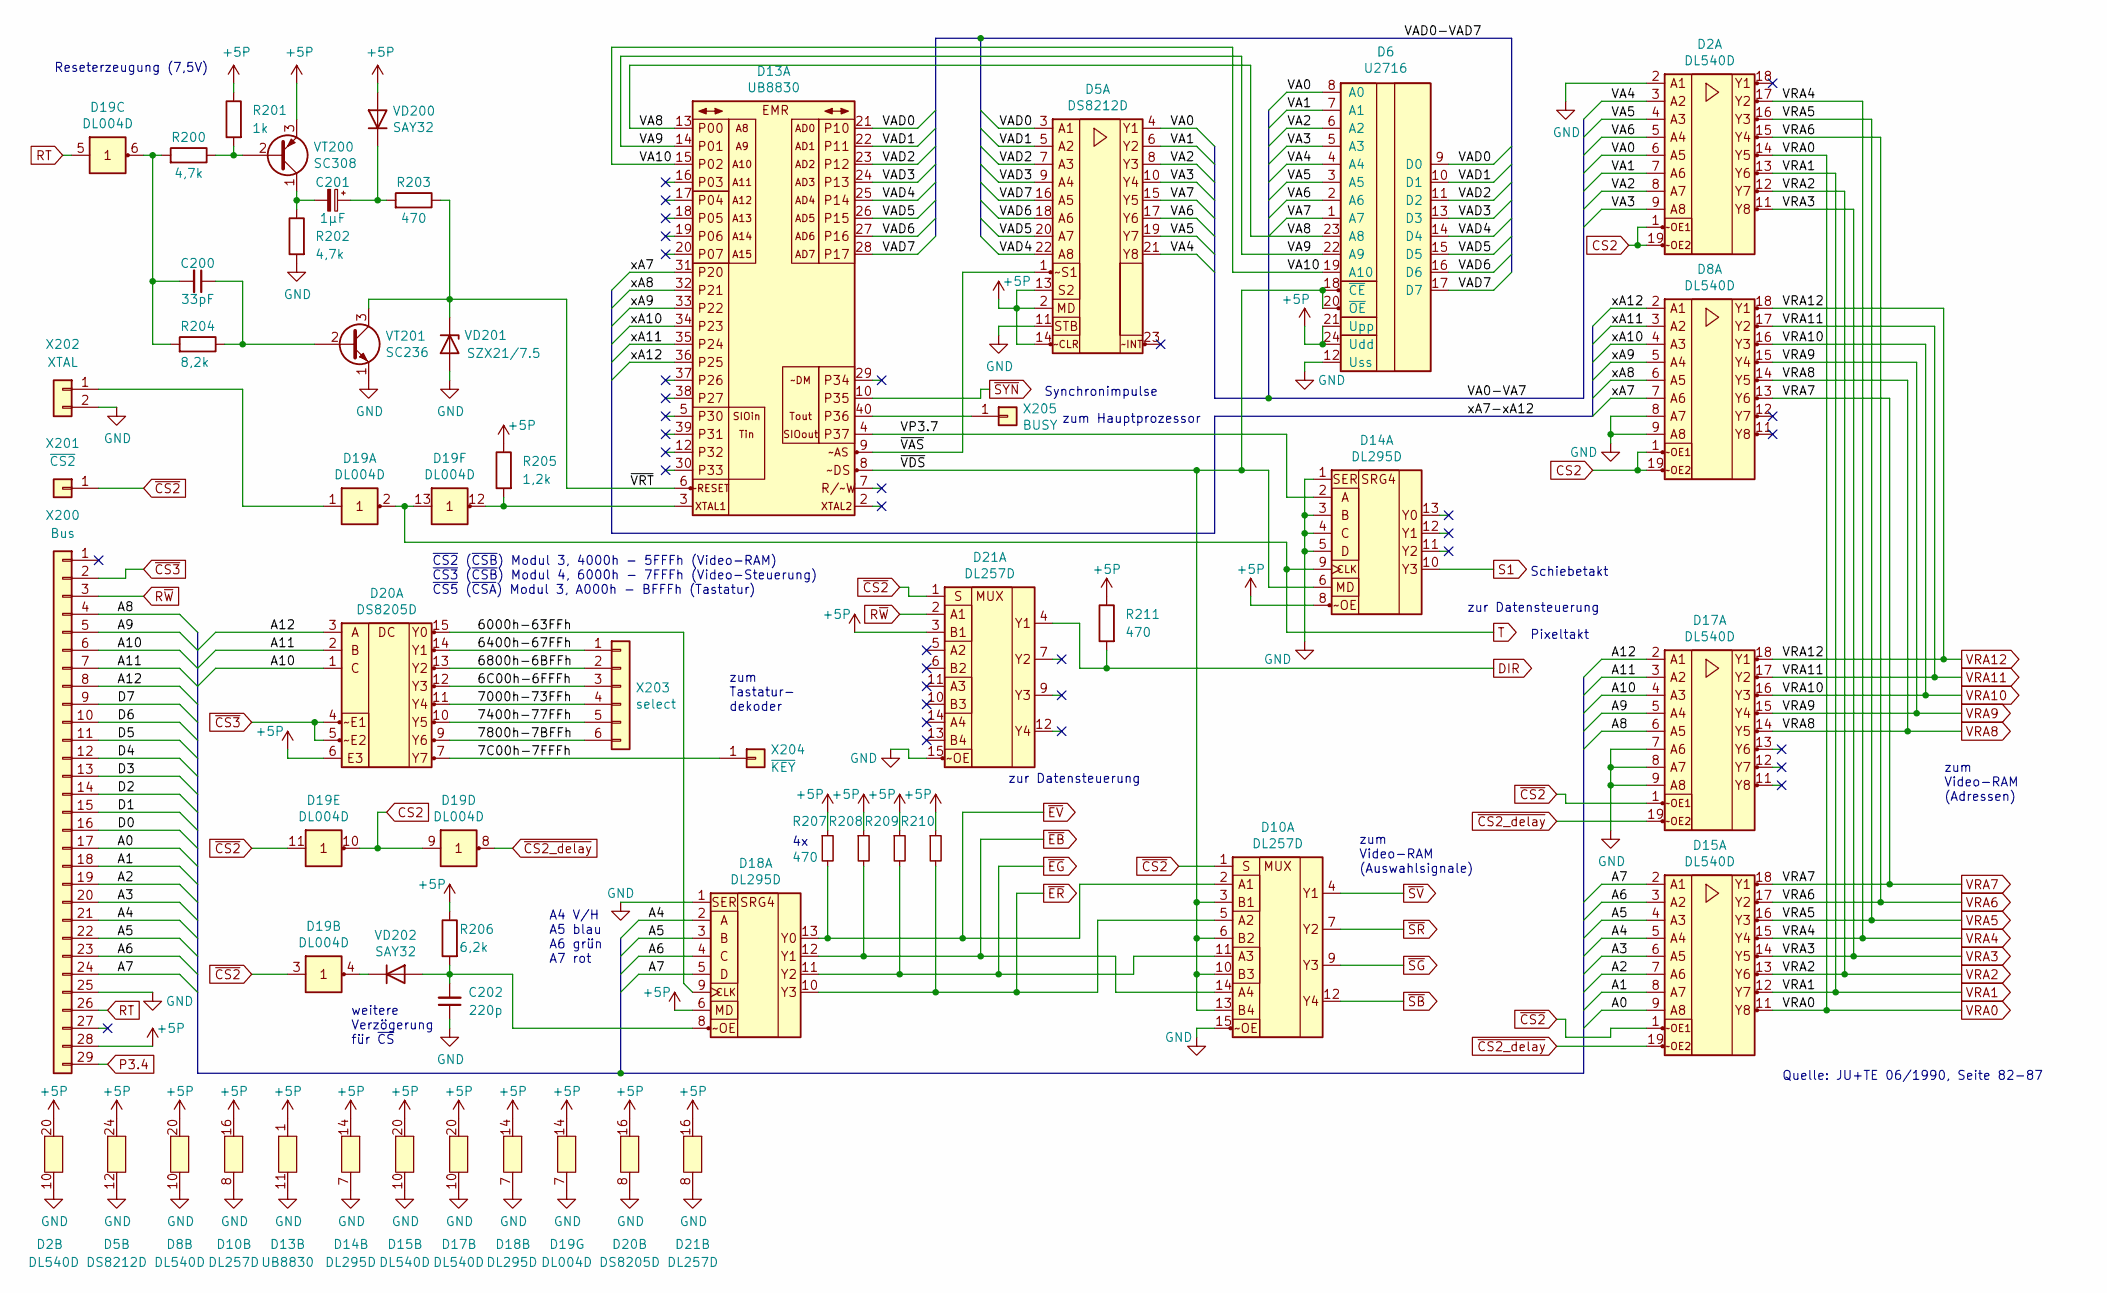
[picture p95: schematic Tiny6k_Videoprozessor.sch]

Parts:
C200: 33pF; C_Disc_D4.7mm_W2.5mm_P5.00mm
C201: 1µF; CP_Radial_D5.0mm_P2.50mm
C202: 220p; C_Disc_D5.0mm_W2.5mm_P2.50mm
D2, D8, D15, D17: DL540D; DIP-20_W7.62mm_Socket_LongPads
D5: DS8212D; DIP-24_W15.24mm_Socket_LongPads
D6: U2716; DIP-24_W15.24mm_Socket_LongPads
D10, D21: DL257D; DIP-16_W7.62mm_Socket_LongPads
D13: UB8830; DIP-40_W15.24mm_Socket_LongPads
D14, D18: DL295D; DIP-14_W7.62mm_Socket_LongPads
D19: DL004D; DIP-14_W7.62mm_Socket_LongPads
D20: DS8205D; DIP-16_W7.62mm_Socket_LongPads
R200, R202: 4,7k; R_Axial_DIN0207_L6.3mm_D2.5mm_P10.16mm_Horizontal
R201: 1k; R_Axial_DIN0207_L6.3mm_D2.5mm_P10.16mm_Horizontal
R203, R207, R208, R209, R210, R211: 470; R_Axial_DIN0207_L6.3mm_D2.5mm_P10.16mm_Horizontal
R204: 8,2k; R_Axial_DIN0207_L6.3mm_D2.5mm_P10.16mm_Horizontal
R205: 1,2k; R_Axial_DIN0207_L6.3mm_D2.5mm_P10.16mm_Horizontal
R206: 6,2k; R_Axial_DIN0207_L6.3mm_D2.5mm_P10.16mm_Horizontal
VD200, VD202: SAY32; D_DO-34_SOD68_P2.54mm_Vertical_AnodeUp
VD201: SZX21/7.5; D_DO-34_SOD68_P2.54mm_Vertical_AnodeUp
VT200: SC308; TO-92Flat
VT201: SC236; TO-92Flat
X200: Bus; PinHeader_1x29_P2.54mm_Horizontal
X201: ~CS2; PinHeader_1x01_P2.54mm_Horizontal
X202: XTAL; PinHeader_1x02_P2.54mm_Vertical
X203: select; PinHeader_1x06_P2.54mm_Vertical
X204: ~KEY; PinHeader_1x01_P2.54mm_Horizontal
X205: BUSY; PinHeader_1x01_P2.54mm_Horizontal

Connections:
6C00h-6FFFh: D20.12 (Y3), X203.3
7C00h-7FFFh: D20.7 (Y7), X204.1
6000h-63FFh: D18.9 (CLK), D20.15 (Y0)
6400h-67FFh: D20.14 (Y1), X203.1
6800h-6BFFh: D20.13 (Y2), X203.2
7000h-73FFh: D20.11 (Y4), X203.4
7400h-77FFh: D20.10 (Y5), X203.5
7800h-7BFFh: D20.9 (Y6), X203.6
+5P: D2.20 (Vcc), D5.2 (MD), D5.13 (S2), D5.14 (~CLR), D5.24 (Vcc), D6.21 (Upp), D6.24 (Udd), D8.20 (Vcc), D10.16 (Vcc), D13.1 (Vcc), D14.8 (~OE), D14.14 (Vcc), D15.20 (Vcc), D17.20 (Vcc), D18.6 (MODE), D18.14 (Vcc), D19.14 (Vcc), D20.6 (E3), D20.16 (Vcc), D21.3 (B1), D21.16 (Vcc), R201.1, R205.1, R206.1, R207.1, R208.1, R209.1, R210.1, R211.1, VD200.2 (A), VT200.3 (E), X200.28
A0: D15.9 (A8), X200.17
A1: D15.8 (A7), X200.18
A2: D15.7 (A6), X200.19
A3: D15.6 (A5), X200.20
A4: D15.5 (A4), D18.2 (A), X200.21
A5: D15.4 (A3), D18.3 (B), X200.22
A6: D15.3 (A2), D18.4 (C), X200.23
A7: D15.2 (A1), D18.5 (D), X200.24
A8: D17.6 (A5), X200.4
A9: D17.5 (A4), X200.5
A10: D17.4 (A3), D20.1 (C), X200.6
A11: D17.3 (A2), D20.2 (B), X200.7
A12: D17.2 (A1), D20.3 (A), X200.8
CS2: D2.1 (OE1), D2.19 (~OE2), D8.1 (OE1), D8.19 (~OE2), D19.9 (A4), D19.10 (Y5)
D0: X200.16
D1: X200.15
D2: X200.14
D3: X200.13
D4: X200.12
D5: X200.11
D6: X200.10
D7: X200.9
DIR: D21.4 (Y1), R211.2
GND: C202.1, D2.2 (A1), D2.10 (GND), D5.11 (STB), D5.12 (GND), D6.12 (Uss), D8.8 (A7), D8.9 (A8), D8.10 (GND), D10.8 (GND), D10.15 (~OE), D13.11 (GND), D14.1 (SER), D14.3 (B), D14.4 (C), D14.5 (D), D14.7 (GND), D15.10 (GND), D17.7 (A6), D17.8 (A7), D17.9 (A8), D17.10 (GND), D18.1 (SER), D18.7 (GND), D19.7 (GND), D20.8 (GND), D21.8 (GND), D21.15 (~OE), R202.2, VD201.2 (A), VT201.1 (E), X200.25, X202.2
unnamed: C200.1, R204.1, VT201.2 (B)
unnamed: C200.2, D19.6 (Y3), R200.2, R204.2
unnamed: C201.1, R203.2, VD200.1 (K)
unnamed: C201.2, R202.1, VT200.1 (C)
unnamed: C202.2, D18.8 (~OE), R206.2, VD202.2 (A)
unnamed: D13.3 (XTAL1), D19.12 (Y6), R205.2
unnamed: D13.40 (P36), X205.1
unnamed: D19.1 (A1), X202.1
unnamed: D19.4 (Y2), VD202.1 (K)
unnamed: R200.1, R201.2, VT200.2 (B)
P3.4: X200.29
RT: D19.5 (A3), X200.26
R~W: D21.2 (A1), X200.3
S1: D14.10 (Y3)
T: D14.9 (CLK), D19.2 (Y1), D19.13 (A6)
VA0: D2.6 (A5), D5.4 (Y1), D6.8 (A0)
VA1: D2.7 (A6), D5.6 (Y2), D6.7 (A1)
VA2: D2.8 (A7), D5.8 (Y3), D6.6 (A2)
VA3: D2.9 (A8), D5.10 (A4), D6.5 (A3)
VA4: D2.3 (A2), D5.21 (Y8), D6.4 (A4)
VA5: D2.4 (A3), D5.19 (Y7), D6.3 (A5)
VA6: D2.5 (A4), D5.17 (Y6), D6.2 (A6)
VA7: D5.15 (Y5), D6.1 (A7)
VA8: D6.23 (A8), D13.13 (P00)
VA9: D6.22 (A9), D13.14 (P01)
VA10: D6.19 (A10), D13.15 (P02)
VAD0: D5.3 (A1), D6.9 (D0), D13.21 (P10)
VAD1: D5.5 (A2), D6.10 (D1), D13.22 (P11)
VAD2: D5.7 (A3), D6.11 (D2), D13.23 (P12)
VAD3: D5.9 (A4), D6.13 (D3), D13.24 (P13)
VAD4: D5.22 (A8), D6.14 (D4), D13.25 (P14)
VAD5: D5.20 (A7), D6.15 (D5), D13.26 (P15)
VAD6: D5.18 (A6), D6.16 (D6), D13.27 (P16)
VAD7: D5.16 (A5), D6.17 (D7), D13.28 (P17)
VP3.7: D13.4 (P37), D14.2 (A)
VRA0: D2.14 (Y5), D15.11 (Y8)
VRA1: D2.13 (Y6), D15.12 (Y7)
VRA2: D2.12 (Y7), D15.13 (Y6)
VRA3: D2.11 (Y8), D15.14 (Y5)
VRA4: D2.17 (Y2), D15.15 (A4)
VRA5: D2.16 (Y3), D15.16 (Y3)
VRA6: D2.15 (A4), D15.17 (Y2)
VRA7: D8.13 (Y6), D15.18 (Y1)
VRA8: D8.14 (Y5), D17.14 (Y5)
VRA9: D8.15 (A4), D17.15 (A4)
VRA10: D8.16 (Y3), D17.16 (Y3)
VRA11: D8.17 (Y2), D17.17 (Y2)
VRA12: D8.18 (Y1), D17.18 (Y1)
xA7: D8.7 (A6), D13.31 (P20)
xA8: D8.6 (A5), D13.32 (P21)
xA9: D8.5 (A4), D13.33 (P22)
xA10: D8.4 (A3), D13.34 (P23)
xA11: D8.3 (A2), D13.35 (P24)
xA12: D8.2 (A1), D13.36 (P25)
~CS2: D10.1 (S), D15.1 (OE1), D17.1 (OE1), D19.3 (A2), D19.11 (A5), D21.1 (S), X201.1
~CS2_delay: D15.19 (~OE2), D17.19 (~OE2), D19.8 (Y4)
~CS3: D20.4 (~E1), D20.5 (~E2), X200.2
~EB: D10.14 (A4), D18.12 (Y1), R208.2
~EG: D10.11 (A3), D18.11 (Y2), R209.2
~ER: D10.5 (A2), D18.10 (Y3), R210.2
~EV: D10.2 (A1), D18.13 (Y0), R207.2
~SB: D10.12 (4Y)
~SG: D10.9 (Y3)
~SR: D10.7 (Y2)
~SV: D10.4 (Y1)
~SYN: D13.10 (P35)
~VAS: D5.1 (~S1), D13.9 (~AS)
~VDS: D6.18 (~CE), D6.20 (~OE), D10.3 (B1), D10.6 (B2), D10.10 (B3), D10.13 (B4), D13.8 (~DS), D14.6 (MODE)
~VRT: D13.6 (~RESET), R203.1, VD201.1 (K), VT201.3 (C)

Notes on the sheet:
Quelle: JU+TE 06/1990, Seite 82-87
~CS2~ (~CSB~) Modul 3, 4000h - 5FFFh (Video-RAM) ~CS3~ (~CSB~) Modul 4, 6000h - 7FFFh (Video-Steuerung) ~CS5~ (~CSA~) Modul 3, A000h - BFFFh (Tastatur)
zum Video-RAM (Adressen)
zur Datensteuerung
zum Video-RAM (Auswahlsignale)
Reseterzeugung (7,5V)
weitere Verzögerung für ~CS
zum Tastatur- dekoder
zum Hauptprozessor
Schiebetakt
Synchronimpulse
Pixeltakt
A4 V/H A5 blau A6 grün A7 rot
